makerjawn/oneKey/Documentation/indd/Links/10894171994_1b0bc88e4c_z.jpg

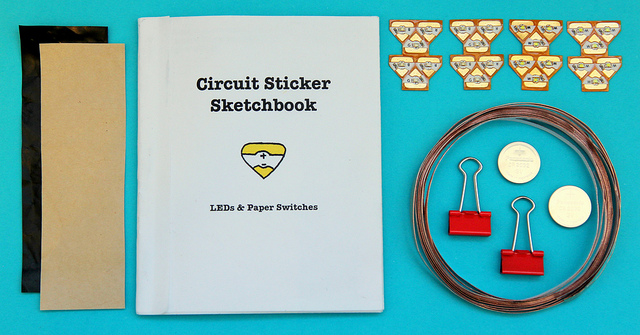
Documentation/indd/Links/10894171994_1b0bc88e4c_z.jpg
