makerjawn/oneKey/Documentation/Presentation_Intro_Handout.pdf

Case, Amber. An Illustrated Dictionary of Cyborg Anthropology. N.p.: n.p., n.d. Http:// cyborganthropology.com/store/. Web.
Dewey, John. Experience and Education. New York: Macmillan, 1938. Print.
Anderson, Chris. Makers: The New Industrial Revolution. New York: Crown Business, 2012. Print. Rushkoff, Douglas, and Leland Purvis. Program or Be Programmed: Ten Commands for a Digital Age. Berkeley, CA: Soft Skull, 2011. Print.
Brosterman, Norman, and Togashi. Inventing Kindergarten. [New York, N.Y.]: H.N. Abrams, 1997. Print.
Murakami, Haruki, and Jay Rubin. Norwegian Wood. New York: Vintage International, 2000. Print. Plowman, Lydia, Christine Stephen, and Joanna McPake. Growing up with Technology: Young Children Learning in a Digital World. London: Routledge, 2010. Print.
,W 0L]XNR +DQJLQJ 2XW 0HVVLQJ $URXQG DQG *HHNLQJ 2XW .LGV /LYLQJ DQG /HDUQLQJ ZLWK 1HZ Media. Cambridge, MA: MIT, 2010. Print.
1LOVVRQ (OLVDEHW 0 7KH 0DNLQJ RI D 0DNHUVSDFH IRU 2SHQ ,QQRYDWLRQ .QRZOHGJH 6KDULQJ DQG Peer-to-peer Learning." FUTURE LEARNING SPACES. Helsinki: Aalto University, 2011. 293-98. Print.
| Petrovich, Dushko, and Roger White. Draw It with Your Eyes Closed: The Art of the Art
Assignment. Brooklyn, NY: Paper Monument, 2012. Print.
| Allen, Felicity. Education. London: Whitechapel Gallery, 2011. Print.

https://pittsburghkids.org/exhibits/makeshophttp://www.libraryasincubatorproject.org/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

# Playing, Learning, and Making things light-up in

City of Brotherly Love and Sisterly Affection.

# To encourage exploration with, making of, and

collaboration on electronic interactives.

# MakerJawn

# IDES 431

bk

31 | 7 | 14

### Map comparison of online

resources/curriculum.

Reconnect with MESS Hall,
talk about new kits.

### Develop own curriculum based

on summer learning.

### Reevaluate summer blog and

feedback on tools.

### Run curriculum by Kenny and

K-Fai.

### Talk to Ann about implementing check-out/cart

### Make sketch kits, let them

be explored.

### 2EVHUYH NLW RU FDUW XVDJH

### Interview volunteers about

what they see in its usage.

### Condense “curriculum” into

kit interactives.

### Make report for proof of

concept / needed actions.

# timeline / actions

# works cited / resources

### Access existing kits at the library. (Boardgames, etc)

## Digital Media afterschool programming and workshops for

youth at the Free Library of Philadelphia.

keywords
connected learning, digital literacy, electronics, making, maker, library, resources, underserved, after-school, teens, programming, computing, technology, understanding, play, H[SORUDWLRQ ZRUNVKRSV HWH[WLOHV FUDIWLQJ DW WHDFKLQJ guided learning, participatory design, eorigami, hi-low tech, PLW PDNHUHG GLJLWDO PHGLD LQWHUQHW SURFLHQF\ VKDULQJ collaborating, exposure, computation, programming, kids, youth, arts, craft, empowering, failure, fabrication labs, fab labs, maker spaces, institutions, kit based.

NH\WHUPVGHQHG
electronic interactive - a digital media installation, ranging from a game, to a sculpture, or art work, XWLOL]LQJ HOHFWURQLFV DQG NQRZOHGJH RI FLUFXLWU\ DQG RU programming logic and syntax.
NLW D VHW RI SDUWV RU WKLQJV IRU D VSHFLF SXUSRVH framework - structure
scaffolding learning - to tier or create stepping stones so concepts and knowledge can be built upon within a learning environment.
HASTAC - Humanities, Arts, Science and Technology Advanced Collaboratory

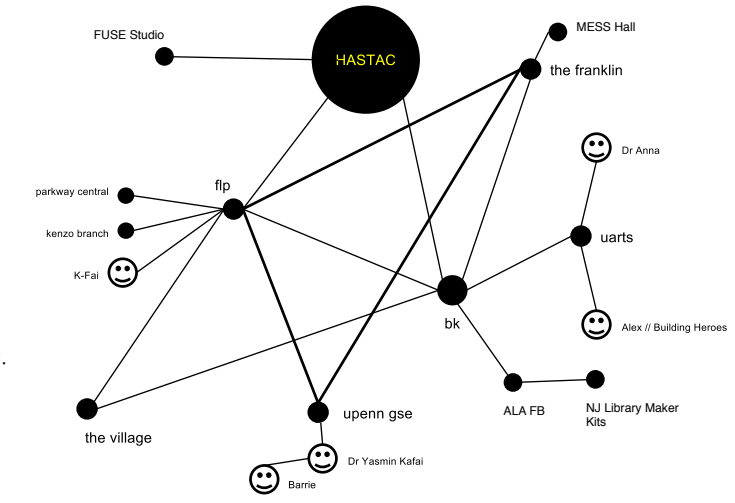
[picture p3: figure]
ALA FB; MESS Hall FUSE Studio; NJ Library Maker Kits

OLEUDU\PDNHUSUROHV | OLWHUDU\UHYLHZQGLQJV

# SUHFHGHQWNLWV

MESS Kits
“Single-serving
experiments that allow
NLGV WR H[SORUH VFLHQWLF
concepts at their own
pace.” Checked out and
updated frequently with
simple chemistry, physics, and crafts projects.

Sparkfun
Nationally tested and
XWLOL]HG FXUULFXOXP IRU
scafolding learning with
regards to electronics,
physical computing, and
programming.

Fuse Studio
2QOLQH GURSLQ
model, inquiry based,
STEAM(Science,
Technology, Engineering,
Arts, and Math) centric
design-build challenges.
Free to the public, sans
physical project materials.

NJ Maker Kits
Three kits ranging
from button makers to
MakeyMakeys. Can be
checked out at branches,
comes with minimal
guidance for branch users
other than online product
guides.

In order to make a framework for scafolding the learning of youth at the library a FXUULFXOXP RI VRUWV PXVW EH ZRUNHG RXW $V VSHFLFDOO\ PRGHOHG E\ 0(66 NLWV DQG FUSE Studio they do not have to be completed sequentially.

Sparkfun on the otherhand has a very linear approach to its lessonplans, one may H[SORUH LQWHUHVWLQJ FRPSRQHQWV RU SLHFHV RI WKH SX]]OH MXVW OLNH /LJKW8S +RZHYHU if exploration occurs in these platforms their preplanned linear execution is QXOOLHG

These precedents can be remixed and mashed-up to work within the library, KRZHYHU WKH\UH QRW WDLORUHG WRZDUGV WKH VSHFLF FRQWH[WV DQG HQYLURQPHQWV WKH library has to offer.

In my readings I have found that youth are bound to be creative and explore concepts through unrestricted play. In the context of the library I must be sensitive to how the community, family, and actual child view and interact with technology and electronics. Their own thoughts will completely differ from mine when it comes to its use for , entertainment, etc. The beauty of digital media is that it is able to freely move around, which can either allow for easy entertainment or HVFDSH RU XLG WUDQVIHU RI LGHDV DQG SURMHFW VKDULQJ , KDYH DOVR OHDUQHG WR VSHFLFDOO\ FDWHJRUL]H QRW RQO\ the needs or ways in which youth learn(inquiry based, play, directed learning, etc), but also their involvement in the programming.

As stated in Ito, there are three primary ways in which kids will align with digital media programming. They can either just hang out DQG VRFLDOL]H mess around with what is being worked on, or they can totally latch on to the project and geek out ZKLOH FRQWULEXWLQJ WR D QDO solution.

Jacob
13 years old
“The Boss”
// Self-directed tinkerer
// Geeking out
Mykal
9 Years old
“the best student”
// Needs guidance
// Messing around
Donnie
10 years old
“gamer”
// Self-directed
// Hanging out
Star
11 years old
“maker + doer”
// Self Directed
0HVVLQJ $URXQG DQG +DQJLQJ 2XW

# P\SRVLWLRQDWS

# SUHFHGHQWSUHYLRXVO\WHVWHGWKRXJKWV

Possibility Box
A box full of projects
chosen by MAKER.ED of
MAKE media for mentors to
explore with students. An
unfocused set of basics.

# OLEUDU\VWUXFWXUHYRWKHUPHWKRGV

&RQQHFWHG0HVVDJHV
A collaborative, multiple
location, interactive mural project completed at the
library over the Summer
‘13.

MakeyMakey Mazes
A gateway from simple
circuitry to basic
programming with magnets
and playdoh.

# SUHFHGHQWLQWHUDFWLYHFROODERUDWLRQV

Maker Celebration Games
A set of games made for
3L]]D%UDLQ DQG /LWWOH%DE\V for the maker celebration
in collaboration with kids at the Village.

ECrafting

GSE Grads

TOPPS

MakerJawn

Teen
Programming
Specialists

Hot Spots

Maker
Mentors
I am currently a Maker Mentor underneath the Teen 2ULHQWHG 3URJUDPPLQJ JURXS KRXVHG DW WKH )UHH /LEUDU\ I am a direct link between Programming Specialists and other Mentors and interested parties at the library. I bring technical knowledge and critical feedback via implementing and testing progams and workshops.
As well as HASTAC scholar and collaborator.

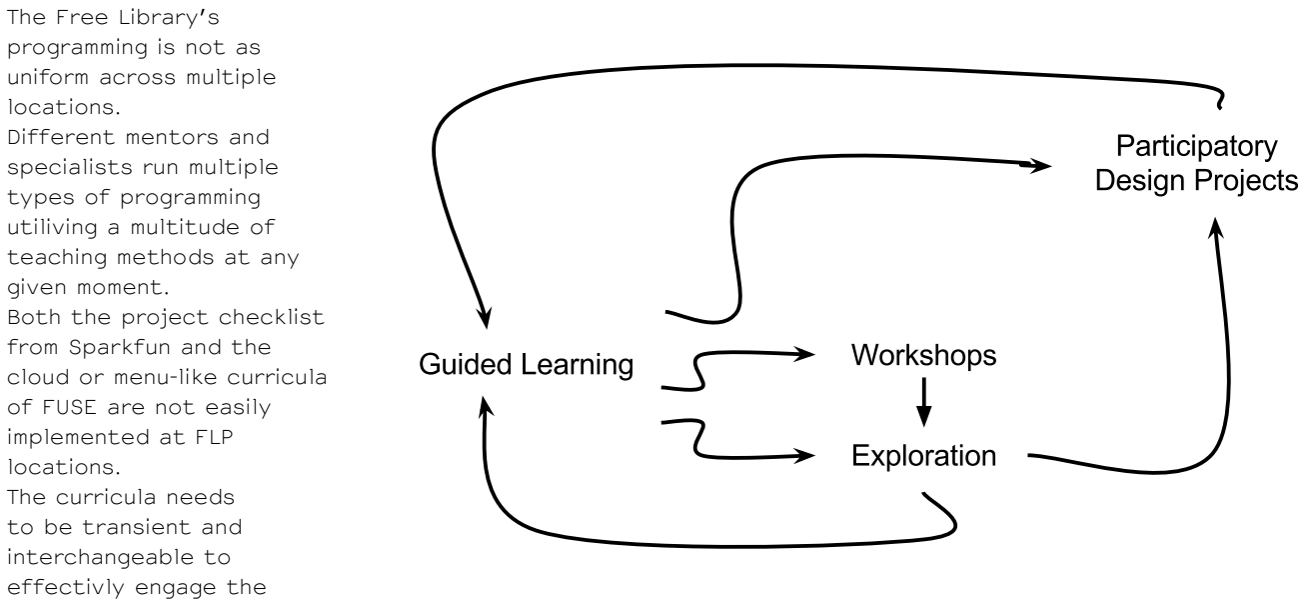
[picture p4: figure]
The Free Library’s programming is not as uniform across multiple locations. Different mentors and specialists run multiple types of programming utiliving a multitude of teaching methods at any given moment. Both the project checklist from Sparkfun and the cloud or menu-like curricula of FUSE are not easily implemented at FLP locations. The curricula needs to be transient and interchangeable to effectivly engage the

Library’s youth.
