makerjawn/oneKey/Documentation/Presentation_PetchaKutcha.pdf

bk

MakerJawn

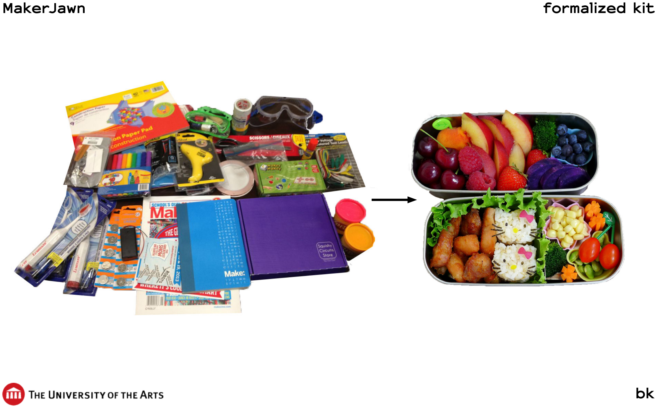
[picture p5: page 2]

bk

MakerJawn | formalized kit

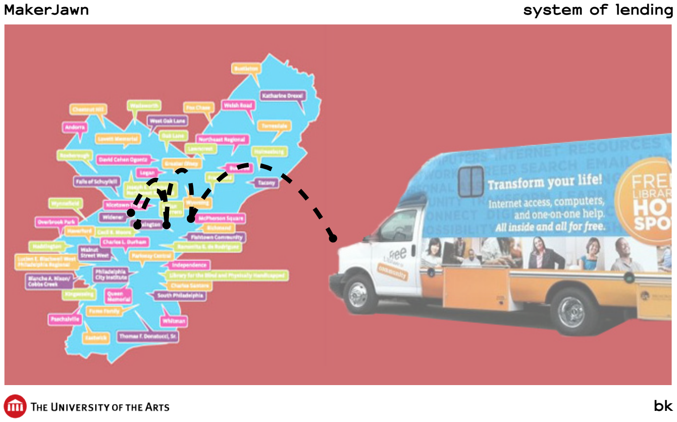
[picture p6: page 3]

bk

MakerJawn | system of lending

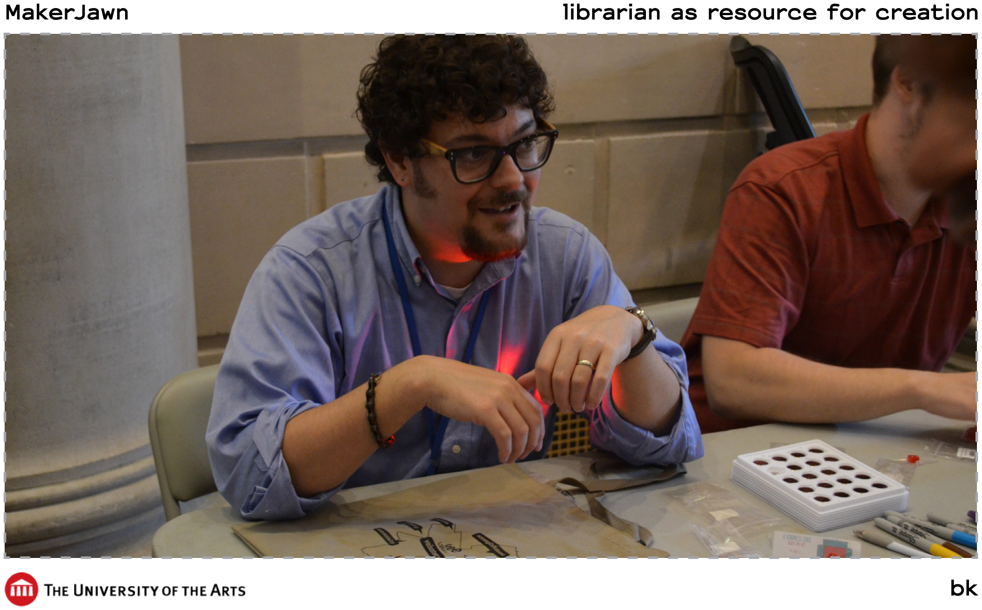
[picture p7: page 4]

bk

MakerJawn | librarian as resource for creation

bk

MakerJawn | instructional materials

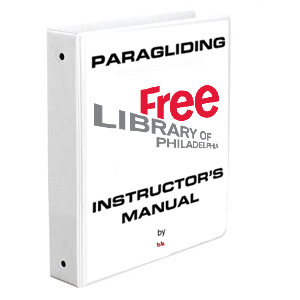
[picture p8: figure]

bk

MakerJawn | online resource for libraries

http://www.smh.com.au/ffximage/2005/09/19/wiki_web_C.jpg

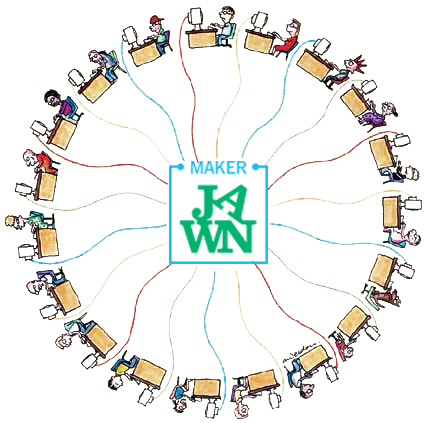
[picture p9: figure]
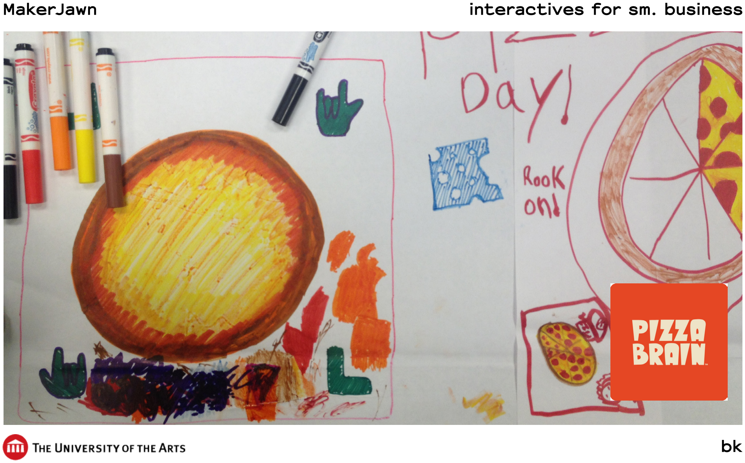
[picture p10: page 7]

bk

MakerJawn | interactives for sm. business

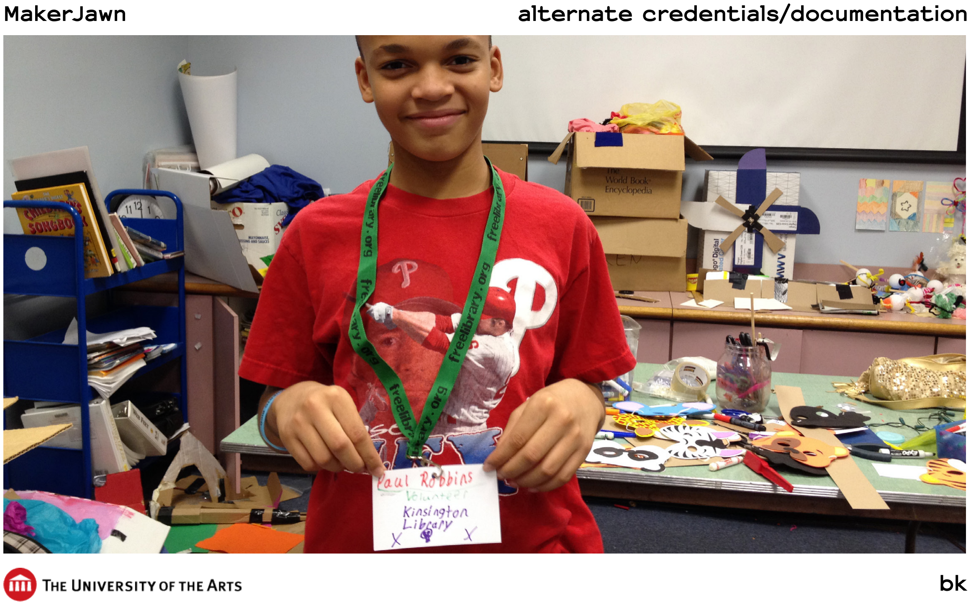
[picture p11: page 8]

bk

MakerJawn | alternate credentials/documentation

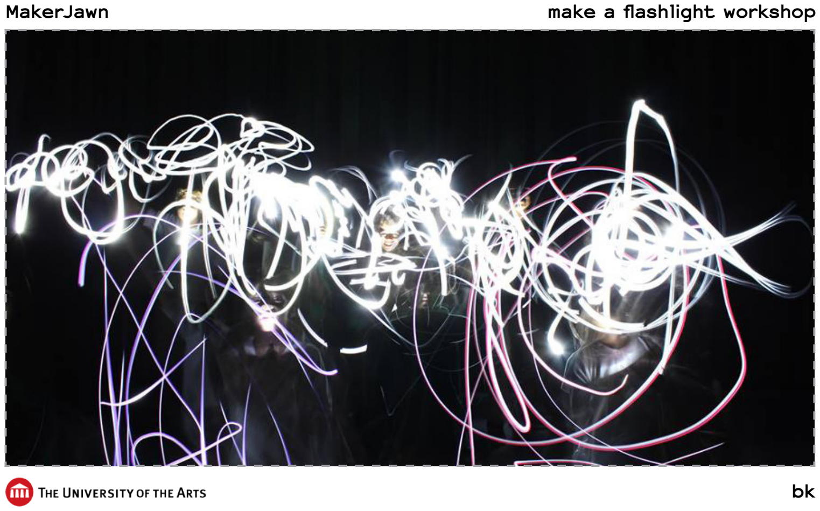
[picture p12: page 9]

bk

MakerJawn | make a flashlight workshop

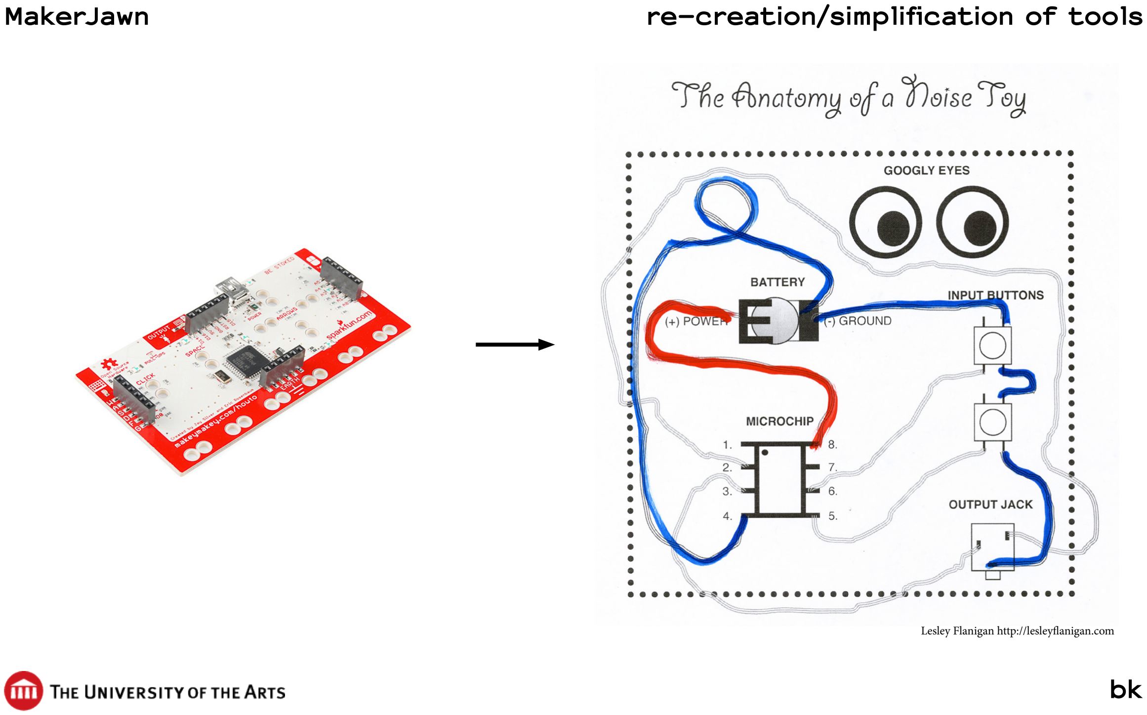
[picture p13: page 10]

bk

MakerJawn | re-creation/simplification of tools

Lesley Flanigan http://lesleyflanigan.com

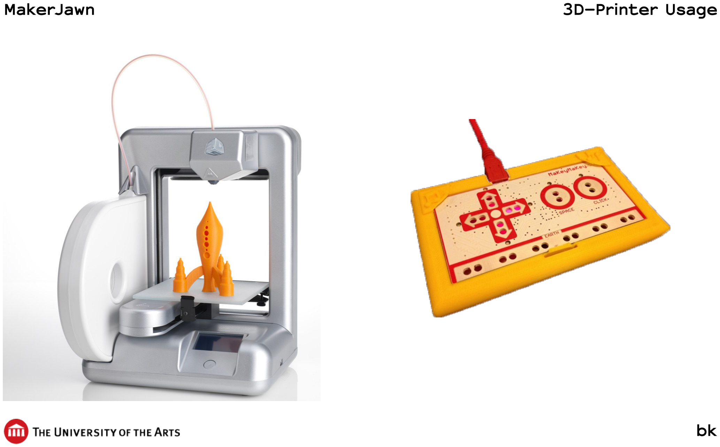
[picture p14: page 11]

bk

MakerJawn | 3D-Printer Usage
