makerjawn/oneKey/Documentation/Research_Funny.pdf

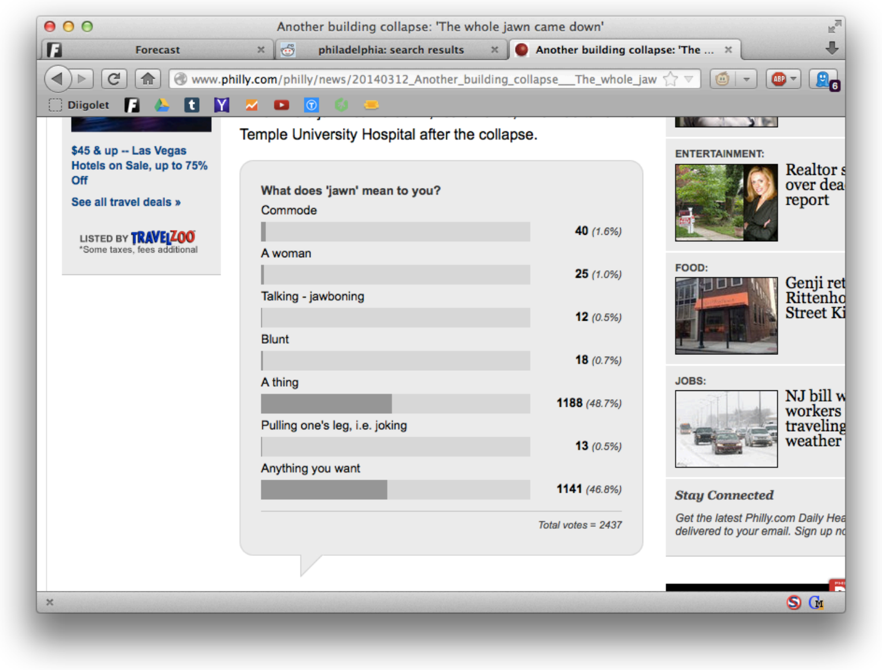
[picture p15: page 1]
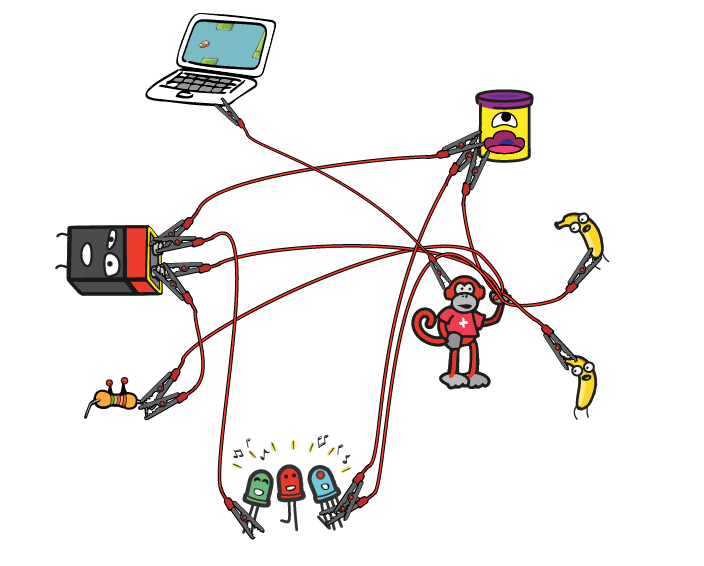
[picture p16: page 2]
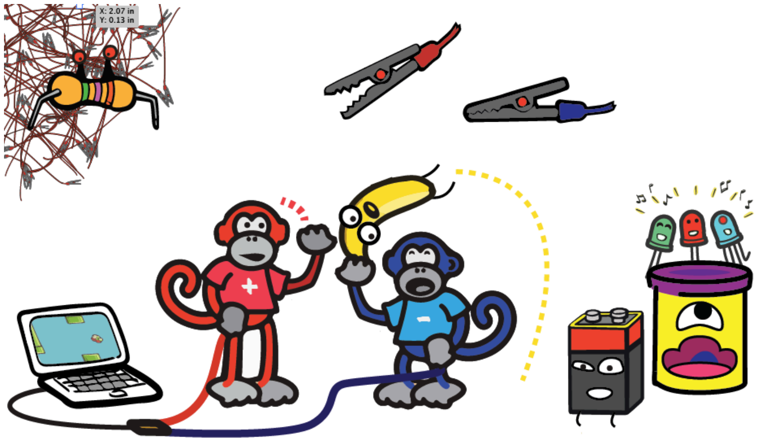
[picture p17: page 3]
