makerjawn/oneKey/Documentation/Research_Scans.pdf

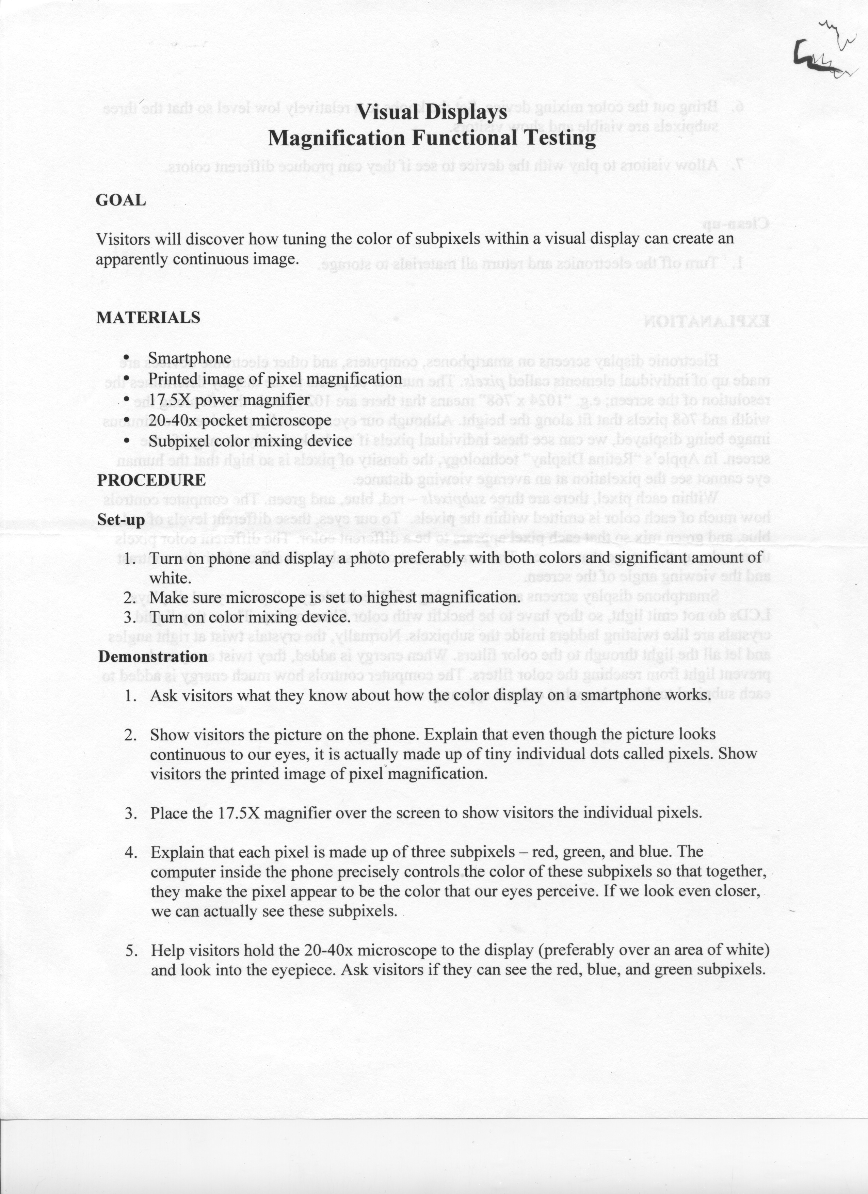
[picture p18: page 1]
