makerjawn/oneKey/Documentation/indd/Links/1280px-The_Free_Library_of_Philadelphia.jpg

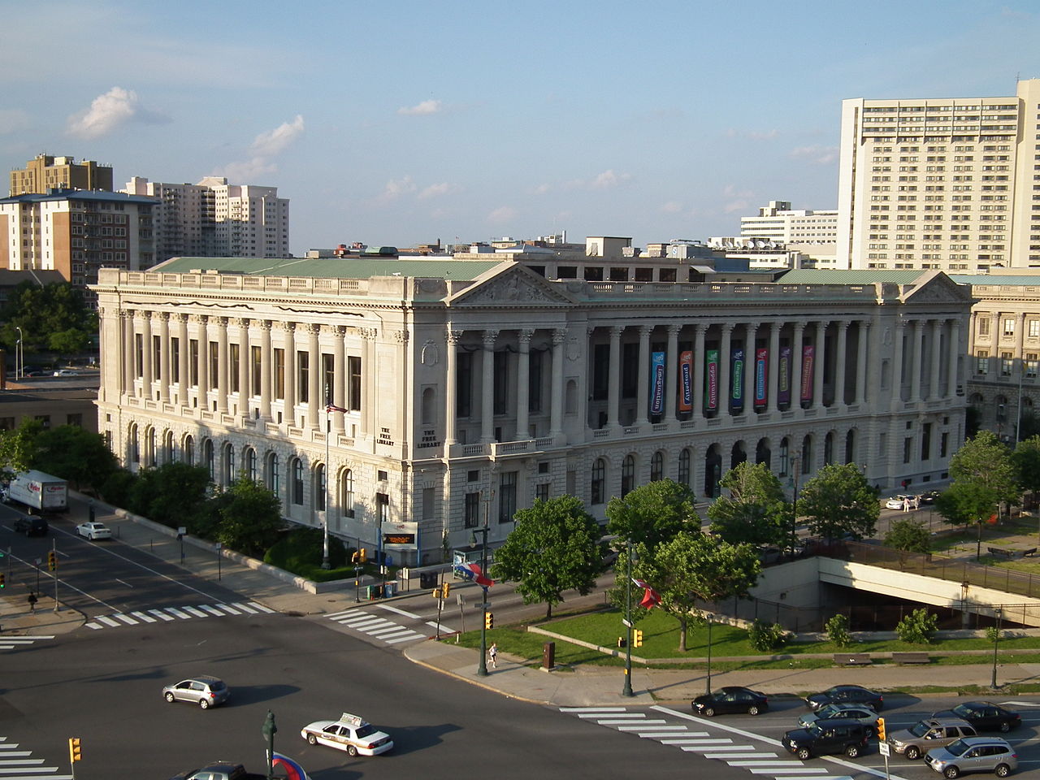
Documentation/indd/Links/1280px-The_Free_Library_of_Philadelphia.jpg
