makerjawn/oneKey/Documentation/indd/Links/2014-02-12 15.35.41 copy.jpg

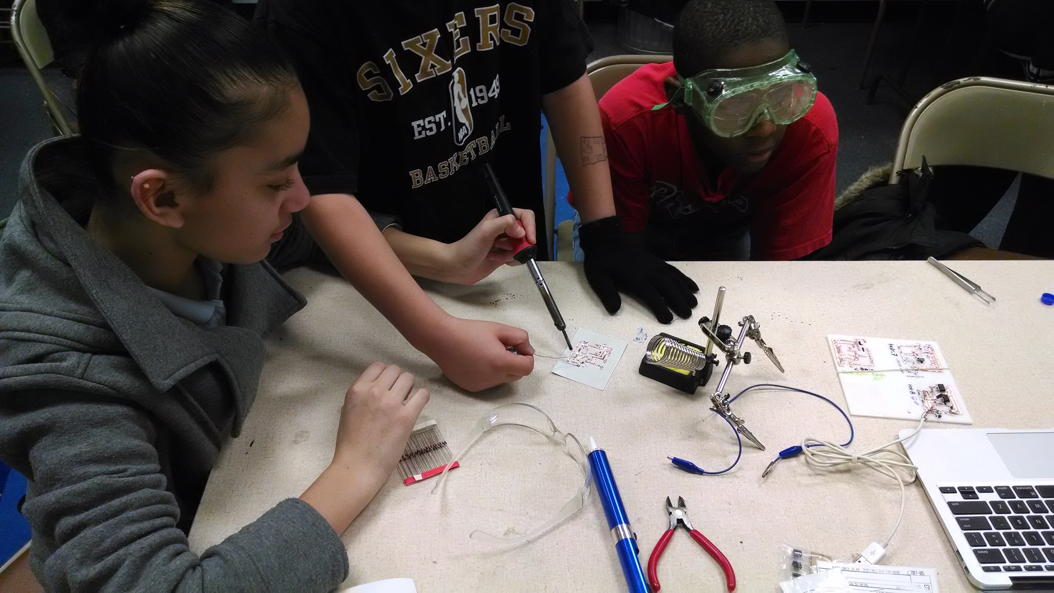
Documentation/indd/Links/2014-02-12 15.35.41 copy.jpg
