makerjawn/oneKey/Documentation/indd/Links/2014-02-12 16.28.50.jpg

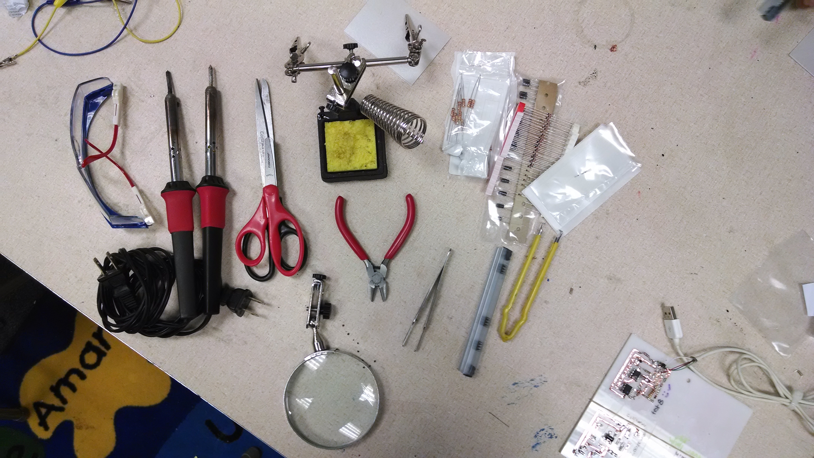
Documentation/indd/Links/2014-02-12 16.28.50.jpg
