makerjawn/oneKey/Documentation/indd/Links/2014-02-12 16.29.10.jpg

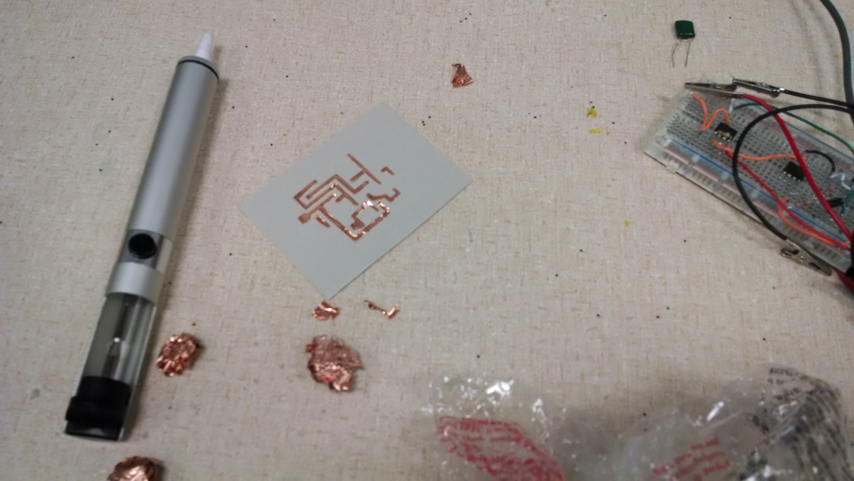
Documentation/indd/Links/2014-02-12 16.29.10.jpg
