makerjawn/oneKey/Documentation/indd/Links/22222.jpg

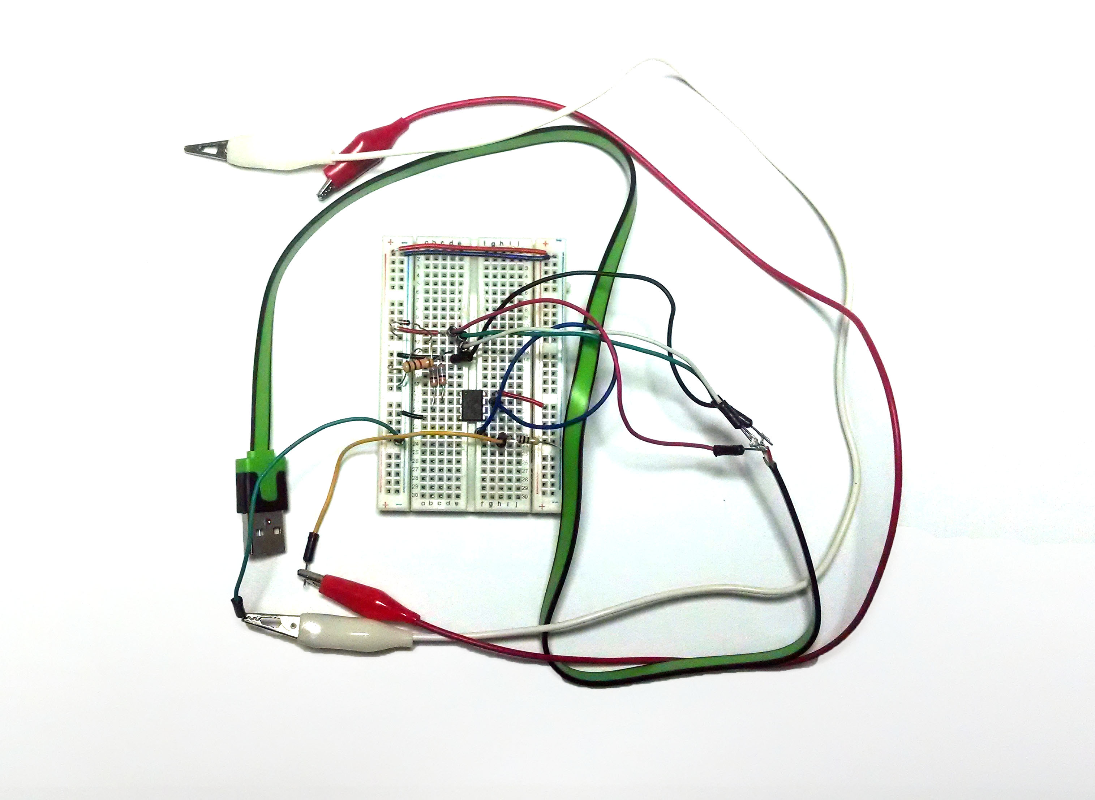
Documentation/indd/Links/22222.jpg
