makerjawn/oneKey/Documentation/indd/Links/48112_10151742160433617_1879008240_n.jpg

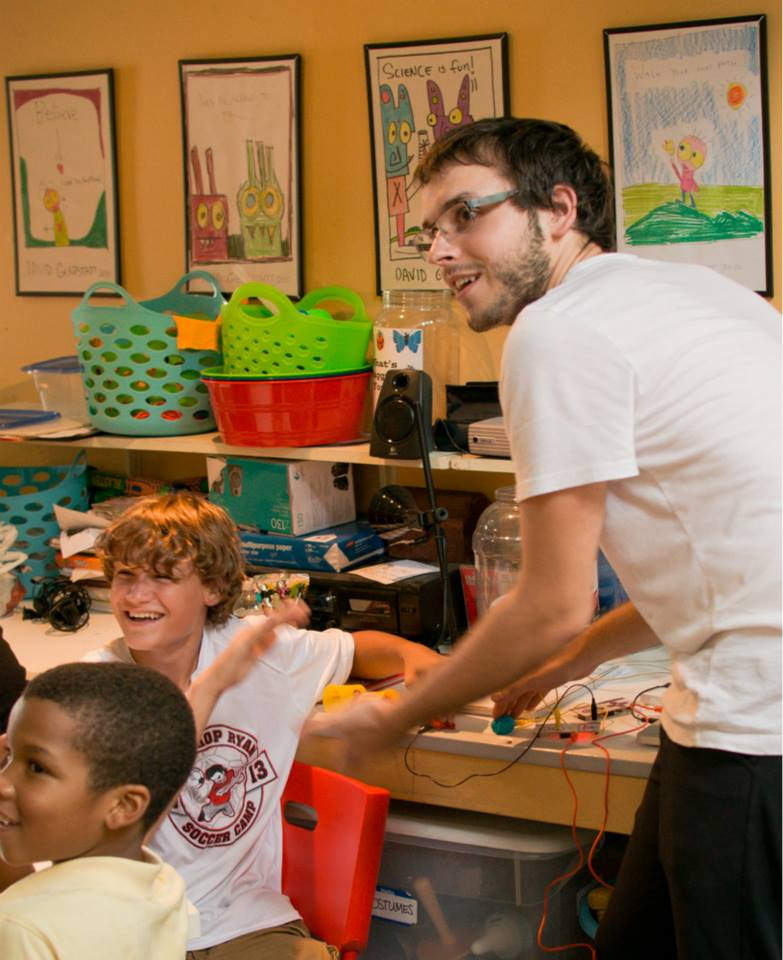
Documentation/indd/Links/48112_10151742160433617_1879008240_n.jpg
