makerjawn/oneKey/Documentation/indd/Links/63999_3661341067192_615782016_n.jpg

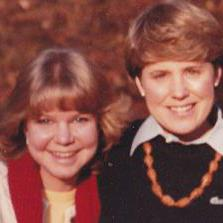
Documentation/indd/Links/63999_3661341067192_615782016_n.jpg
