makerjawn/oneKey/Documentation/indd/Links/644108_10200095397942770_120919890_n.jpg

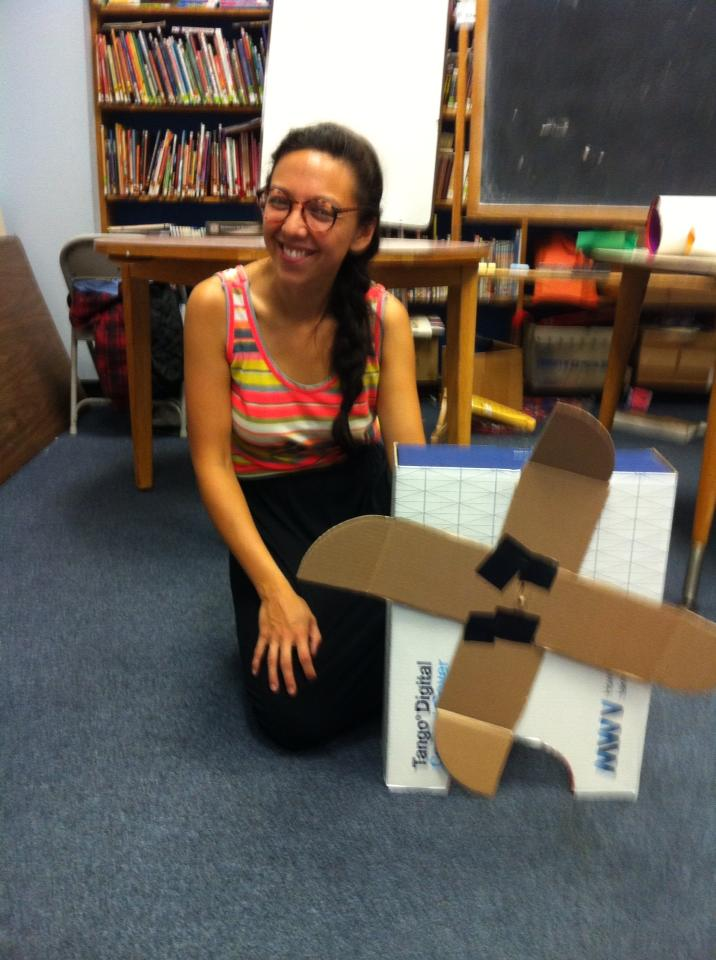
Documentation/indd/Links/644108_10200095397942770_120919890_n.jpg
