makerjawn/oneKey/Documentation/indd/Links/1002581_10151742165138617_1287165693_n.jpg

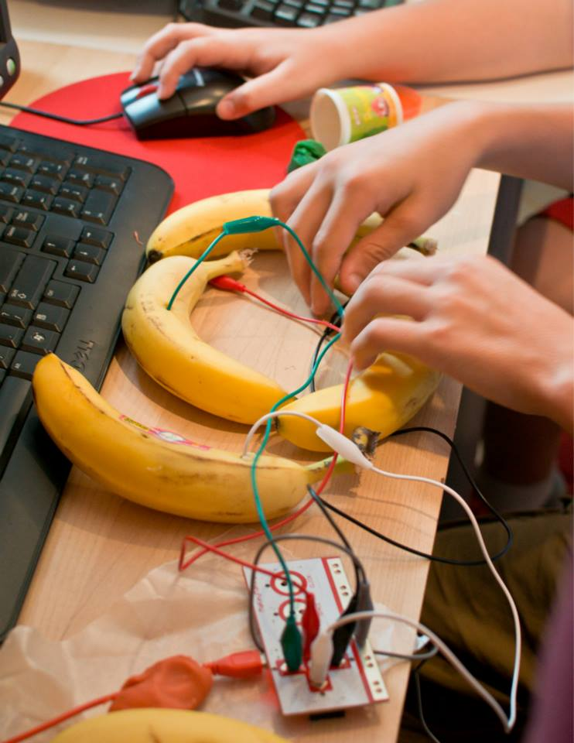
Documentation/indd/Links/1002581_10151742165138617_1287165693_n.jpg
