makerjawn/oneKey/Documentation/indd/Links/1098084_10151742164978617_1691088811_n.jpg

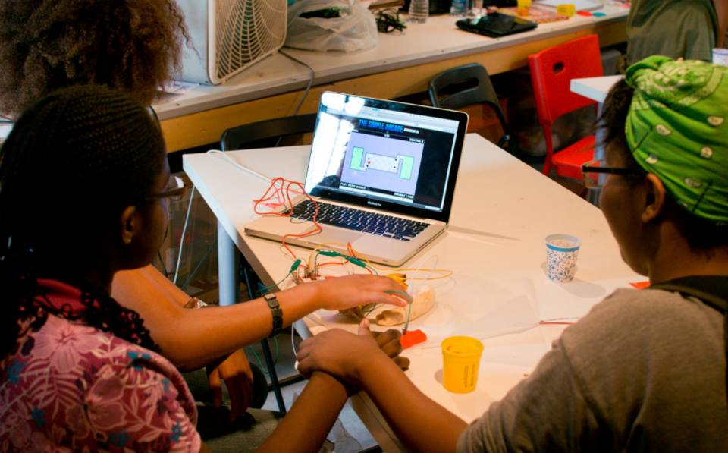
Documentation/indd/Links/1098084_10151742164978617_1691088811_n.jpg
