makerjawn/oneKey/Documentation/indd/Links/4251202735_0169829143_o.jpg

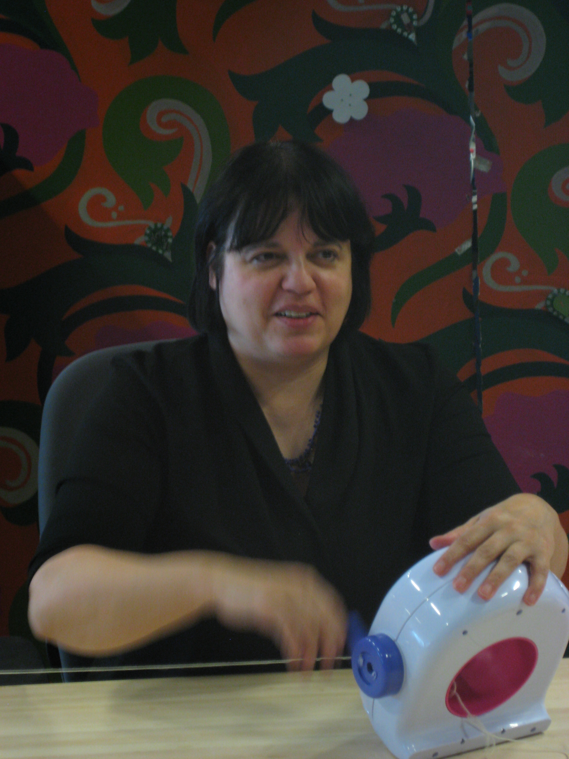
Documentation/indd/Links/4251202735_0169829143_o.jpg
