makerjawn/oneKey/Documentation/indd/Links/9532364705_ae32d727b3_k.jpg

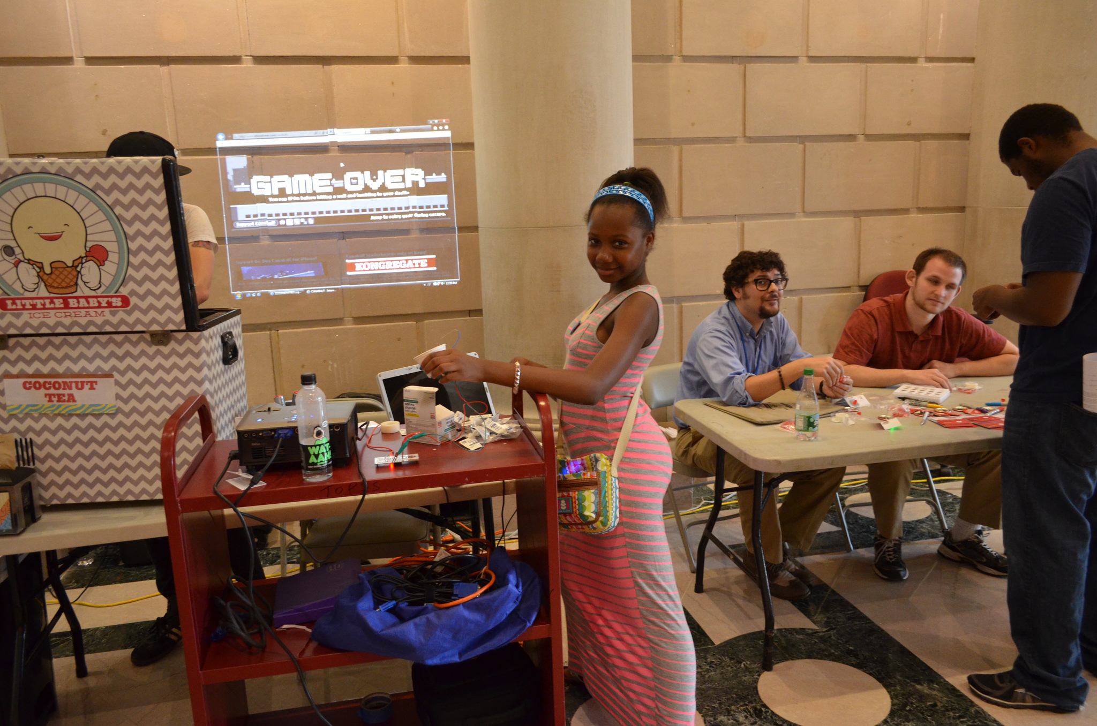
Documentation/indd/Links/9532364705_ae32d727b3_k.jpg
