makerjawn/oneKey/Documentation/indd/Links/9535104062_41edfae5f3_h.jpg

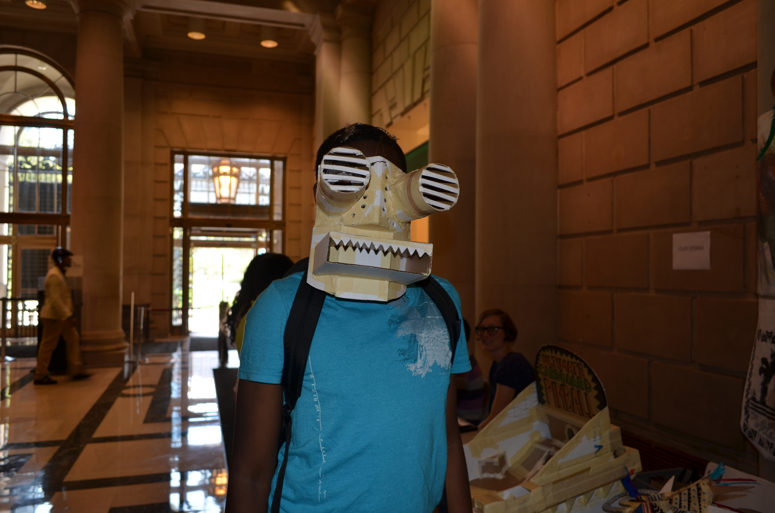
Documentation/indd/Links/9535104062_41edfae5f3_h.jpg
