makerjawn/oneKey/Documentation/indd/Links/9919182235_5fd875d8b7_o.jpg

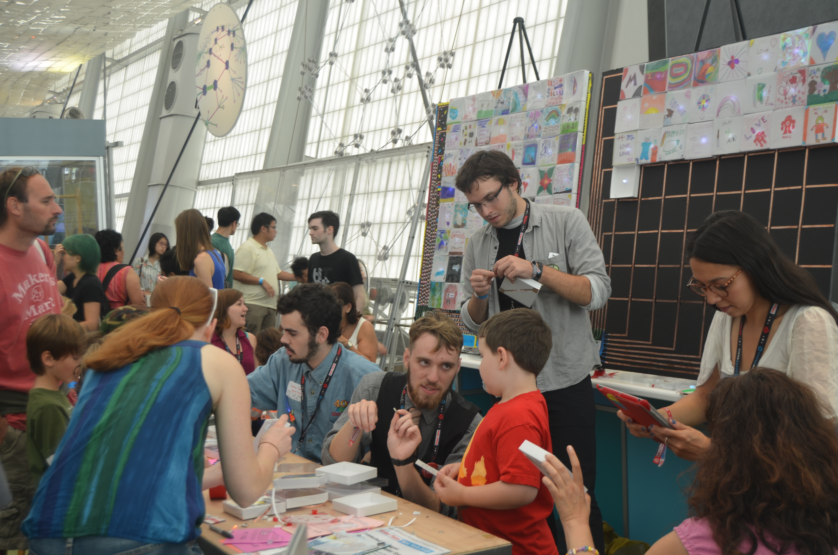
Documentation/indd/Links/9919182235_5fd875d8b7_o.jpg
