makerjawn/oneKey/Documentation/indd/Links/9919227815_236591e991_b copy.jpg

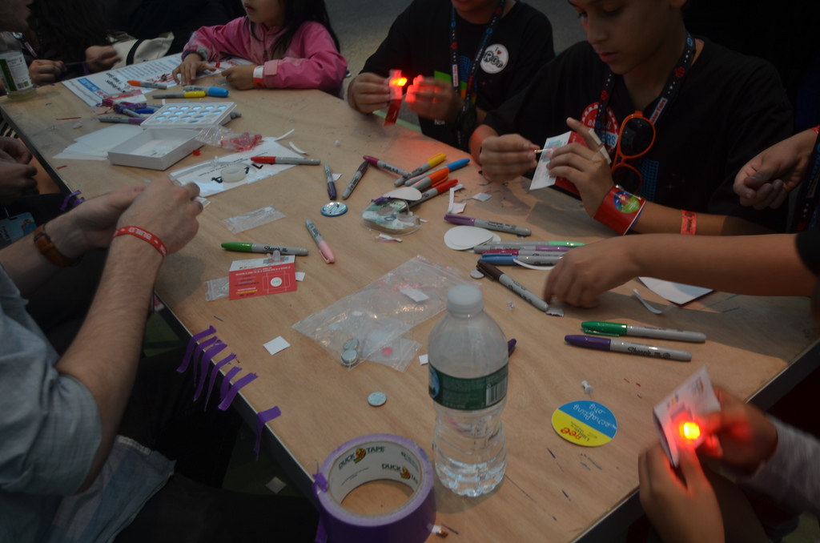
Documentation/indd/Links/9919227815_236591e991_b copy.jpg
