makerjawn/oneKey/Documentation/indd/Links/9919325433_4978abfb9a_b.jpg

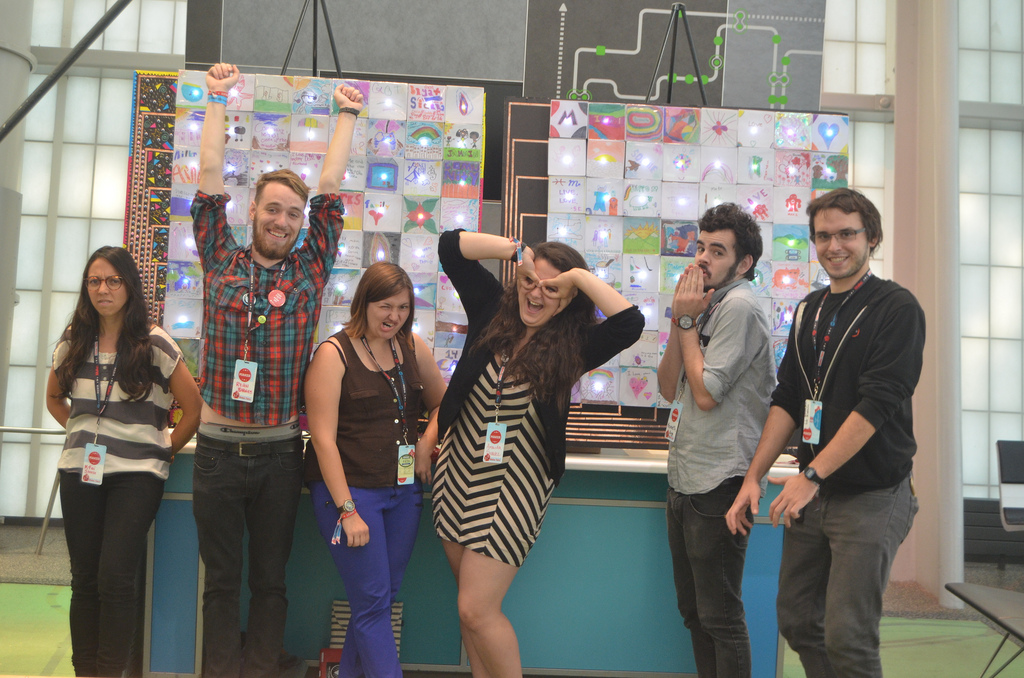
Documentation/indd/Links/9919325433_4978abfb9a_b.jpg
