makerjawn/oneKey/Documentation/indd/Links/10284768625_5c0d609d14_o.jpg

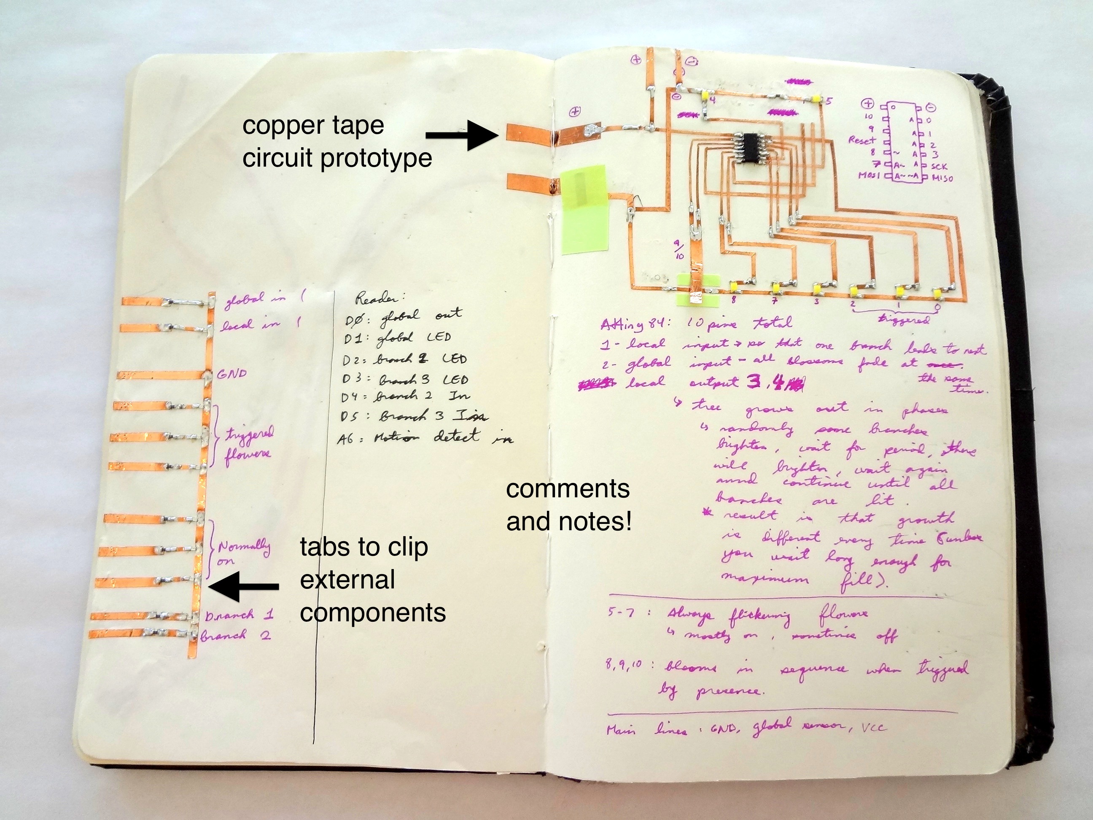
Documentation/indd/Links/10284768625_5c0d609d14_o.jpg
