makerjawn/oneKey/Documentation/indd/Links/10782753586_27ef463d22_b.jpg

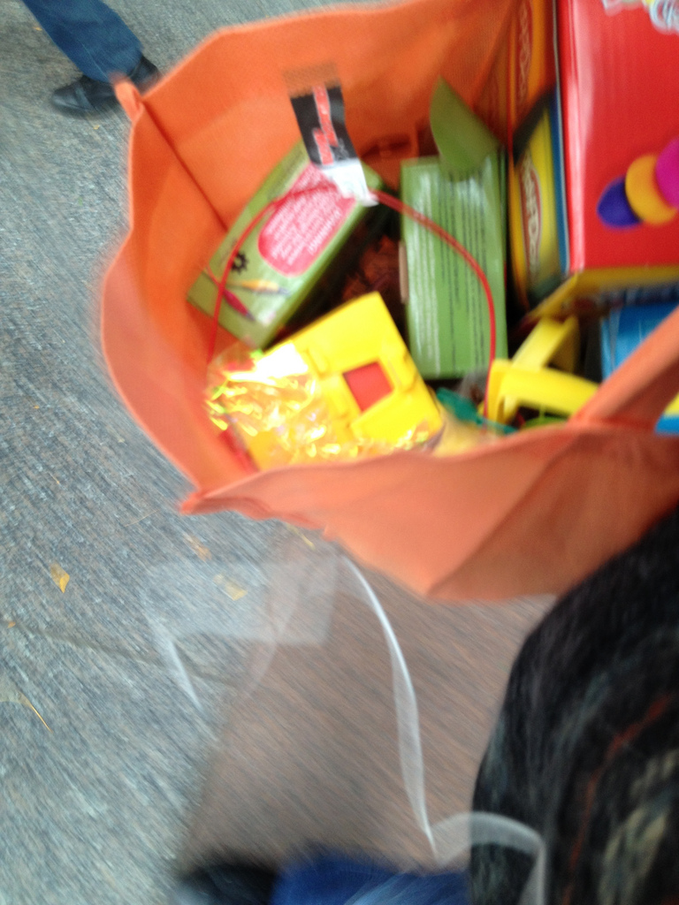
Documentation/indd/Links/10782753586_27ef463d22_b.jpg
