makerjawn/oneKey/Documentation/indd/Links/10782835374_39fd463c4d_b.jpg

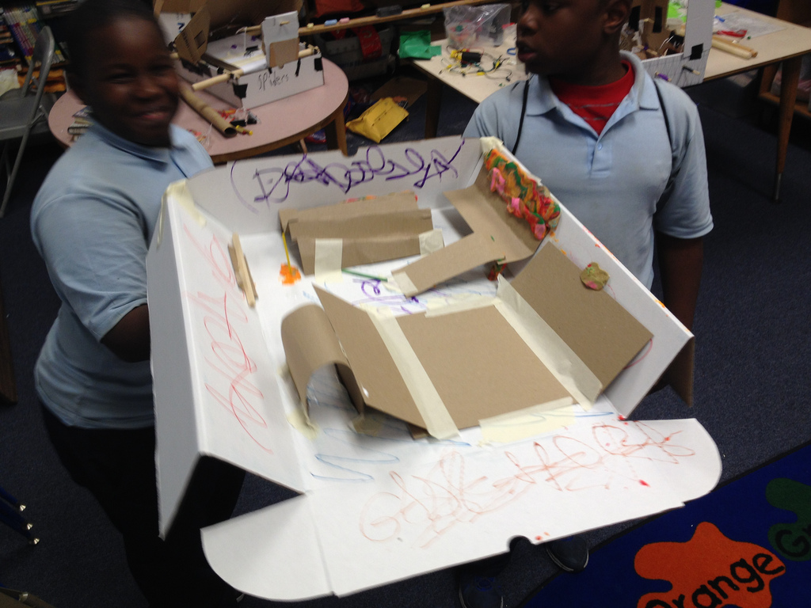
Documentation/indd/Links/10782835374_39fd463c4d_b.jpg
