makerjawn/oneKey/Documentation/indd/Links/10784261616_f2d67cabc5_b.jpg

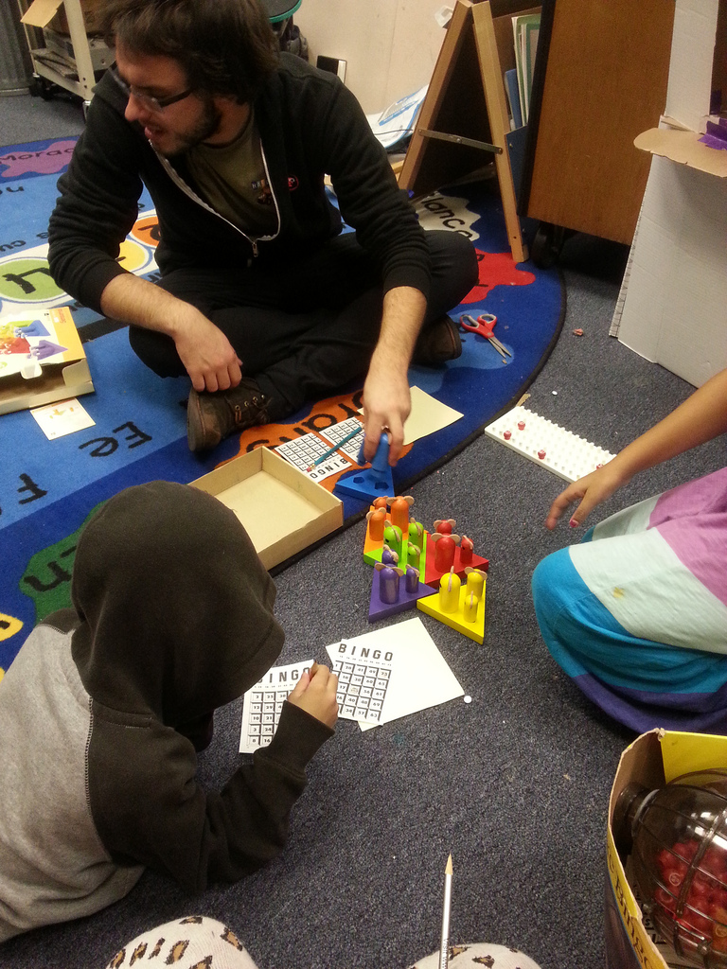
Documentation/indd/Links/10784261616_f2d67cabc5_b.jpg
