makerjawn/oneKey/Documentation/indd/Links/10801737194_b5118226d8_b.jpg

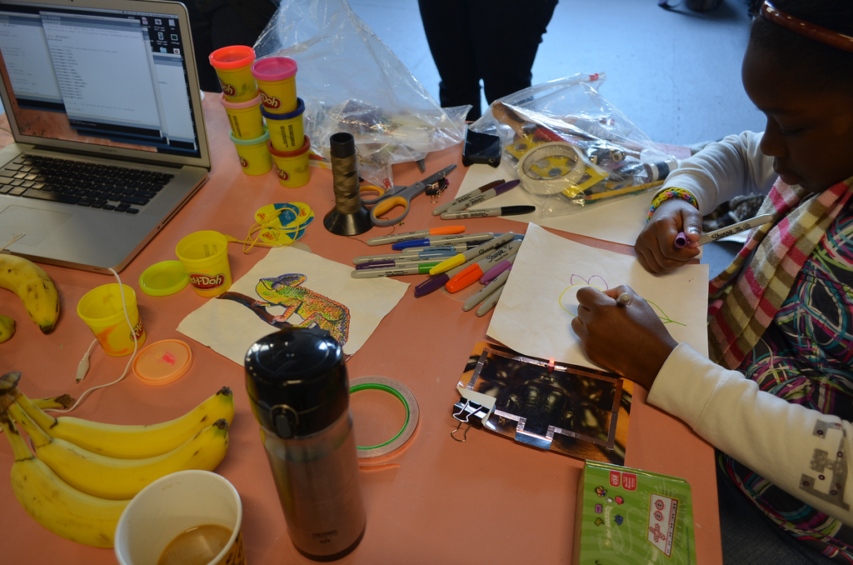
Documentation/indd/Links/10801737194_b5118226d8_b.jpg
