makerjawn/oneKey/Documentation/indd/Links/10847830253_bd08098483_b.jpg

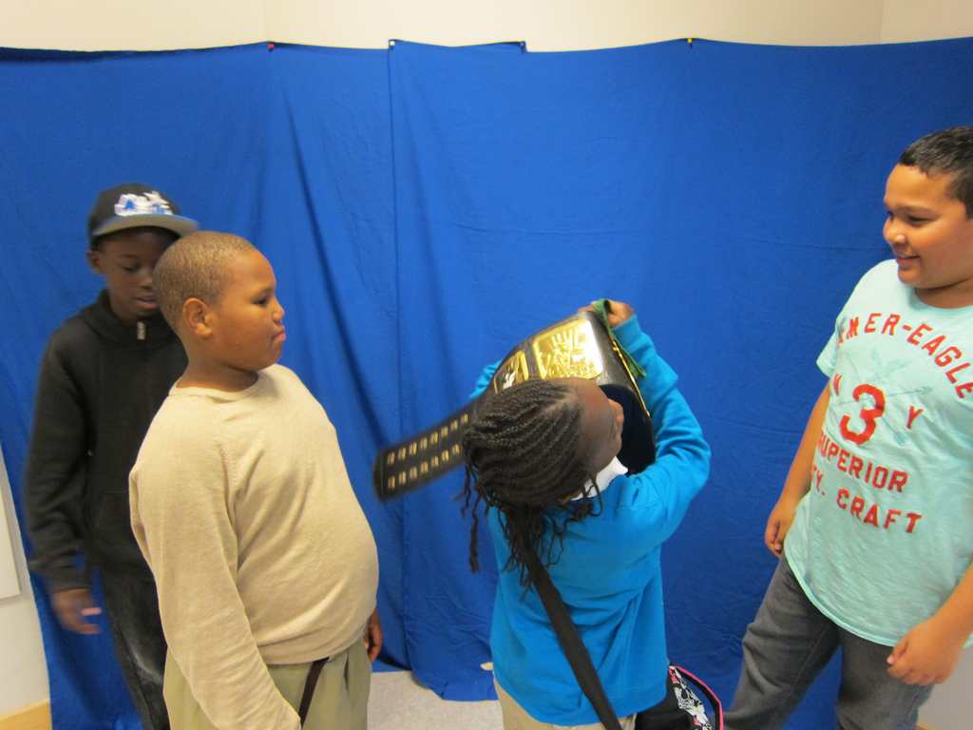
Documentation/indd/Links/10847830253_bd08098483_b.jpg
