makerjawn/oneKey/Documentation/indd/Links/10855527056_44a5891f57_o.jpg

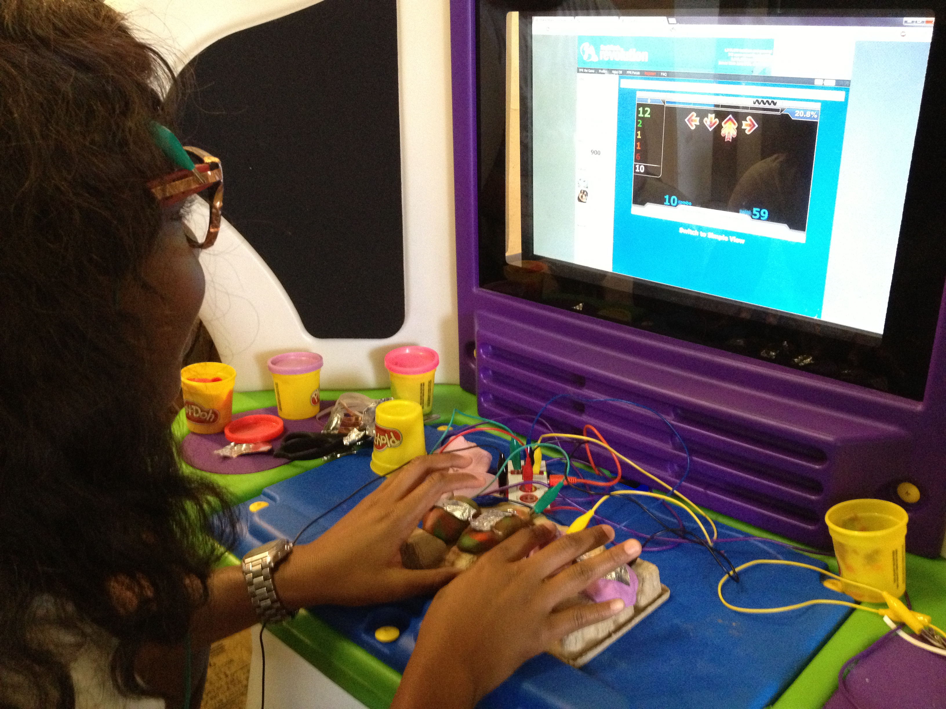
Documentation/indd/Links/10855527056_44a5891f57_o.jpg
