makerjawn/oneKey/Documentation/indd/Links/10855620776_20b71840e3_o.jpg

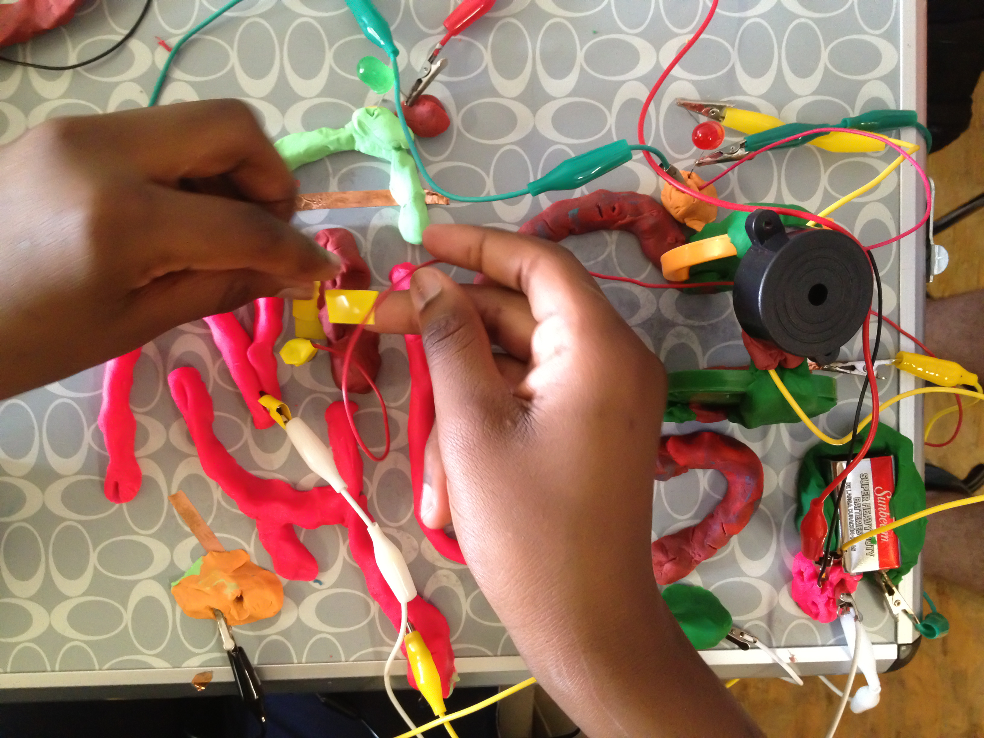
Documentation/indd/Links/10855620776_20b71840e3_o.jpg
