makerjawn/oneKey/Documentation/indd/Links/10855629604_a8a7b03be3_o.jpg

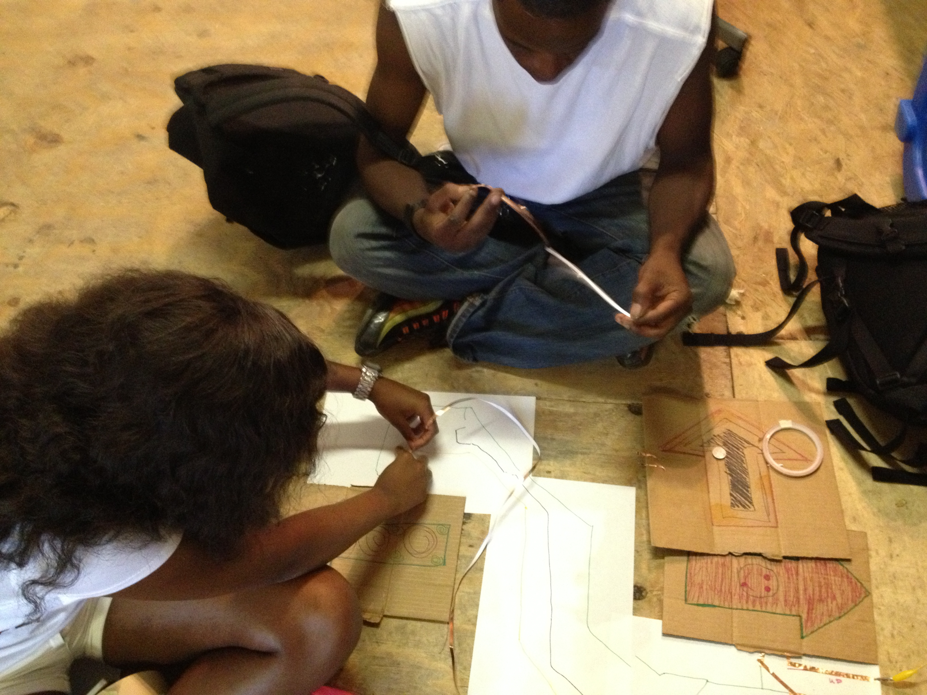
Documentation/indd/Links/10855629604_a8a7b03be3_o.jpg
