makerjawn/oneKey/Documentation/indd/Links/10864689754_e67436391c_o.jpg

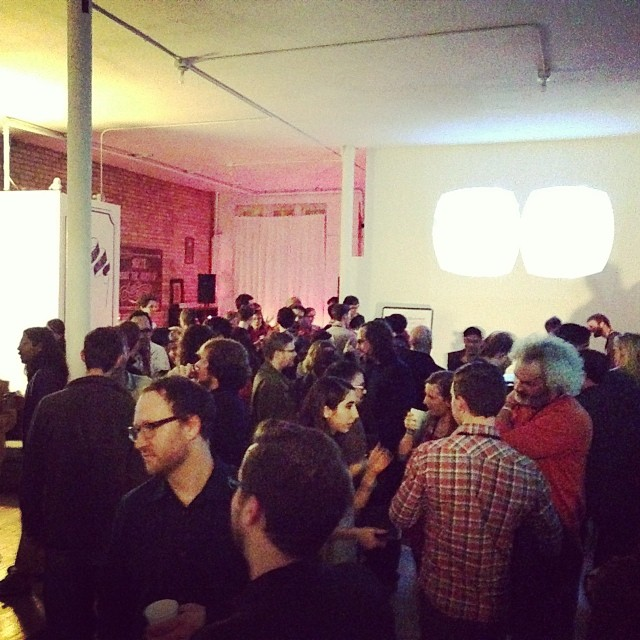
Documentation/indd/Links/10864689754_e67436391c_o.jpg
