makerjawn/oneKey/Documentation/indd/Links/10865232316_e09d01e575_o.jpg

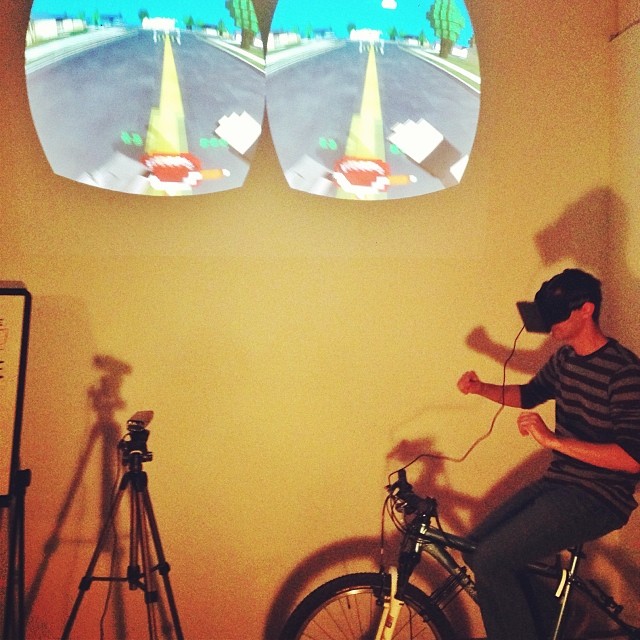
Documentation/indd/Links/10865232316_e09d01e575_o.jpg
