makerjawn/oneKey/Documentation/indd/Links/10872914816_8a091948d0_o.jpg

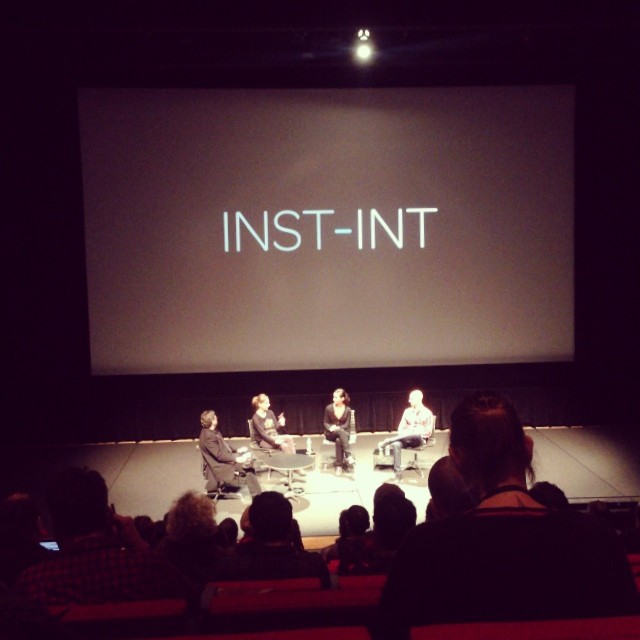
Documentation/indd/Links/10872914816_8a091948d0_o.jpg
