makerjawn/oneKey/Documentation/indd/Links/10935512513_ae5b8e6751_b.jpg

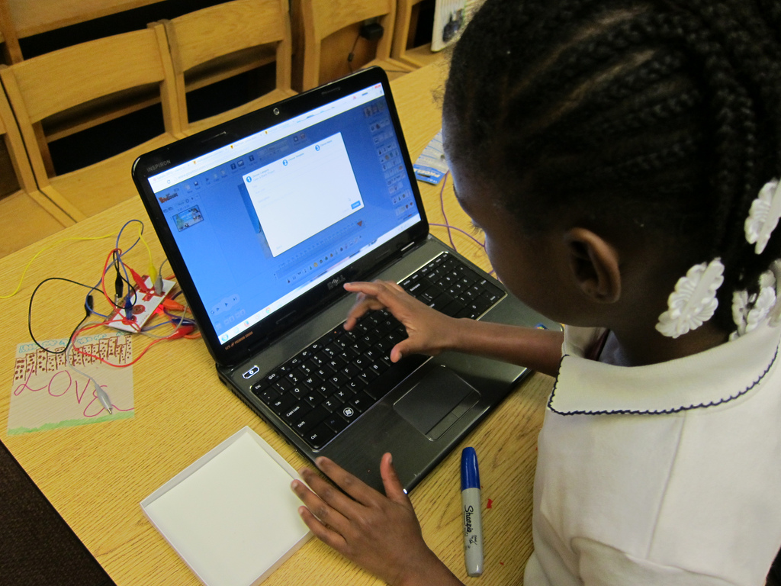
Documentation/indd/Links/10935512513_ae5b8e6751_b.jpg
