makerjawn/oneKey/Documentation/indd/Links/10997848584_e9f93355ee_b.jpg

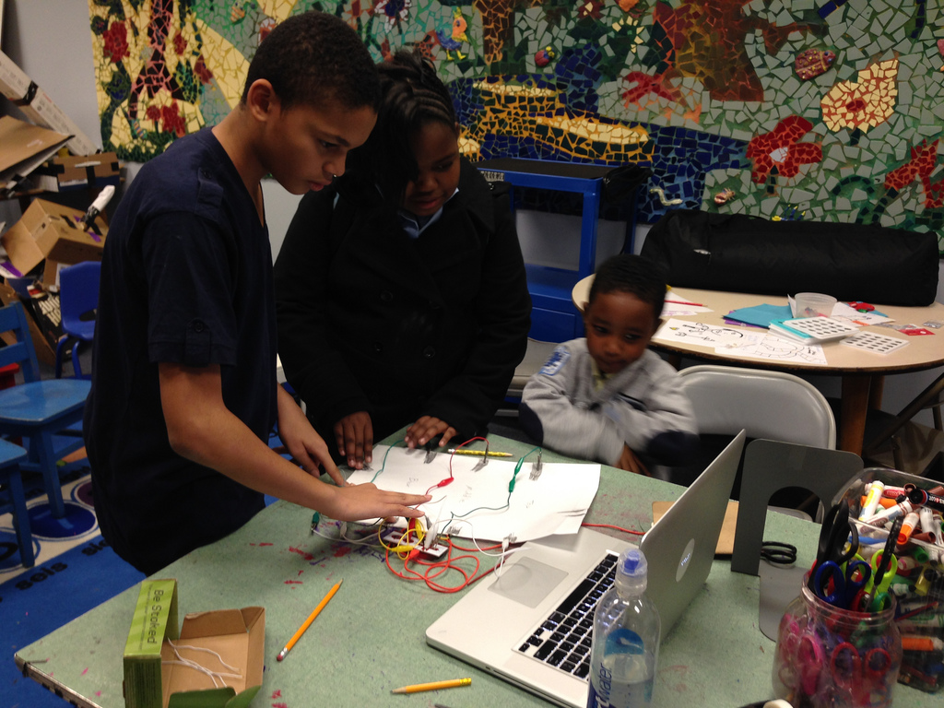
Documentation/indd/Links/10997848584_e9f93355ee_b.jpg
