makerjawn/oneKey/Documentation/indd/Links/10997864084_3d64a8d72d_b.jpg

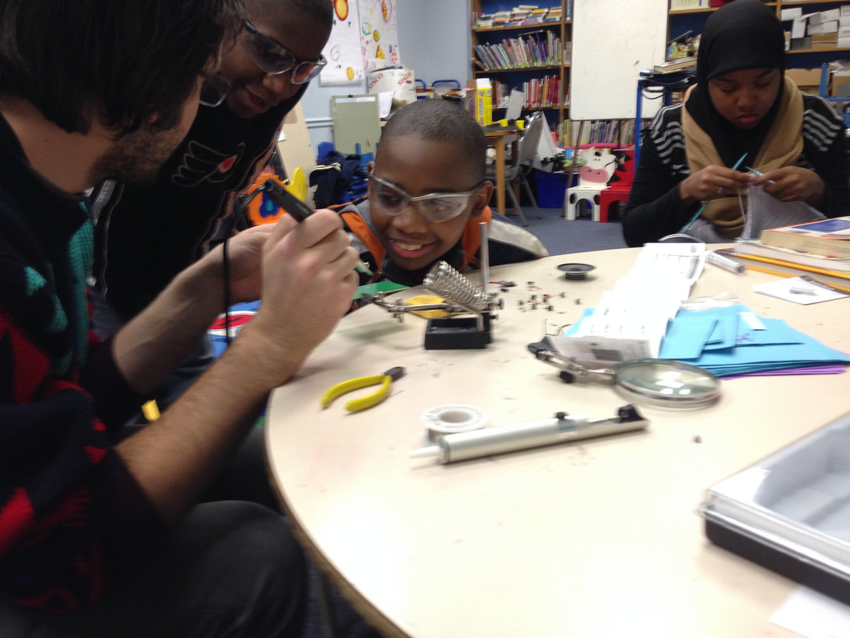
Documentation/indd/Links/10997864084_3d64a8d72d_b.jpg
