makerjawn/oneKey/Documentation/indd/Links/11001480965_706395af89_b.jpg

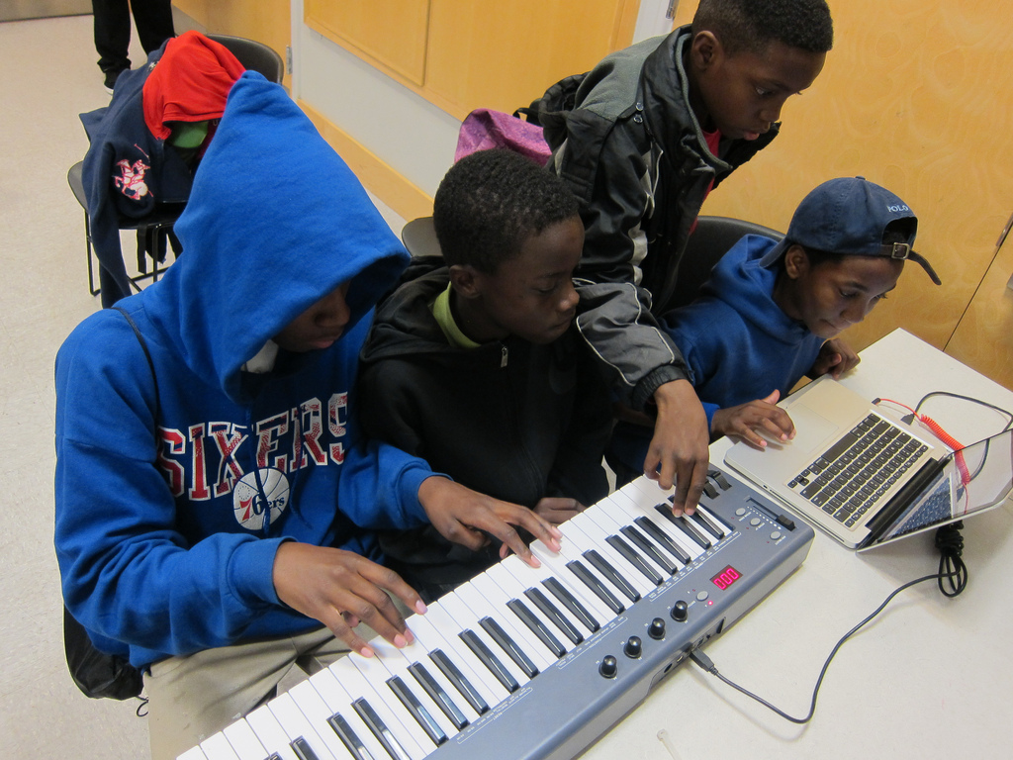
Documentation/indd/Links/11001480965_706395af89_b.jpg
