makerjawn/oneKey/Documentation/indd/Links/11001573946_44c7a34de6_o.png

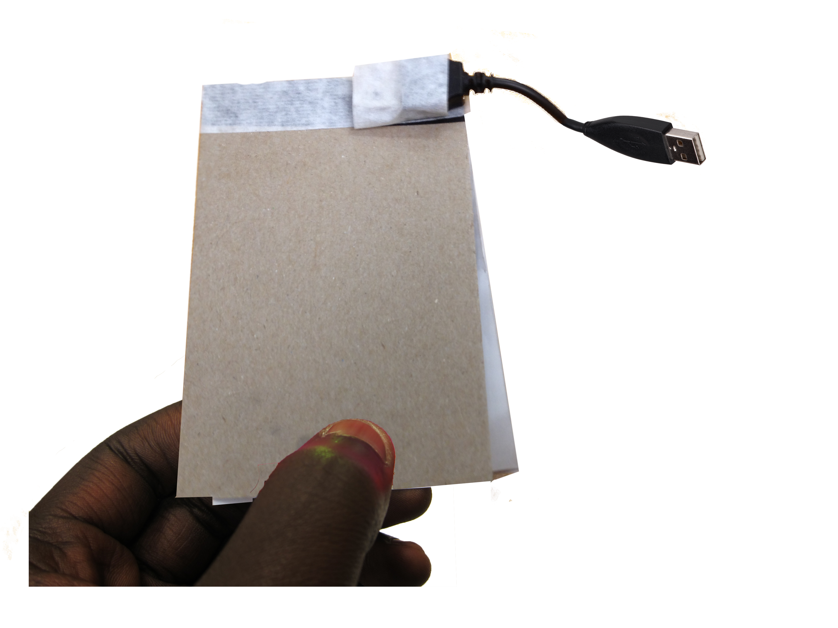
Documentation/indd/Links/11001573946_44c7a34de6_o.png
