makerjawn/oneKey/Documentation/indd/Links/11058265506_ddac9ea683_b.jpg

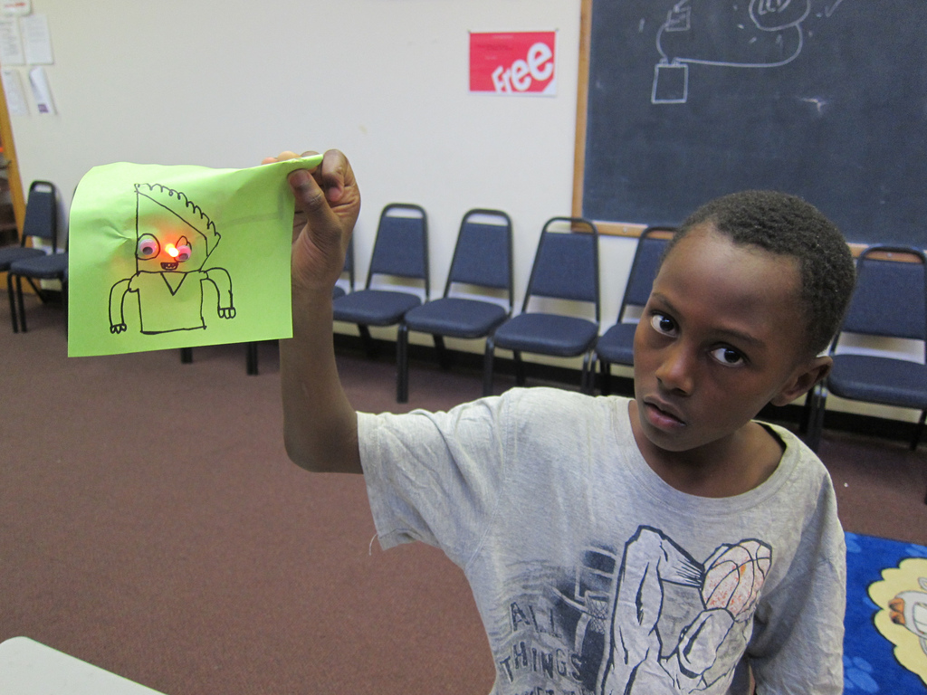
Documentation/indd/Links/11058265506_ddac9ea683_b.jpg
