makerjawn/oneKey/Documentation/indd/Links/11058268006_4afb9b592c_b (1).jpg

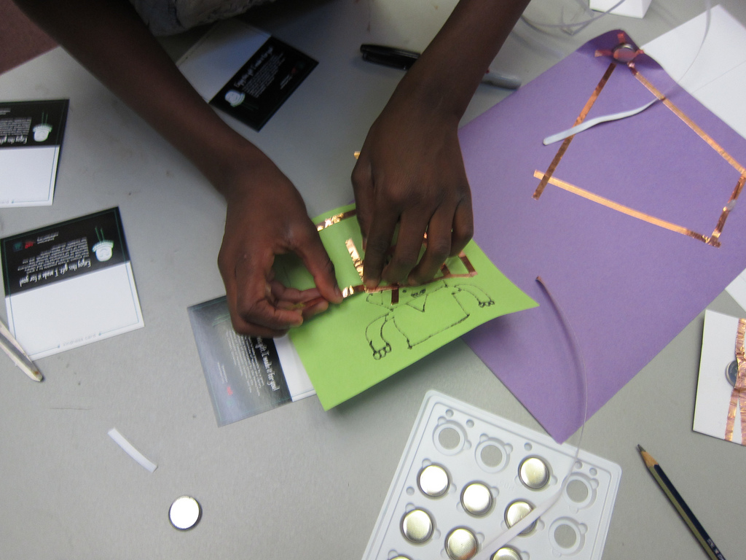
Documentation/indd/Links/11058268006_4afb9b592c_b (1).jpg
