makerjawn/oneKey/Documentation/indd/Links/11521306576_93ae1bd4c0_o.jpg

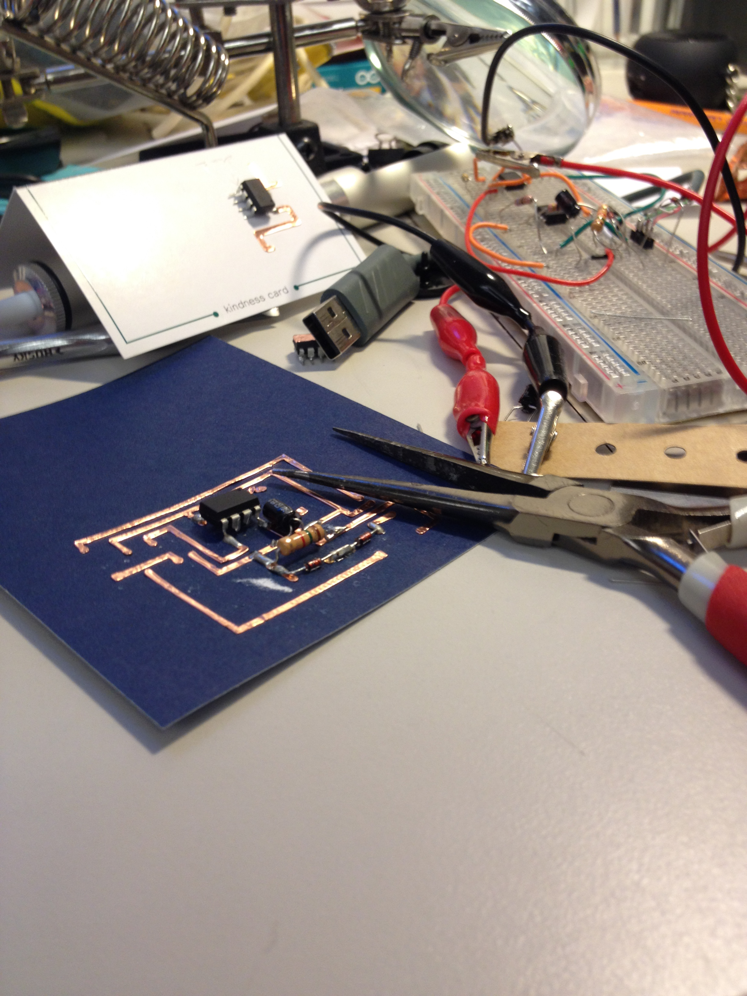
Documentation/indd/Links/11521306576_93ae1bd4c0_o.jpg
