makerjawn/oneKey/Documentation/indd/Links/11521315033_ebd864fc28_o.jpg

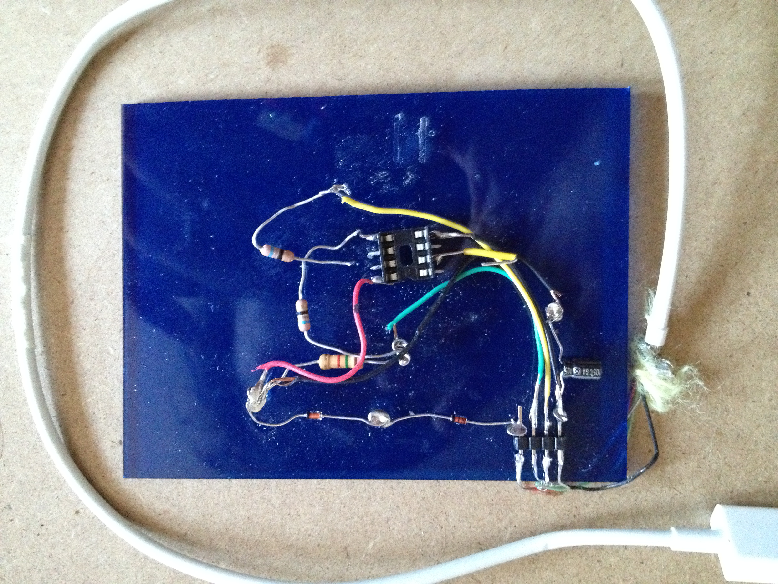
Documentation/indd/Links/11521315033_ebd864fc28_o.jpg
