makerjawn/oneKey/Documentation/indd/Links/11521358063_78504d4918_o.jpg

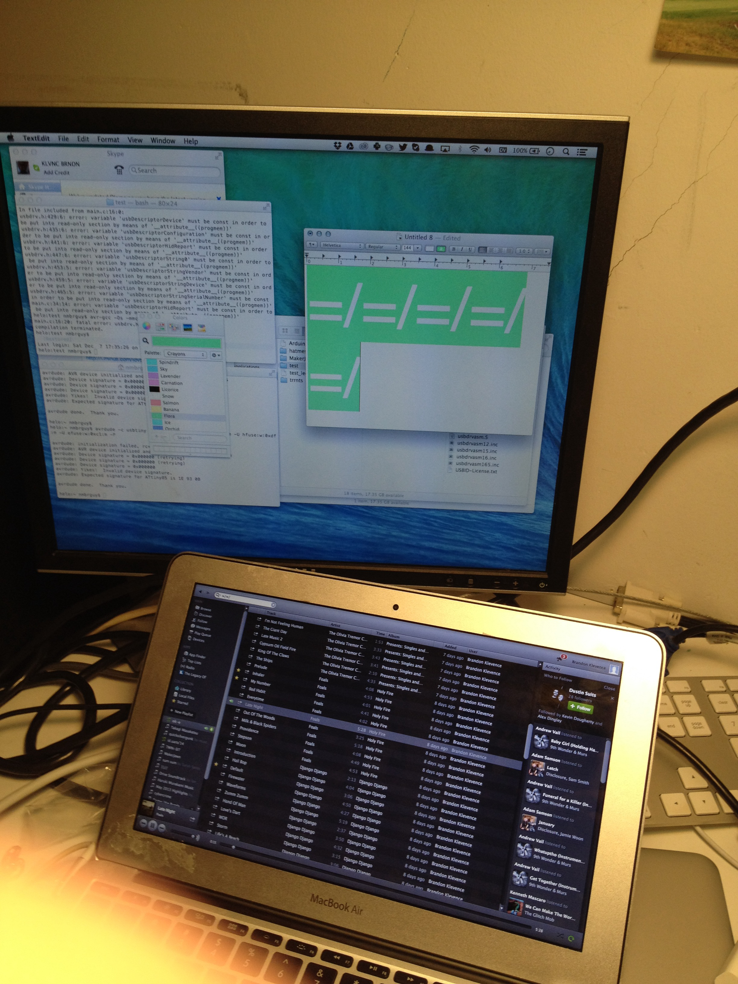
Documentation/indd/Links/11521358063_78504d4918_o.jpg
