makerjawn/oneKey/Documentation/indd/Links/12419454933_7949e35125_o.jpg

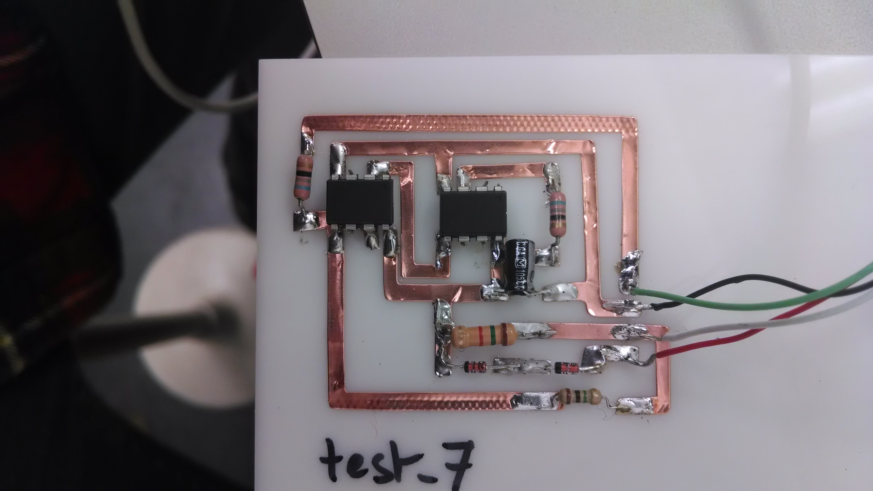
Documentation/indd/Links/12419454933_7949e35125_o.jpg
