makerjawn/oneKey/Documentation/indd/Links/12419766244_3c685013d1_o.jpg

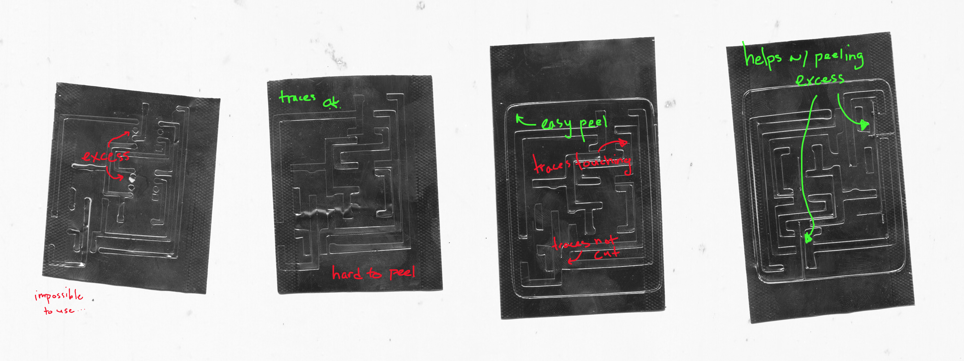
Documentation/indd/Links/12419766244_3c685013d1_o.jpg
