makerjawn/oneKey/Documentation/indd/Links/12525006553_50dffb66c0_o.jpg

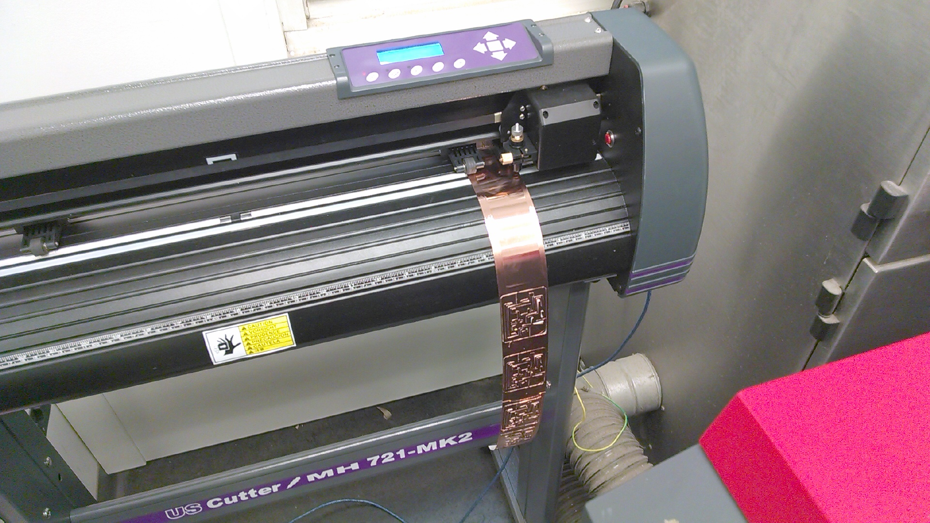
Documentation/indd/Links/12525006553_50dffb66c0_o.jpg
