makerjawn/oneKey/Documentation/indd/Links/12958650753_4f70de04ac_o.jpg

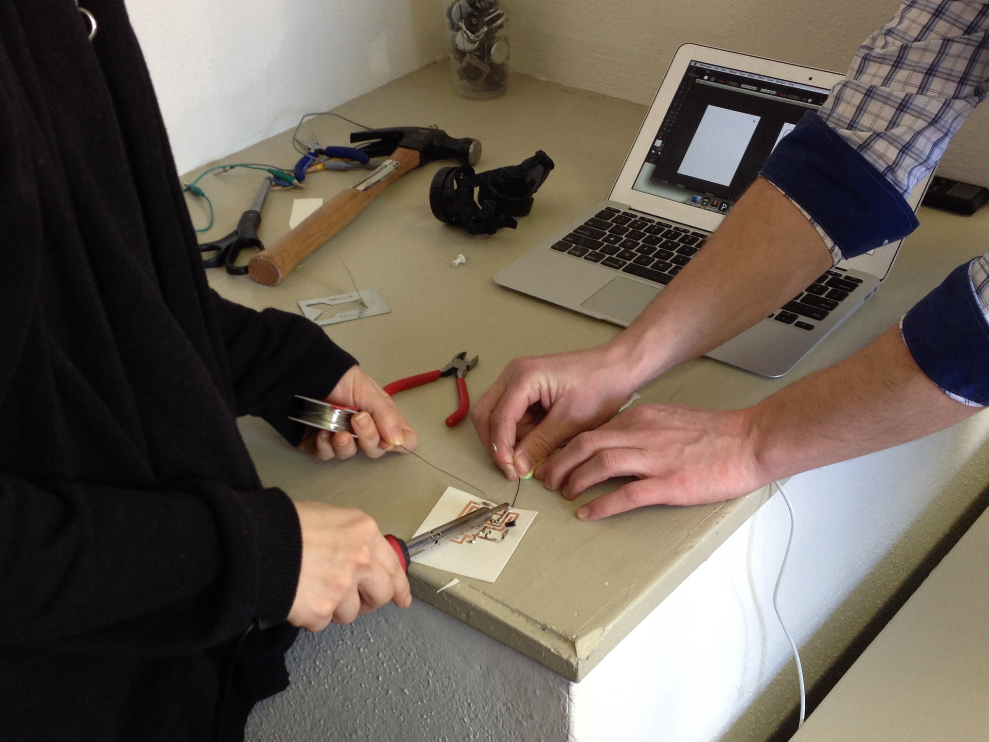
Documentation/indd/Links/12958650753_4f70de04ac_o.jpg
