makerjawn/oneKey/Documentation/indd/Links/12958877753_585e4944b3_b.jpg

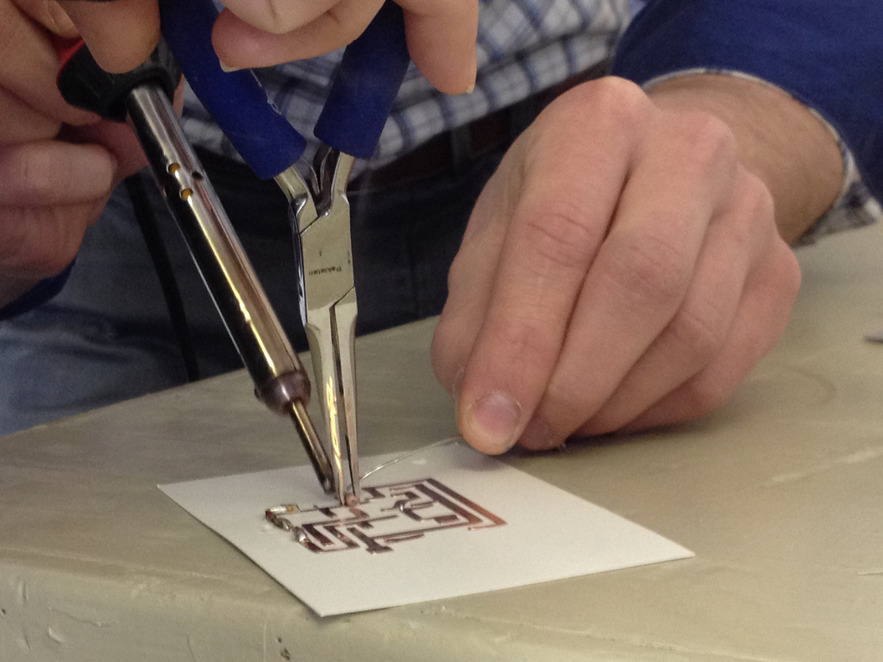
Documentation/indd/Links/12958877753_585e4944b3_b.jpg
