makerjawn/oneKey/Documentation/indd/Links/12958913943_8f999eb8ac_o (1).jpg

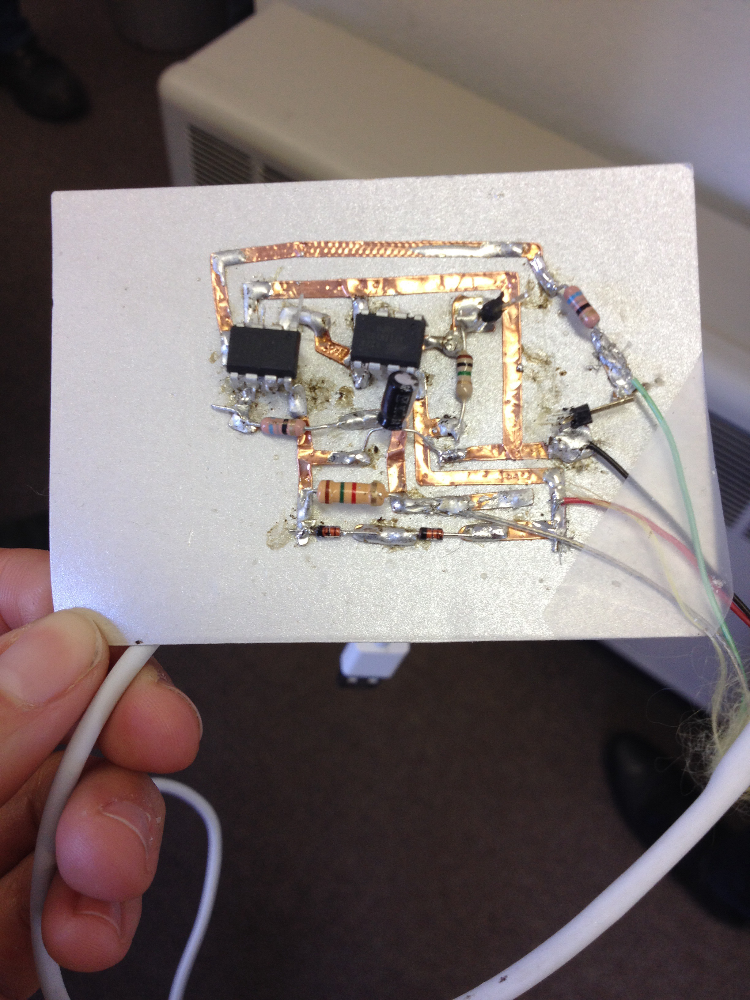
Documentation/indd/Links/12958913943_8f999eb8ac_o (1).jpg
