makerjawn/oneKey/Documentation/indd/Links/12959163355_4ab1fee12c_o.jpg

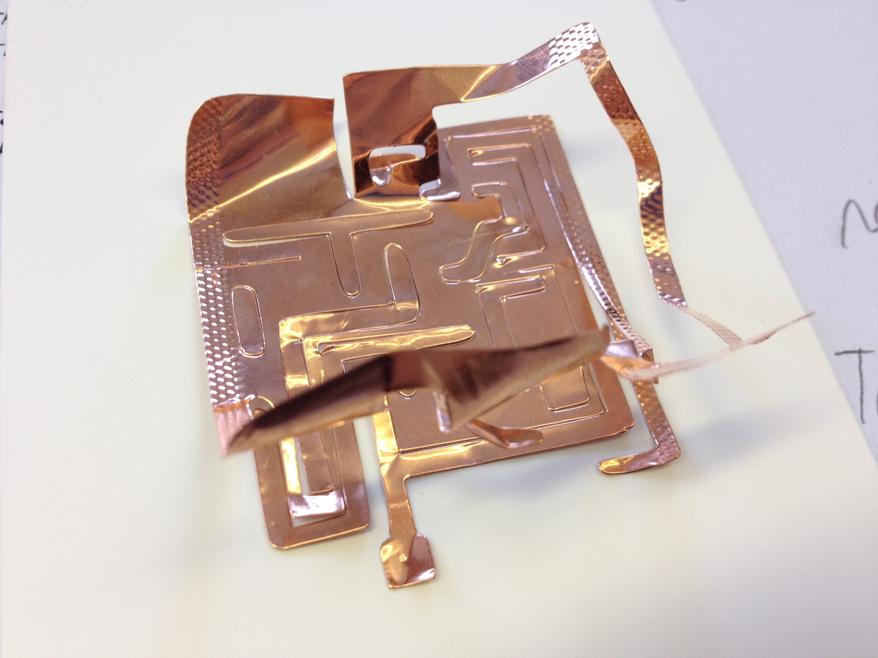
Documentation/indd/Links/12959163355_4ab1fee12c_o.jpg
