makerjawn/oneKey/Documentation/indd/Links/12959264913_cb7c0dd3db_b.jpg

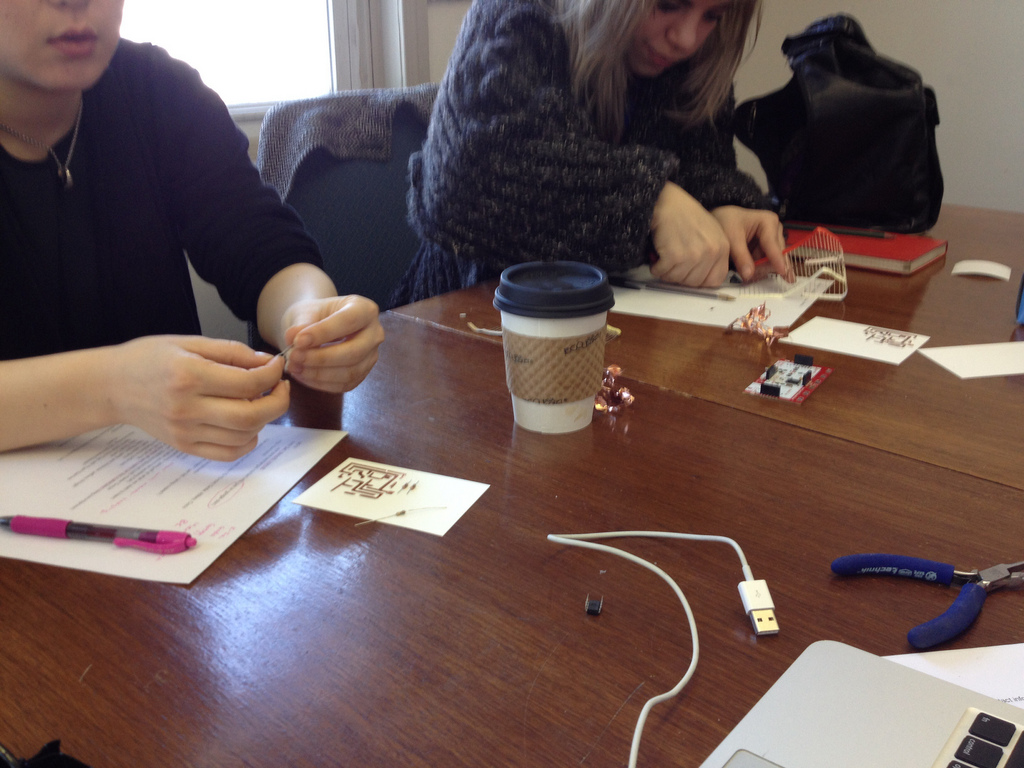
Documentation/indd/Links/12959264913_cb7c0dd3db_b.jpg
