makerjawn/oneKey/Documentation/indd/Links/13203166373_9ffb230416_o.jpg

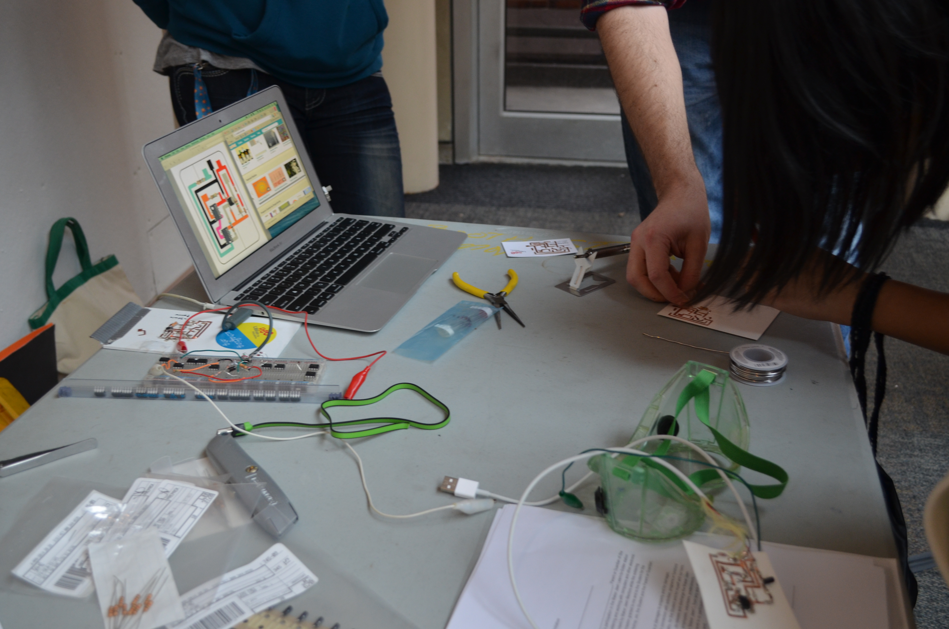
Documentation/indd/Links/13203166373_9ffb230416_o.jpg
