makerjawn/oneKey/Documentation/indd/Links/13203352664_32f6f5f795_o.jpg

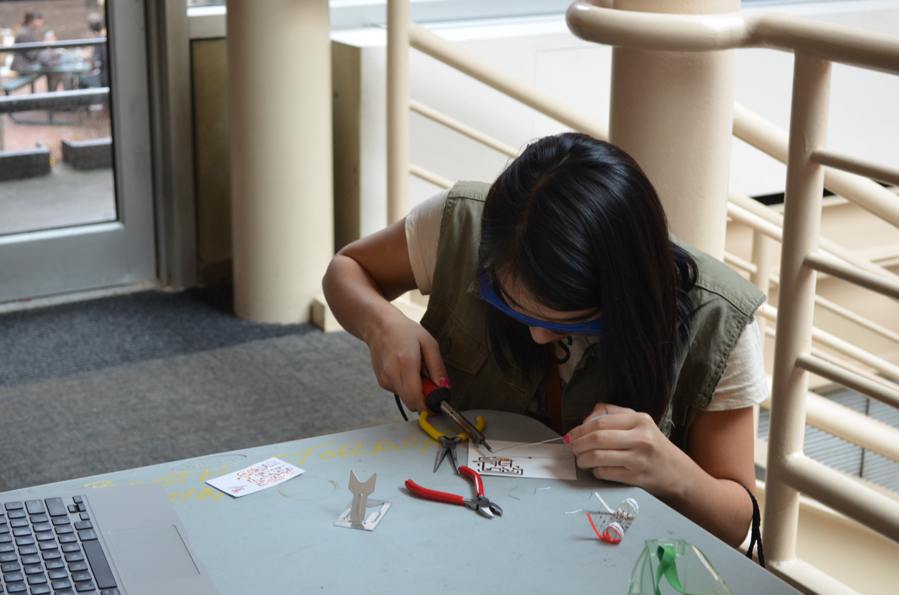
Documentation/indd/Links/13203352664_32f6f5f795_o.jpg
