makerjawn/oneKey/Documentation/indd/Links/13203372964_e8b3647032_o.jpg

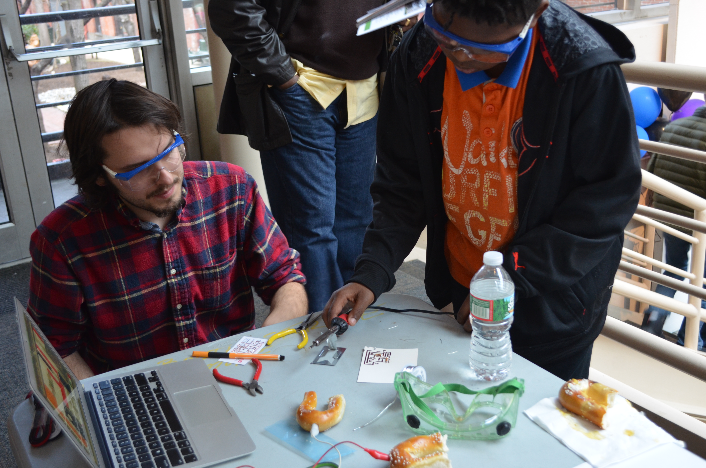
Documentation/indd/Links/13203372964_e8b3647032_o.jpg
