makerjawn/oneKey/Documentation/indd/Links/cm1.jpg

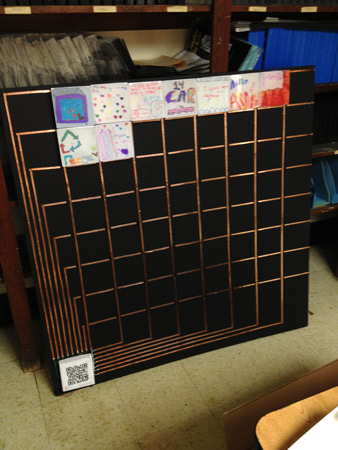
Documentation/indd/Links/cm1.jpg
