makerjawn/oneKey/Documentation/indd/Links/cm6.jpg

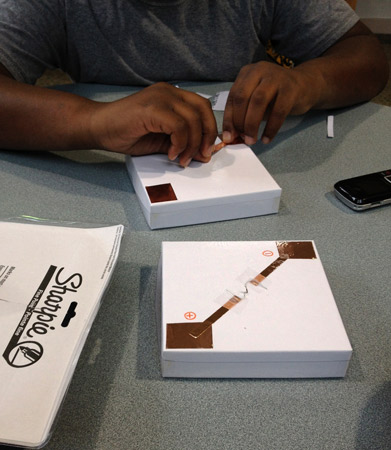
Documentation/indd/Links/cm6.jpg
