makerjawn/oneKey/Documentation/indd/Links/dml5-2.png

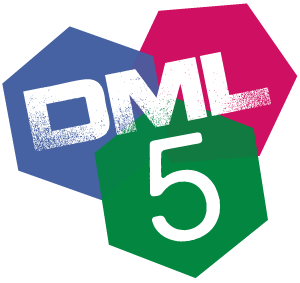
Documentation/indd/Links/dml5-2.png
