makerjawn/oneKey/Documentation/indd/Links/DSC_0016_1.jpg

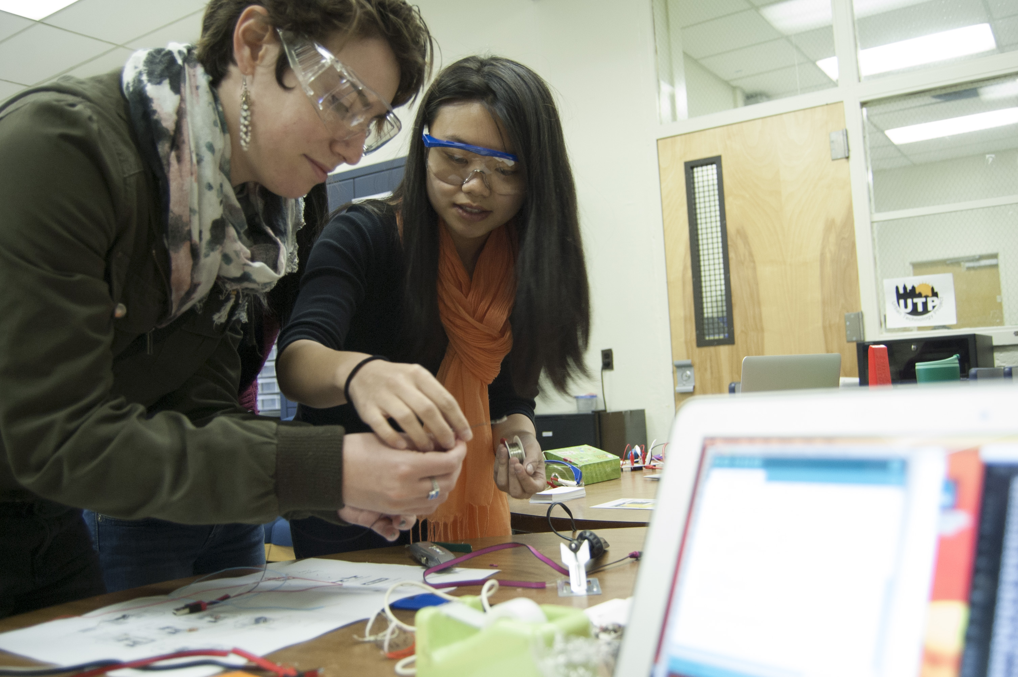
Documentation/indd/Links/DSC_0016_1.jpg
