makerjawn/oneKey/Documentation/indd/Links/DSC_0023.jpg

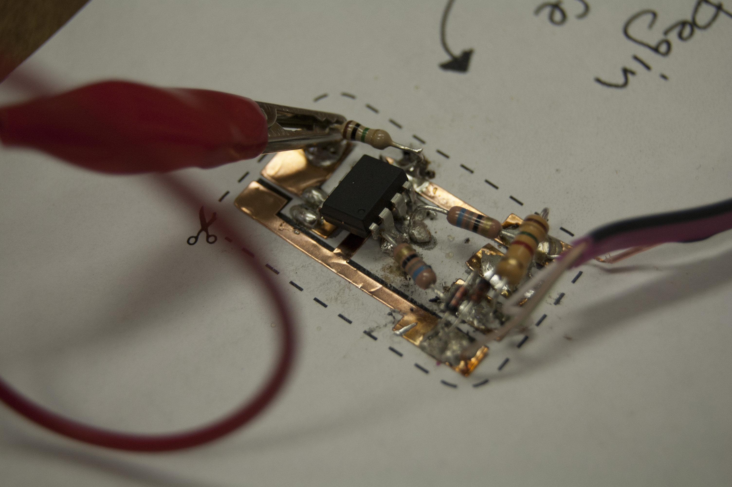
Documentation/indd/Links/DSC_0023.jpg
