makerjawn/oneKey/Documentation/indd/Links/DSC_0028.jpg

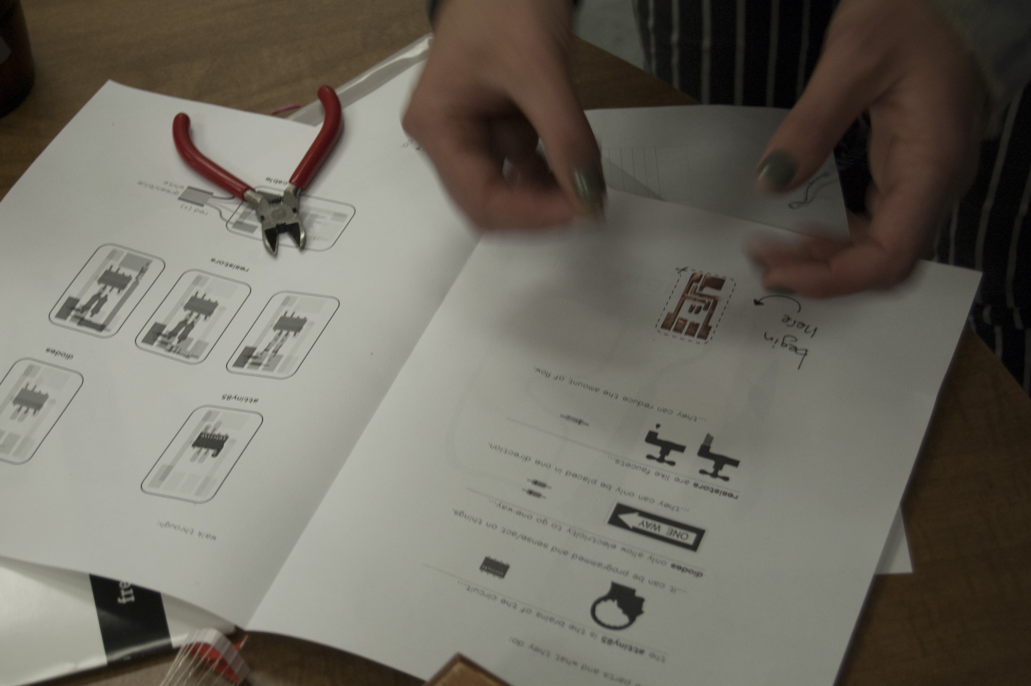
Documentation/indd/Links/DSC_0028.jpg
