makerjawn/oneKey/Documentation/indd/Links/DSC_0765.JPG

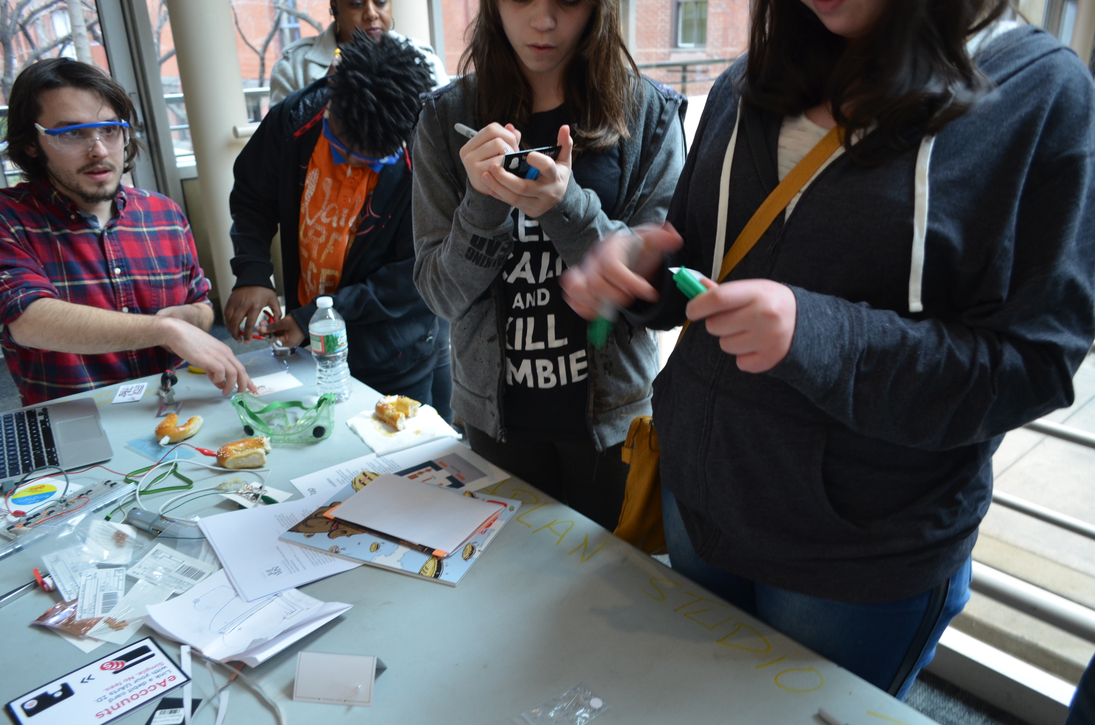
Documentation/indd/Links/DSC_0765.JPG
