makerjawn/oneKey/Documentation/indd/Links/fullscreen.png

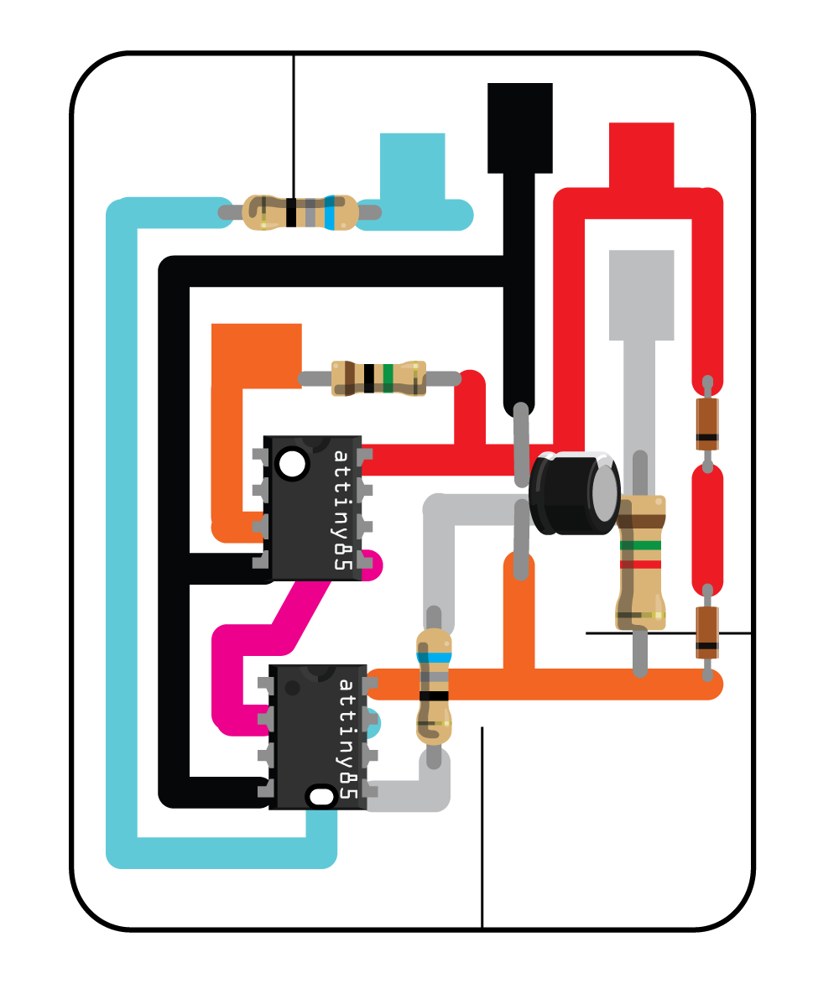
Documentation/indd/Links/fullscreen.png
