makerjawn/oneKey/Documentation/indd/Links/images.jpeg

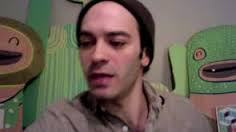
Documentation/indd/Links/images.jpeg
