makerjawn/oneKey/Documentation/indd/Links/IMG_0003.jpg

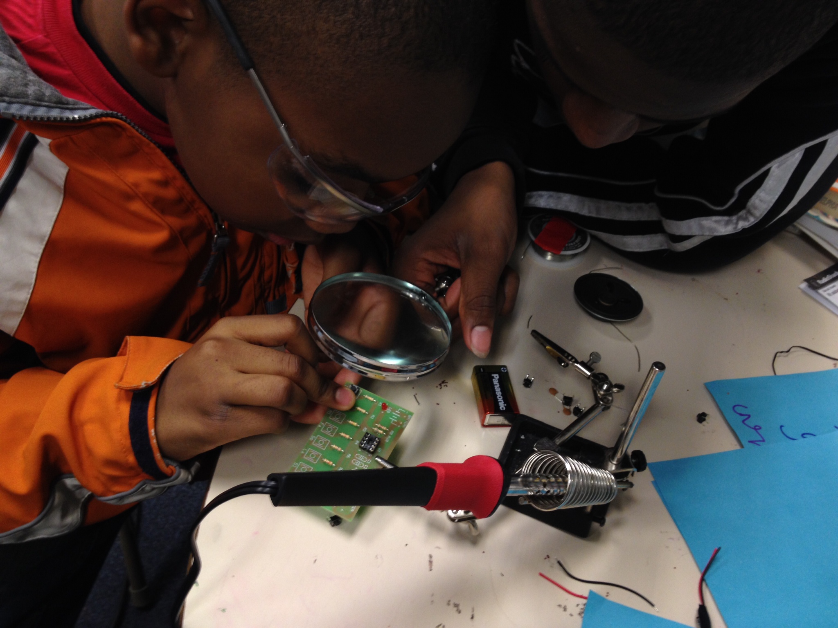
Documentation/indd/Links/IMG_0003.jpg
