makerjawn/oneKey/Documentation/indd/Links/IMG_0021.jpg

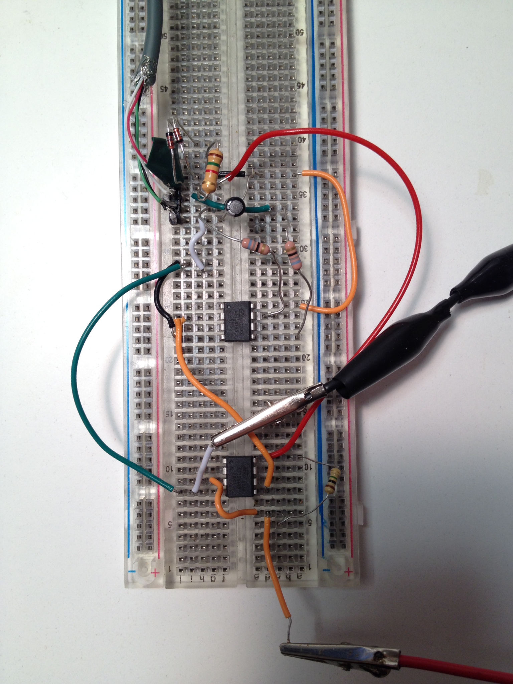
Documentation/indd/Links/IMG_0021.jpg
