makerjawn/oneKey/Documentation/indd/Links/IMG_0022.jpg

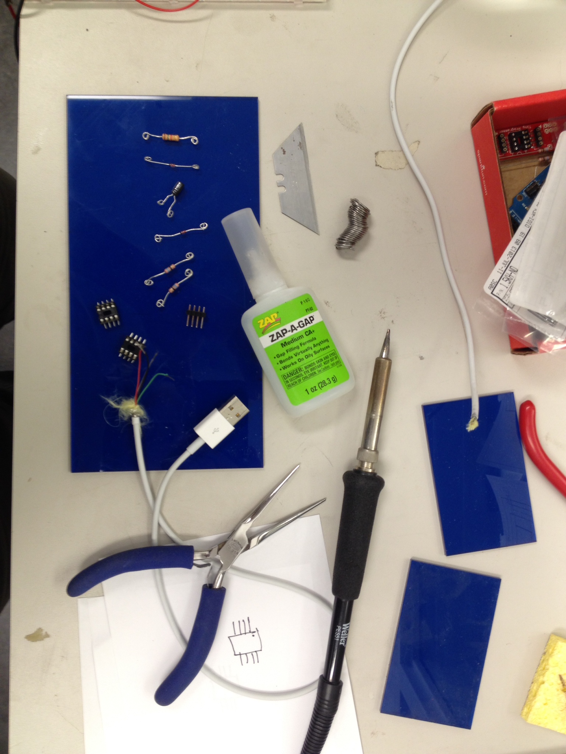
Documentation/indd/Links/IMG_0022.jpg
