makerjawn/oneKey/Documentation/indd/Links/IMG_0242.jpeg

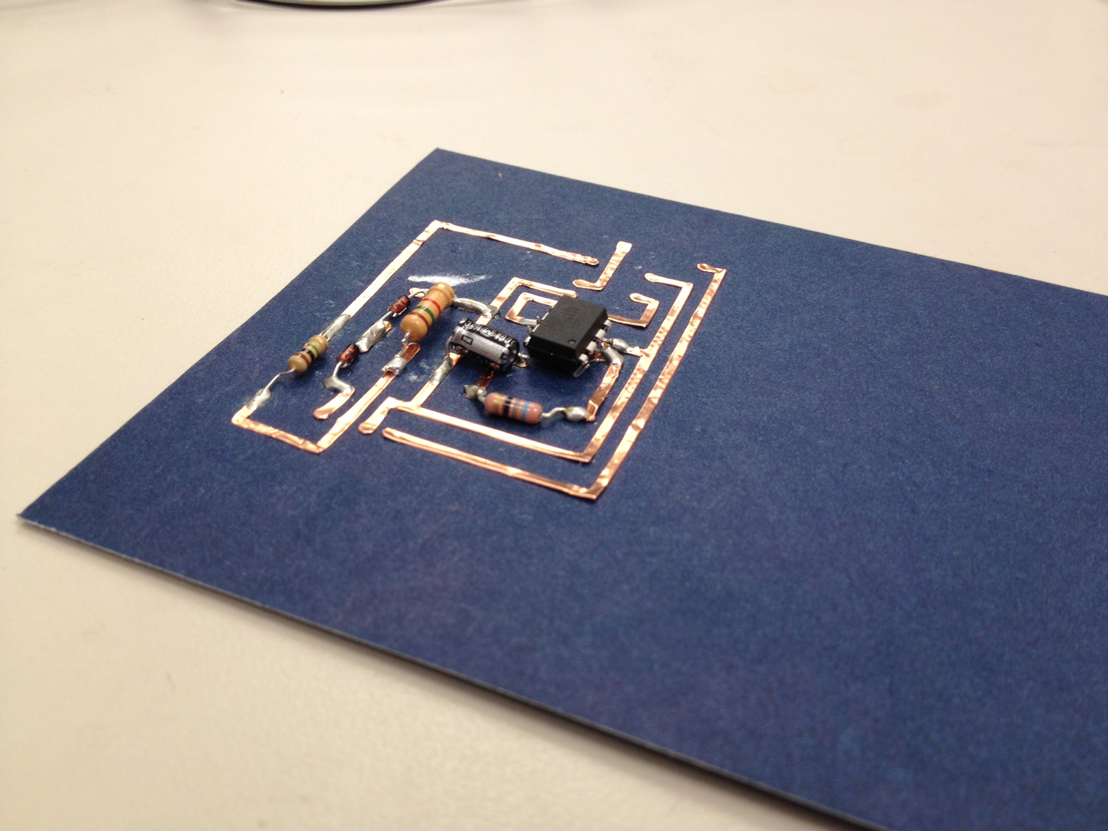
Documentation/indd/Links/IMG_0242.jpeg
