makerjawn/oneKey/Documentation/indd/Links/IMG_0763.jpg

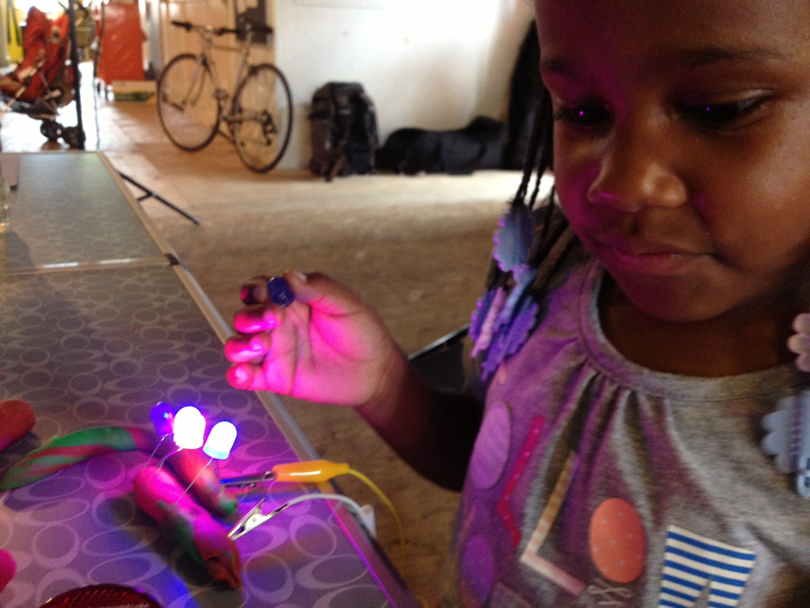
Documentation/indd/Links/IMG_0763.jpg
