makerjawn/oneKey/Documentation/indd/Links/IMG_0765.jpg

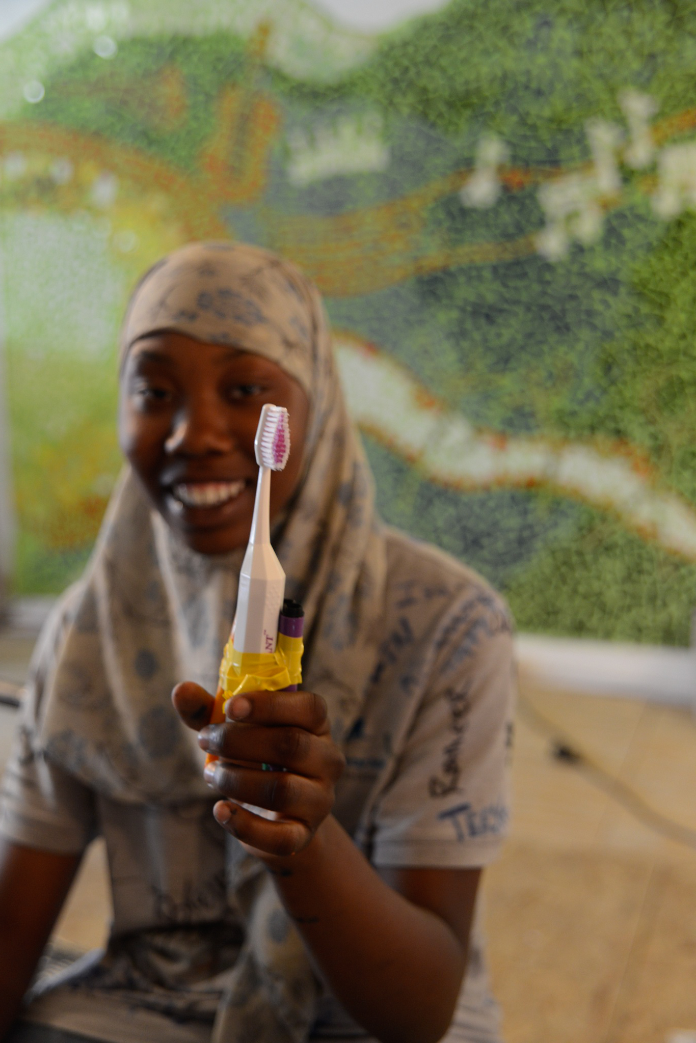
Documentation/indd/Links/IMG_0765.jpg
