makerjawn/oneKey/Documentation/indd/Links/IMG_0802.jpg

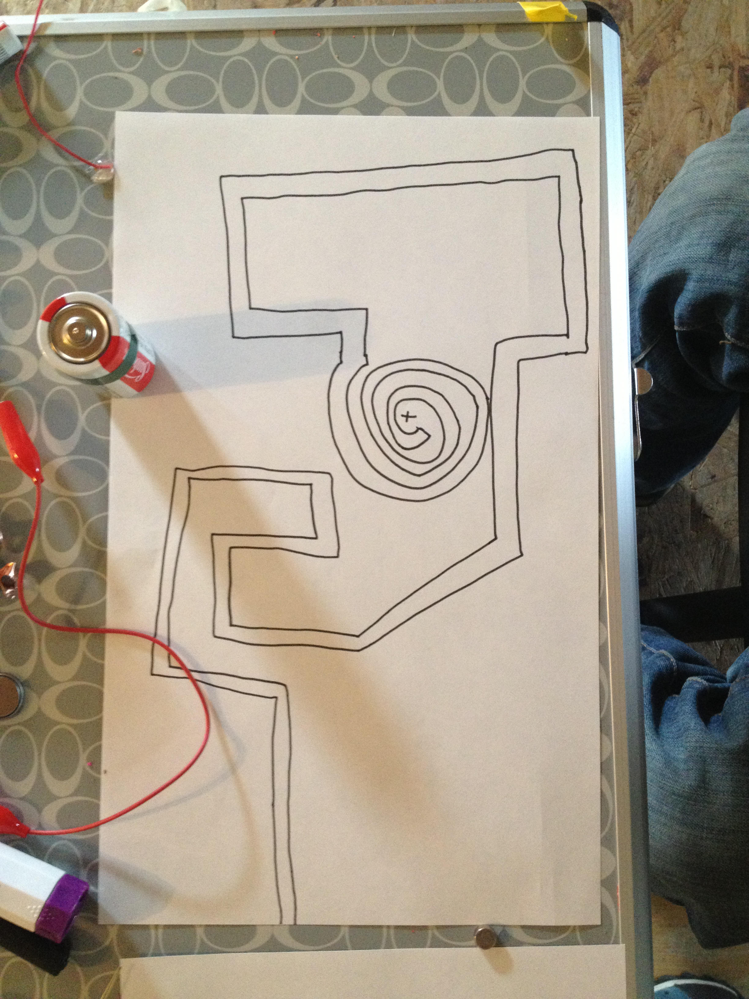
Documentation/indd/Links/IMG_0802.jpg
