makerjawn/oneKey/Documentation/indd/Links/IMG_0813.jpg

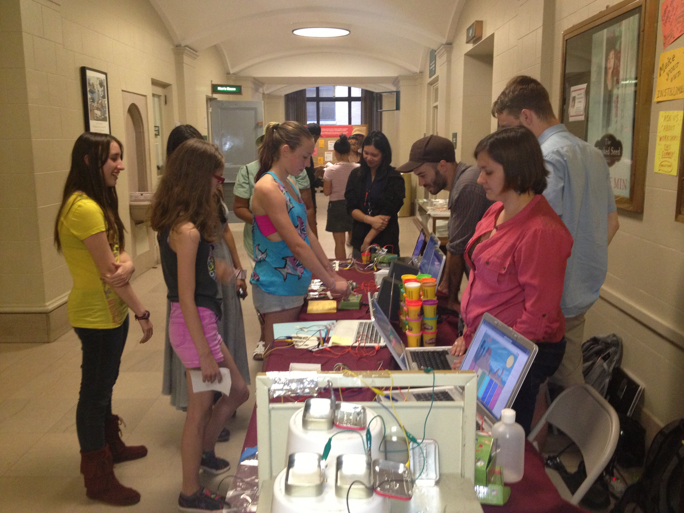
Documentation/indd/Links/IMG_0813.jpg
