makerjawn/oneKey/Documentation/indd/Links/IMG_0855.jpg

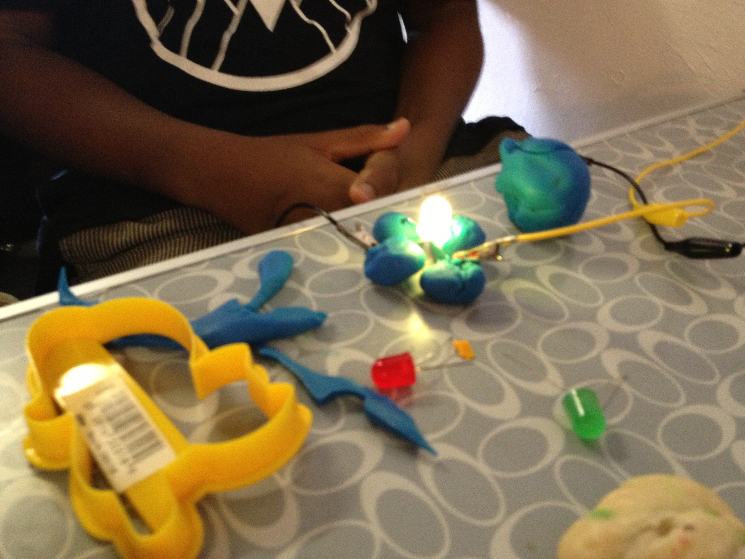
Documentation/indd/Links/IMG_0855.jpg
