makerjawn/oneKey/Documentation/indd/Links/IMG_0857.jpg

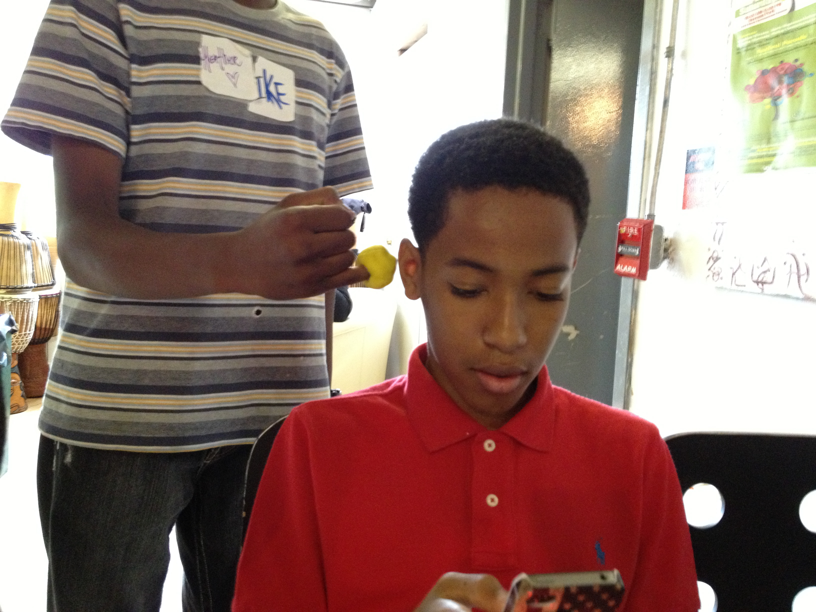
Documentation/indd/Links/IMG_0857.jpg
