makerjawn/oneKey/Documentation/indd/Links/IMG_0906.jpg

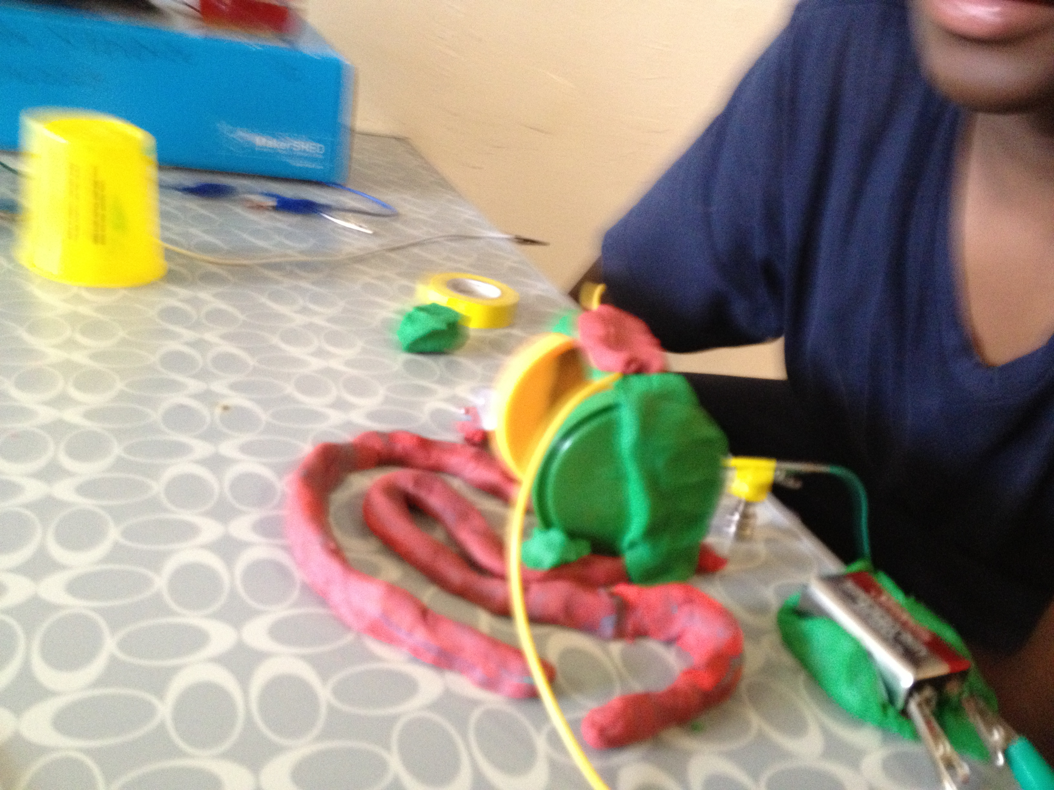
Documentation/indd/Links/IMG_0906.jpg
