makerjawn/oneKey/Documentation/indd/Links/IMG_0913.jpg

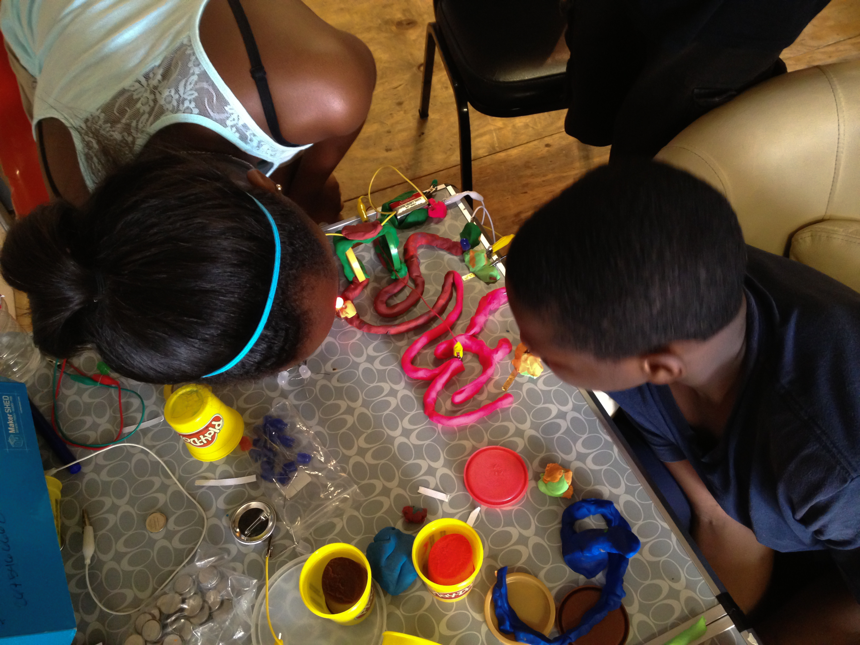
Documentation/indd/Links/IMG_0913.jpg
