makerjawn/oneKey/Documentation/indd/Links/IMG_0924.jpg

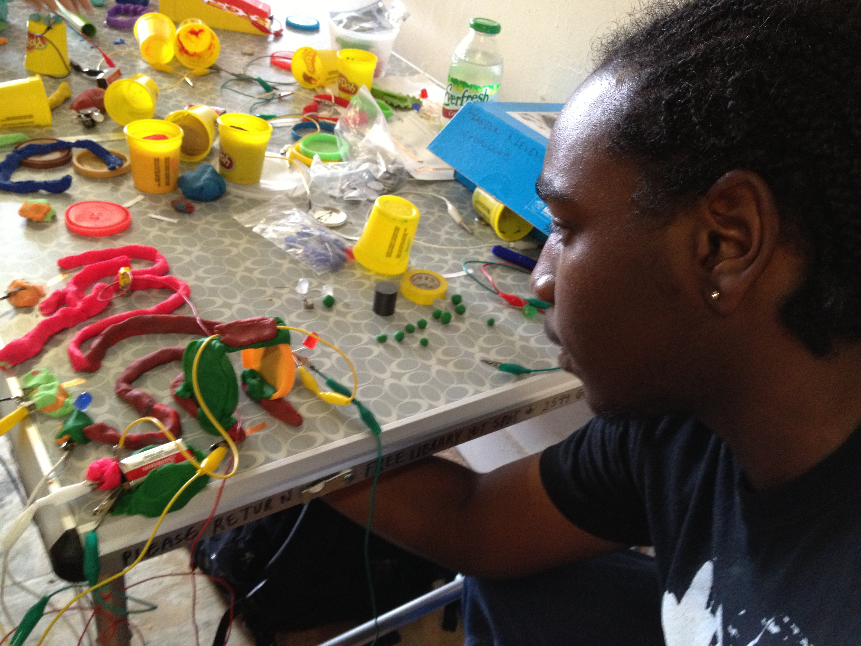
Documentation/indd/Links/IMG_0924.jpg
