makerjawn/oneKey/Documentation/indd/Links/IMG_0951.jpg

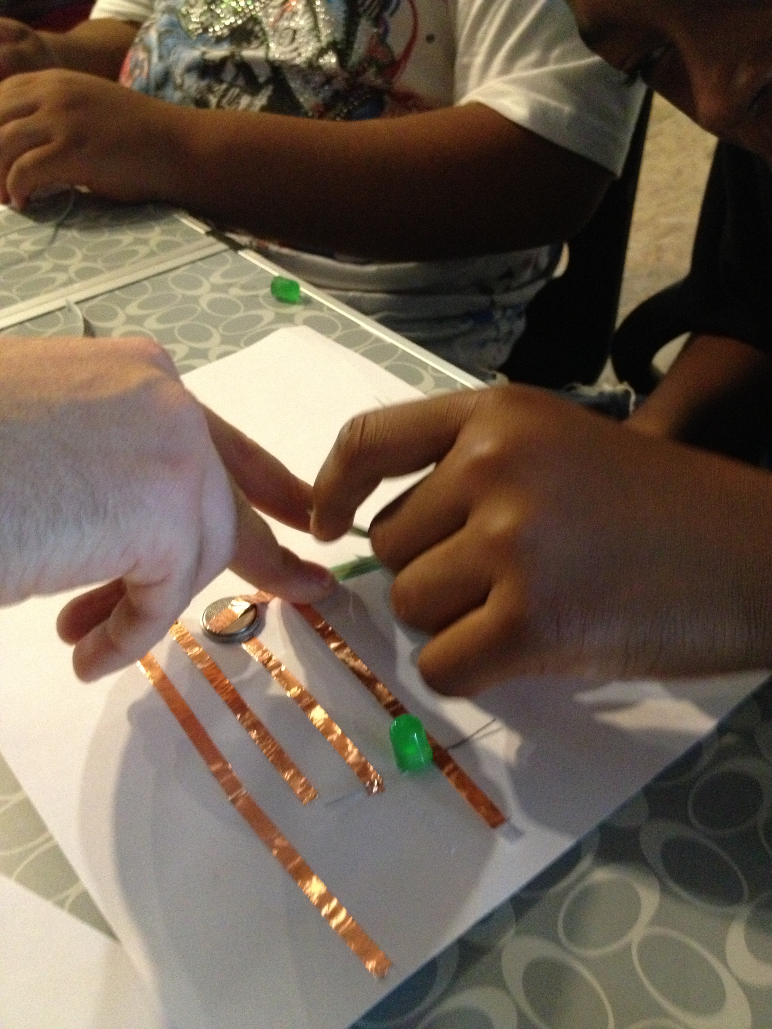
Documentation/indd/Links/IMG_0951.jpg
