makerjawn/oneKey/Documentation/indd/Links/IMG_0990-1024x768.jpg

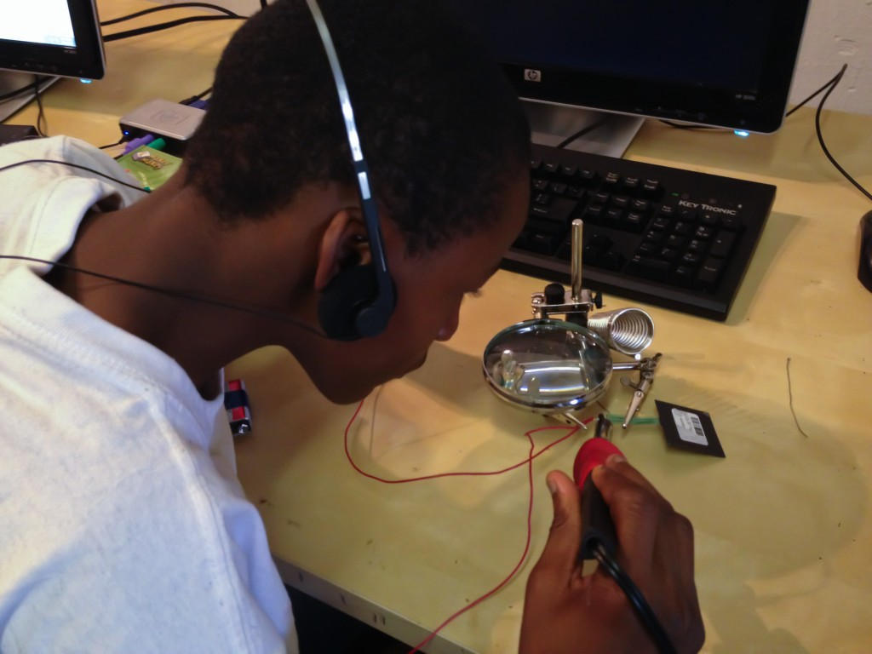
Documentation/indd/Links/IMG_0990-1024x768.jpg
