makerjawn/oneKey/Documentation/indd/Links/IMG_0991.jpg

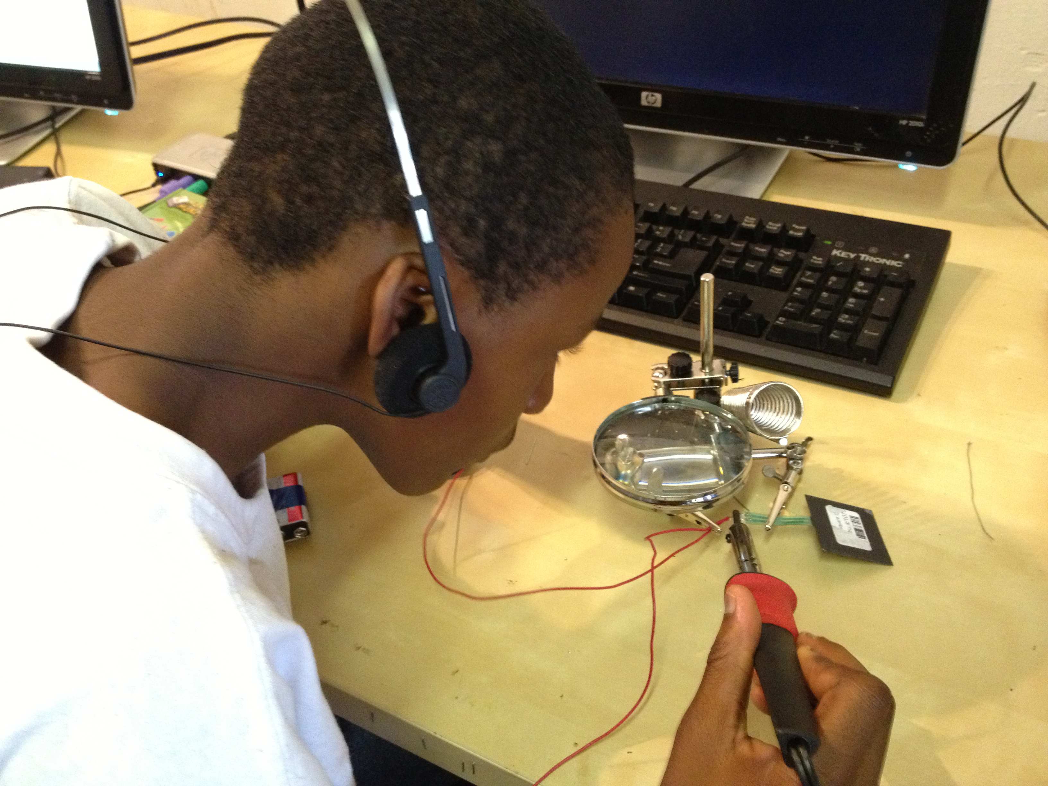
Documentation/indd/Links/IMG_0991.jpg
