makerjawn/oneKey/Documentation/indd/Links/IMG_1006-1024x768.jpg

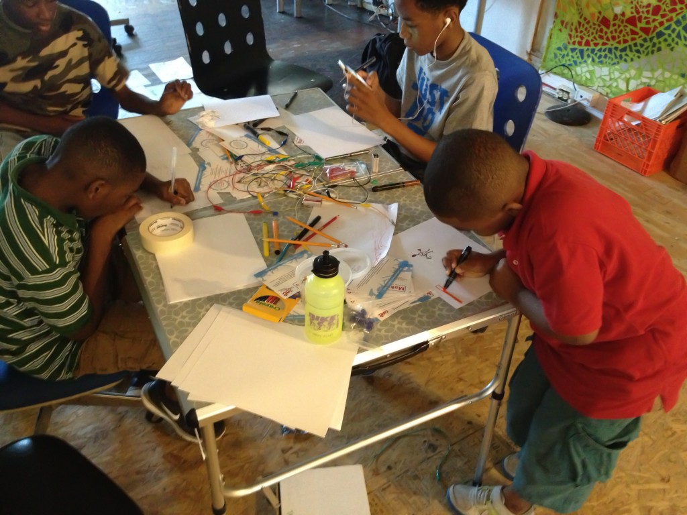
Documentation/indd/Links/IMG_1006-1024x768.jpg
