makerjawn/oneKey/Documentation/indd/Links/IMG_1019.jpg

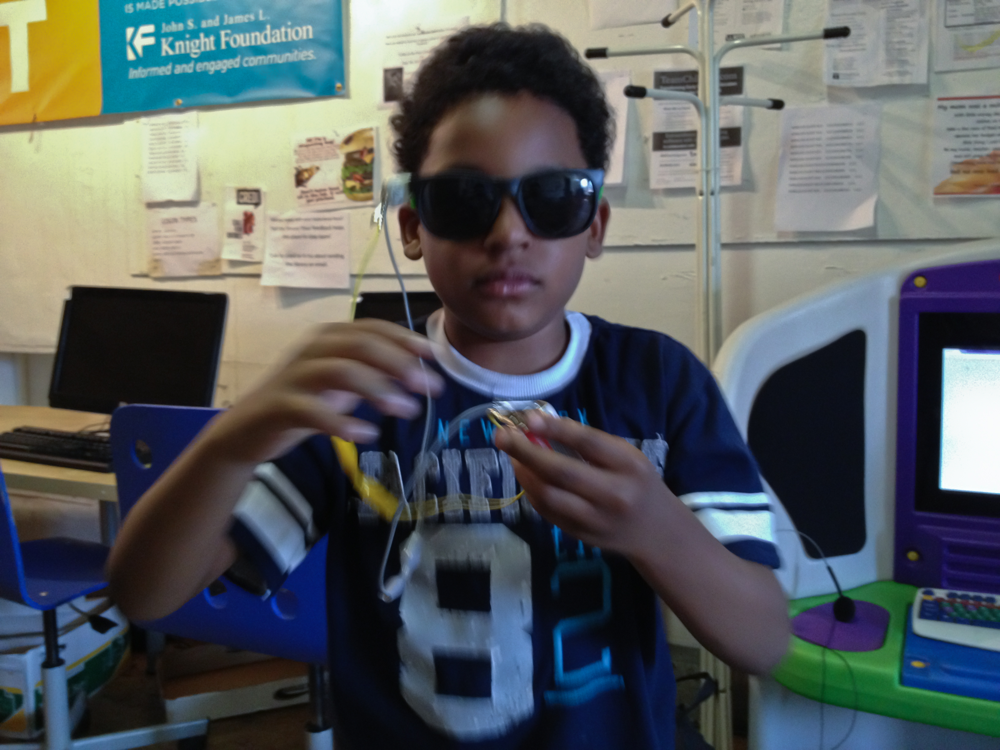
Documentation/indd/Links/IMG_1019.jpg
