makerjawn/oneKey/Documentation/indd/Links/IMG_1102.jpg

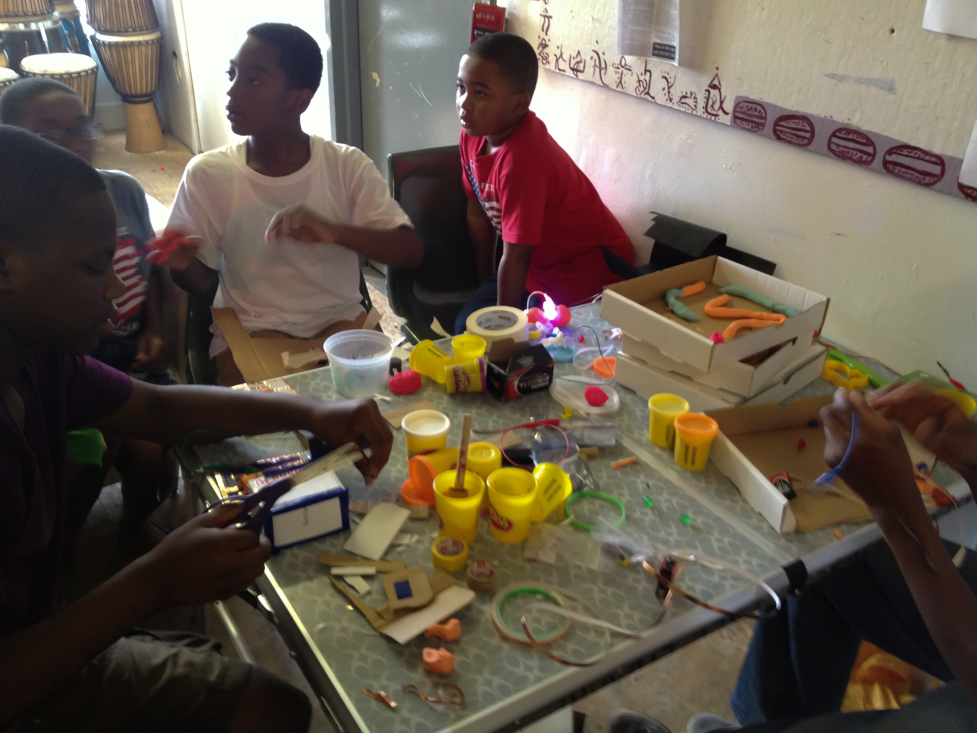
Documentation/indd/Links/IMG_1102.jpg
