makerjawn/oneKey/Documentation/indd/Links/IMG_1108.jpg

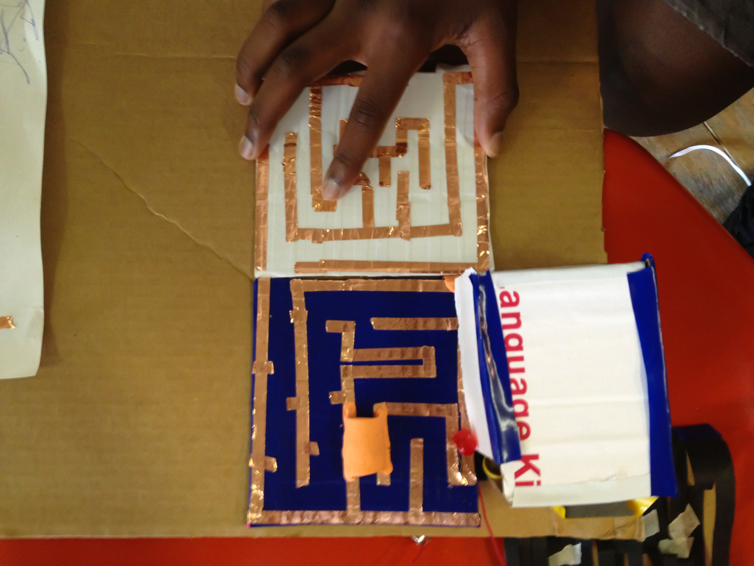
Documentation/indd/Links/IMG_1108.jpg
