makerjawn/oneKey/Documentation/indd/Links/IMG_1202.jpg

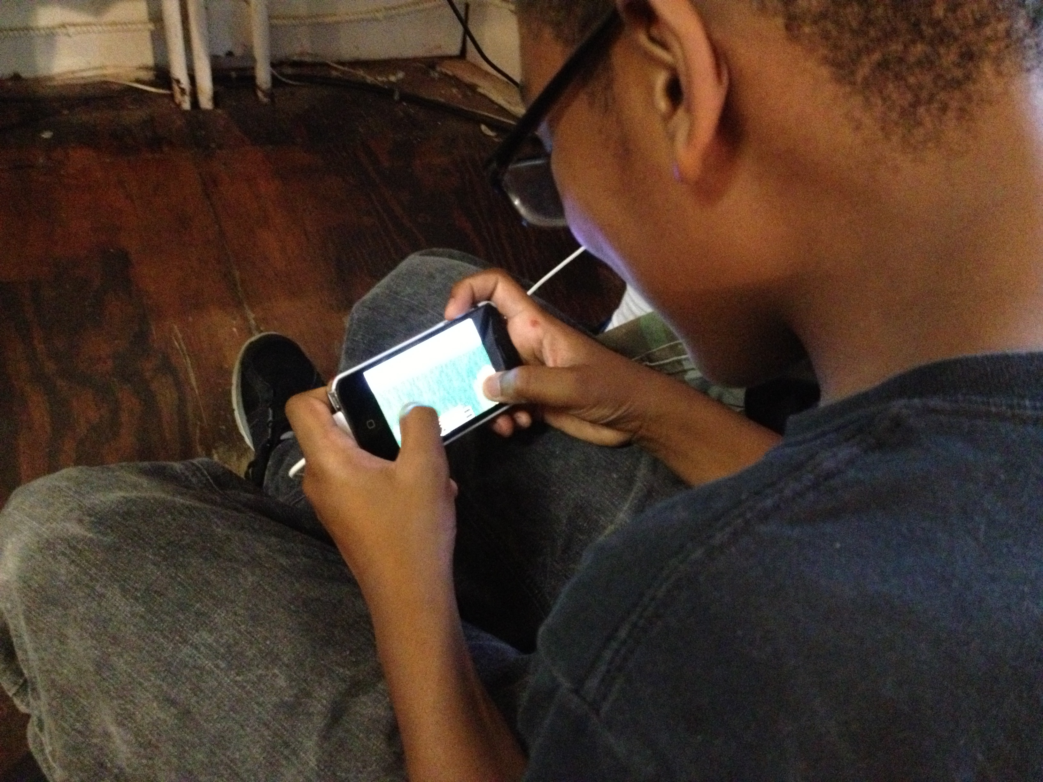
Documentation/indd/Links/IMG_1202.jpg
