makerjawn/oneKey/Documentation/indd/Links/IMG_1216.jpg

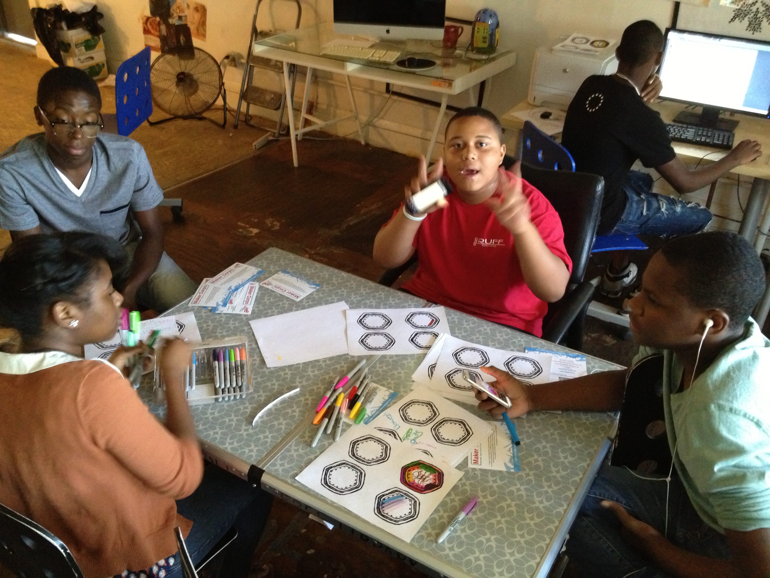
Documentation/indd/Links/IMG_1216.jpg
