makerjawn/oneKey/Documentation/indd/Links/IMG_1308 copy.jpg

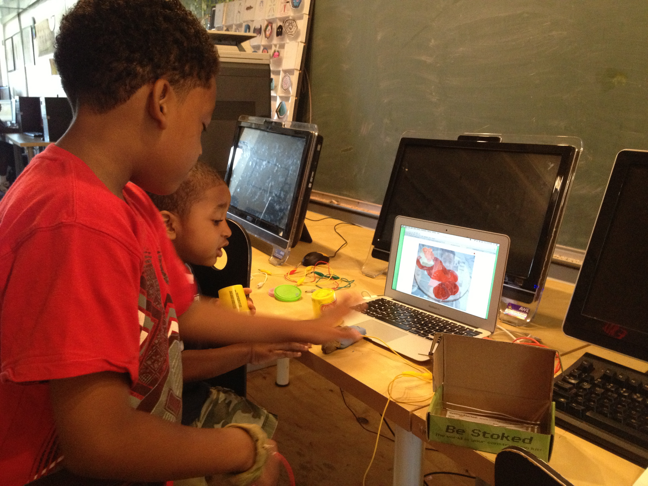
Documentation/indd/Links/IMG_1308 copy.jpg
