makerjawn/oneKey/Documentation/indd/Links/IMG_1310.jpg

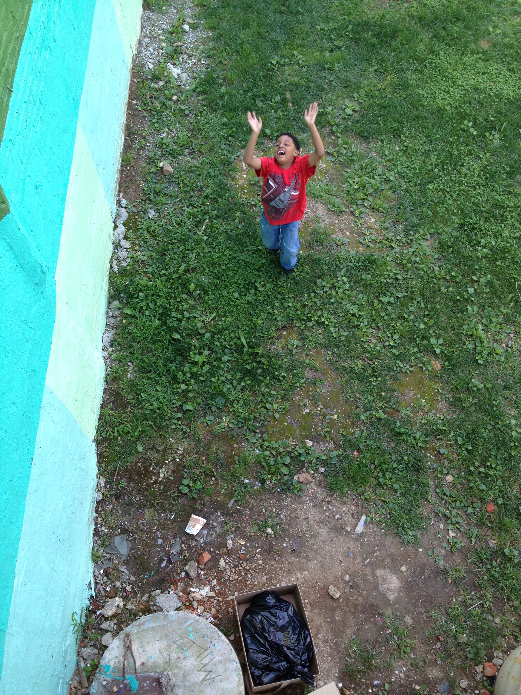
Documentation/indd/Links/IMG_1310.jpg
