makerjawn/oneKey/Documentation/indd/Links/IMG_1327 copy.jpg

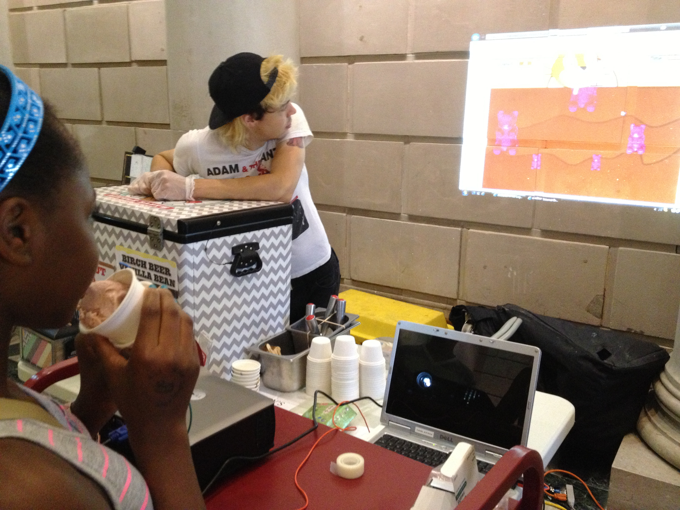
Documentation/indd/Links/IMG_1327 copy.jpg
