makerjawn/oneKey/Documentation/indd/Links/IMG_1584.JPG

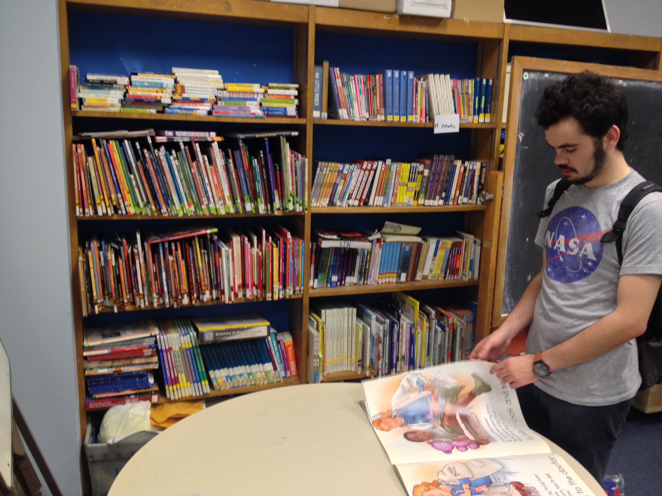
Documentation/indd/Links/IMG_1584.JPG
