makerjawn/oneKey/Documentation/indd/Links/IMG_1588.JPG

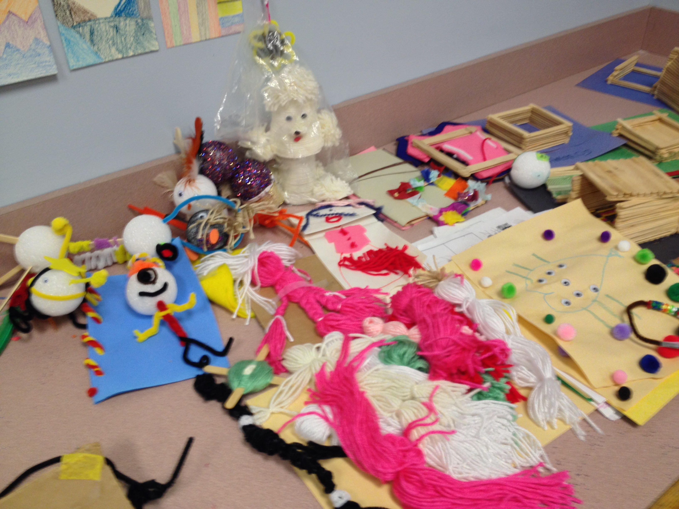
Documentation/indd/Links/IMG_1588.JPG
