makerjawn/oneKey/Documentation/indd/Links/IMG_1640.JPG

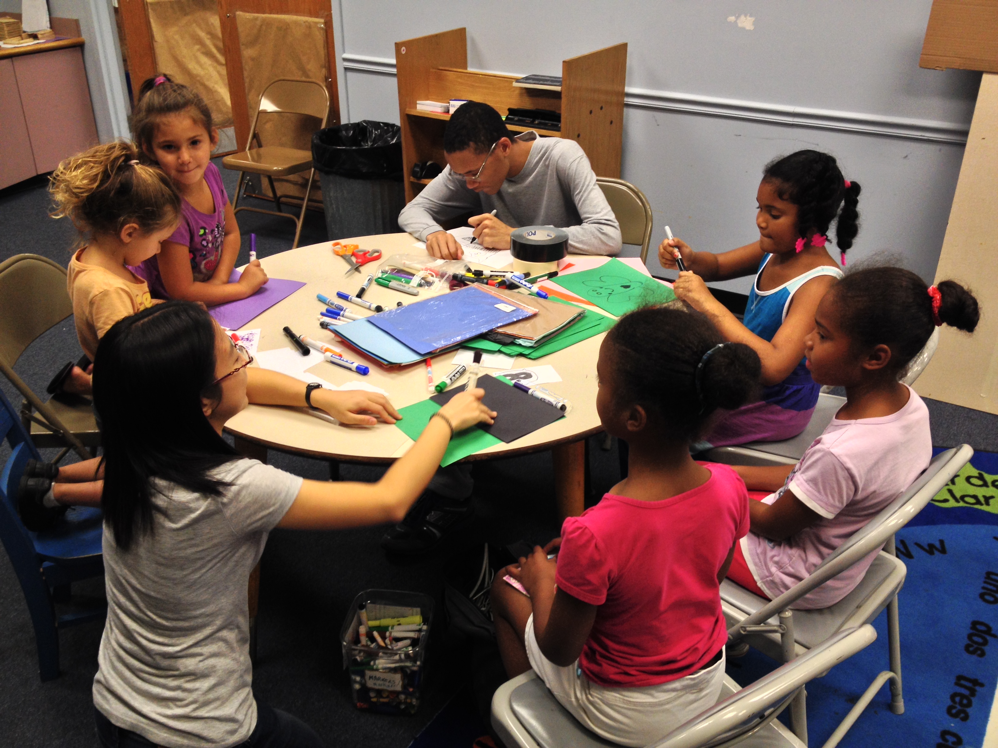
Documentation/indd/Links/IMG_1640.JPG
