makerjawn/oneKey/Documentation/indd/Links/IMG_1646.JPG

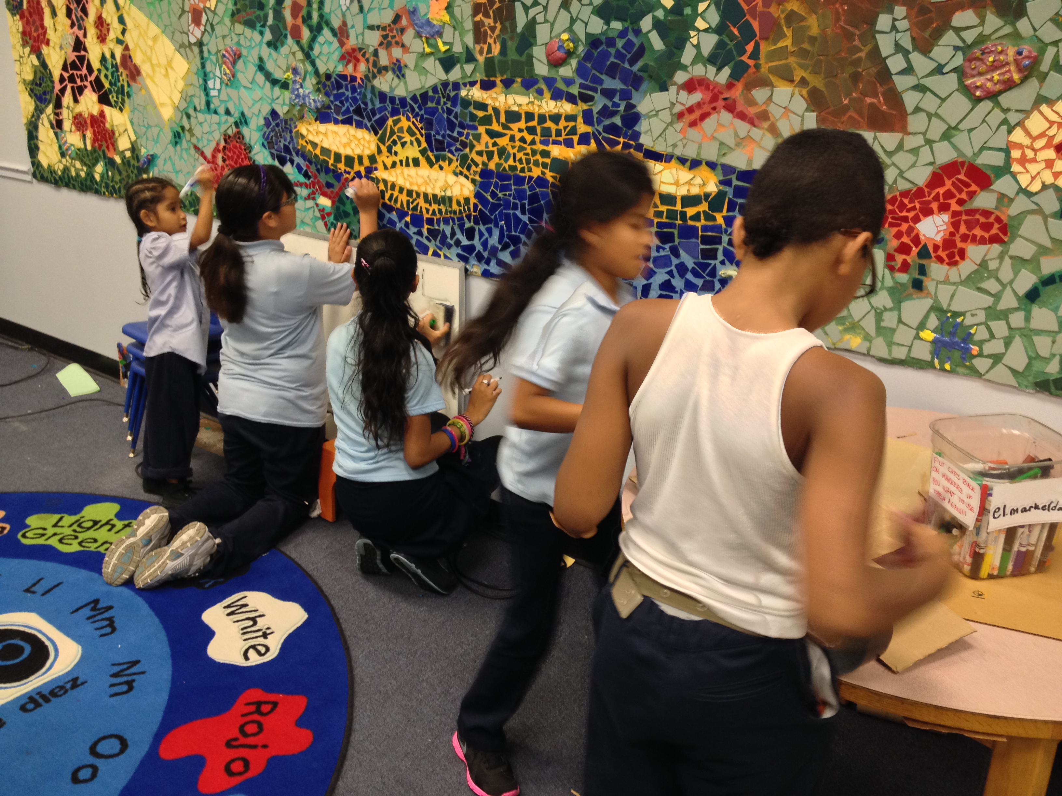
Documentation/indd/Links/IMG_1646.JPG
