makerjawn/oneKey/Documentation/indd/Links/IMG_1712.JPG

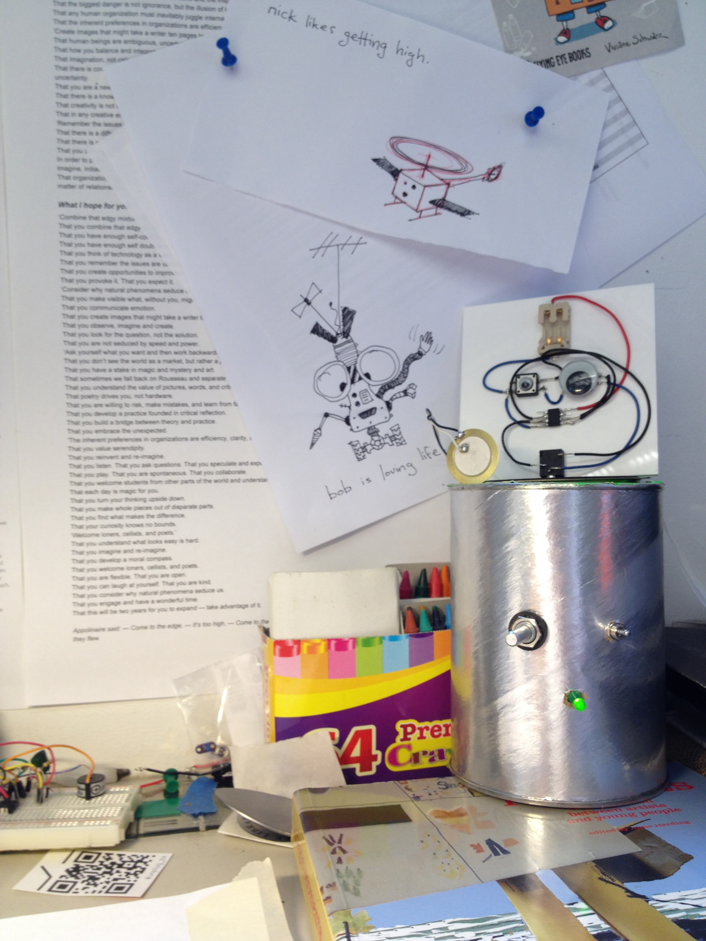
Documentation/indd/Links/IMG_1712.JPG
