makerjawn/oneKey/Documentation/indd/Links/IMG_1794.JPG

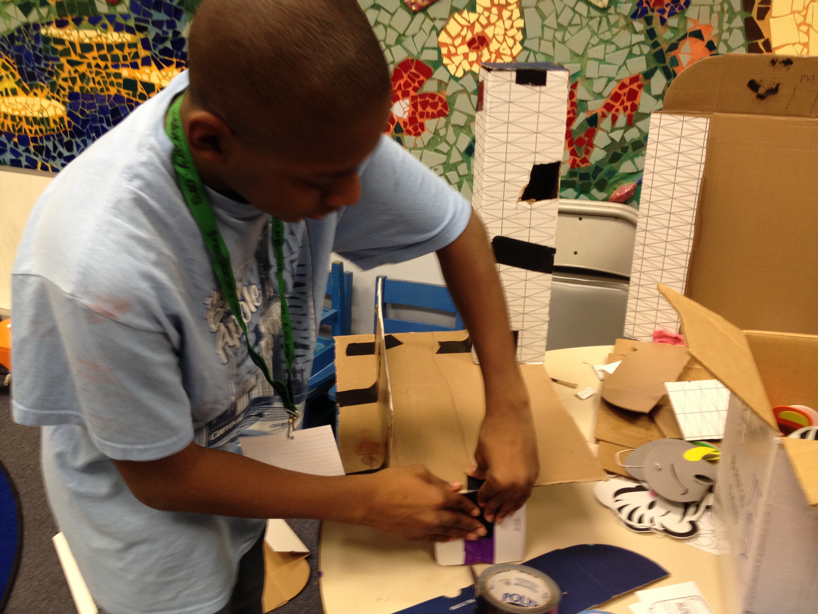
Documentation/indd/Links/IMG_1794.JPG
