makerjawn/oneKey/Documentation/indd/Links/IMG_2562.JPG

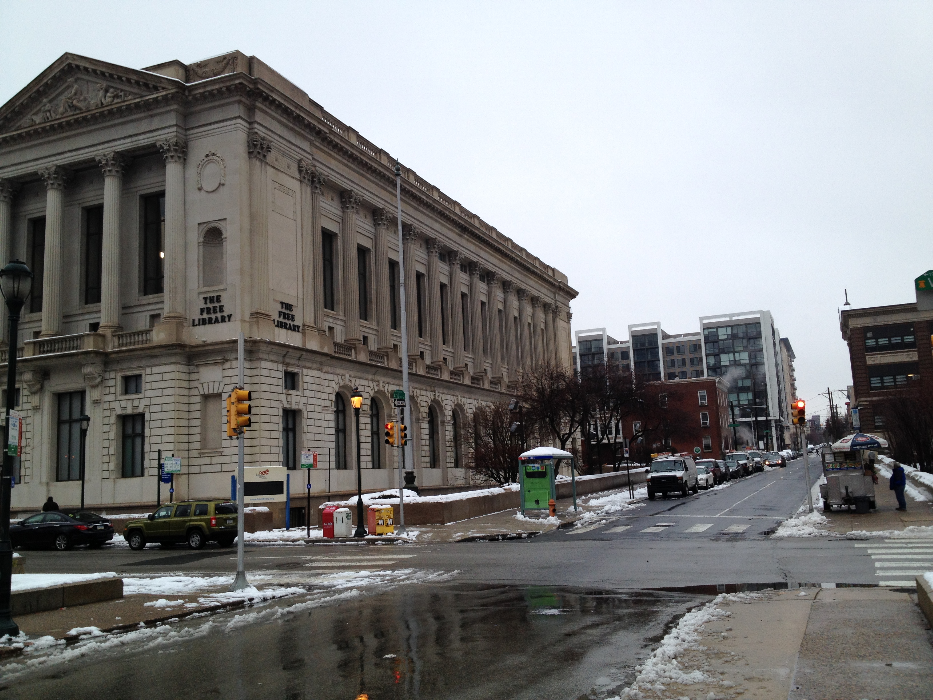
Documentation/indd/Links/IMG_2562.JPG
