makerjawn/oneKey/Documentation/indd/Links/IMG_2585.JPG

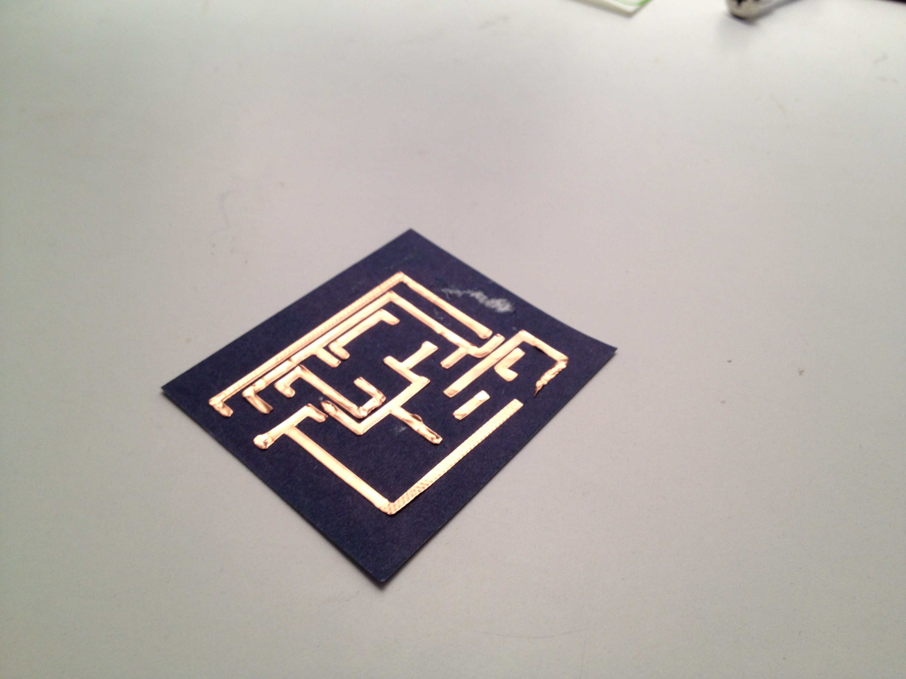
Documentation/indd/Links/IMG_2585.JPG
