makerjawn/oneKey/Documentation/indd/Links/IMG_2590.JPG

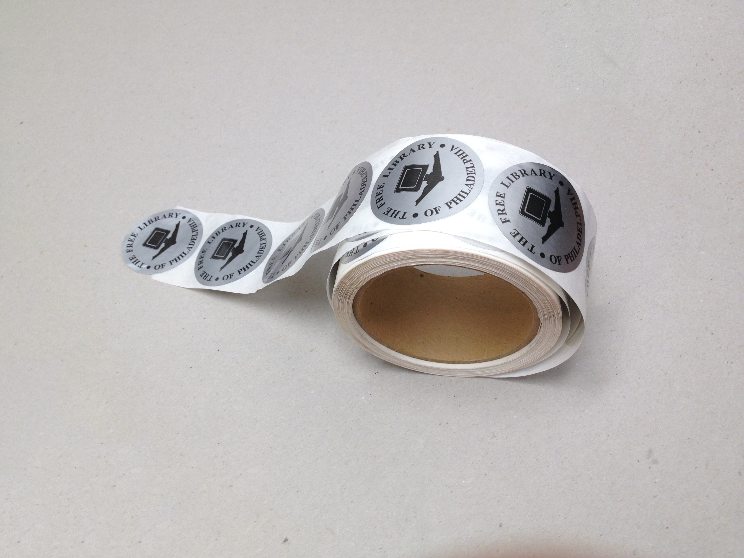
Documentation/indd/Links/IMG_2590.JPG
