makerjawn/oneKey/Documentation/indd/Links/IMG_2595.JPG

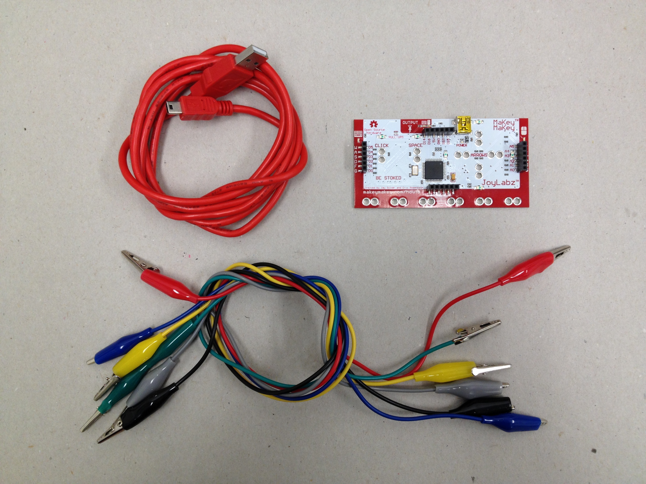
Documentation/indd/Links/IMG_2595.JPG
