makerjawn/oneKey/Documentation/indd/Links/IMG_2599.JPG

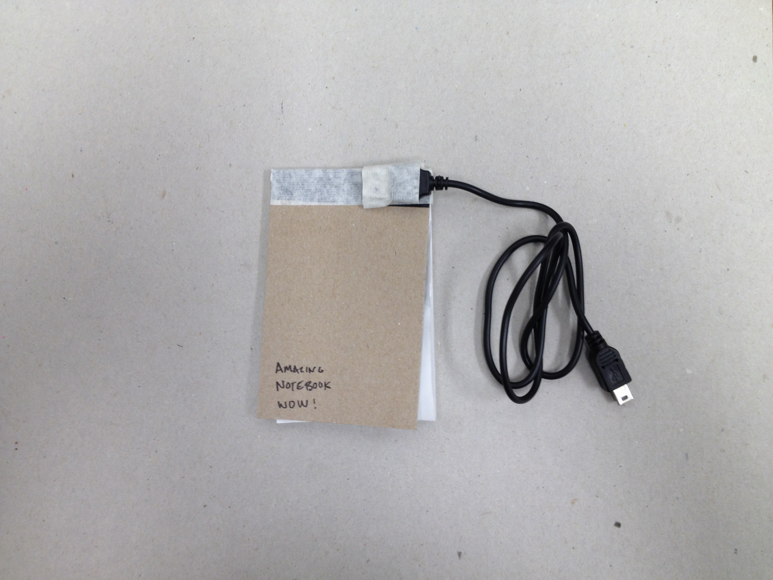
Documentation/indd/Links/IMG_2599.JPG
