makerjawn/oneKey/Documentation/indd/Links/IMG_20140208_192333.jpg

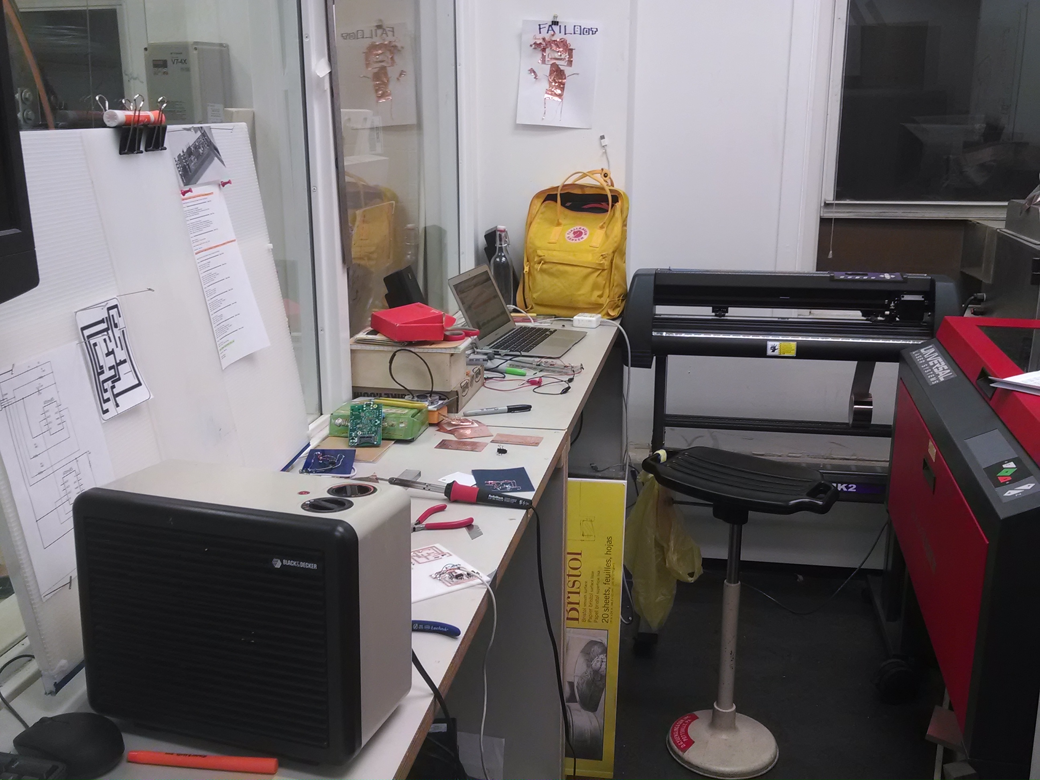
Documentation/indd/Links/IMG_20140208_192333.jpg
