makerjawn/oneKey/Documentation/indd/Links/IMG_20140212_152709625_HDR.jpg

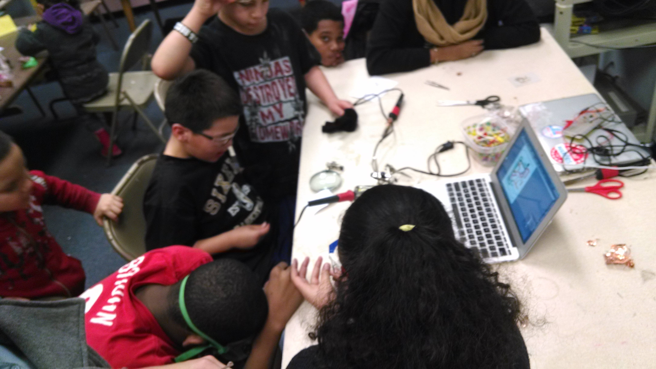
Documentation/indd/Links/IMG_20140212_152709625_HDR.jpg
