makerjawn/oneKey/Documentation/indd/Links/IMG_20140312_160443847.jpg

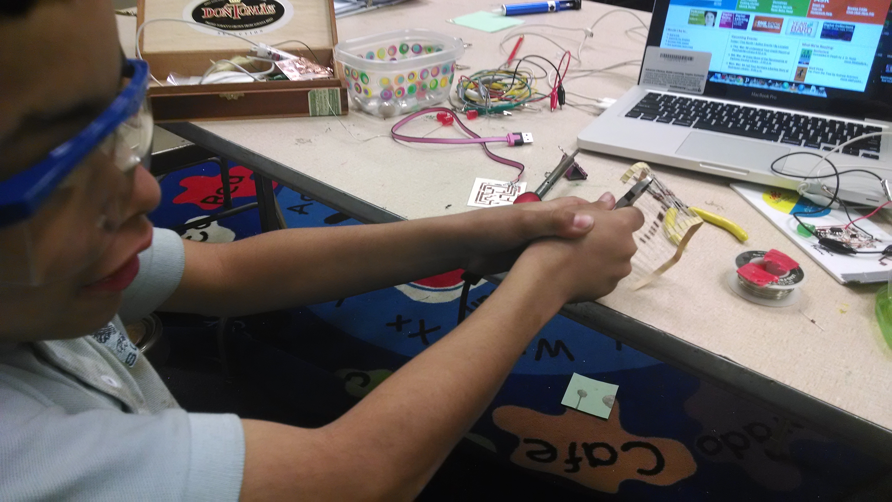
Documentation/indd/Links/IMG_20140312_160443847.jpg
