makerjawn/oneKey/Documentation/indd/Links/IMG_20140312_162255890.jpg

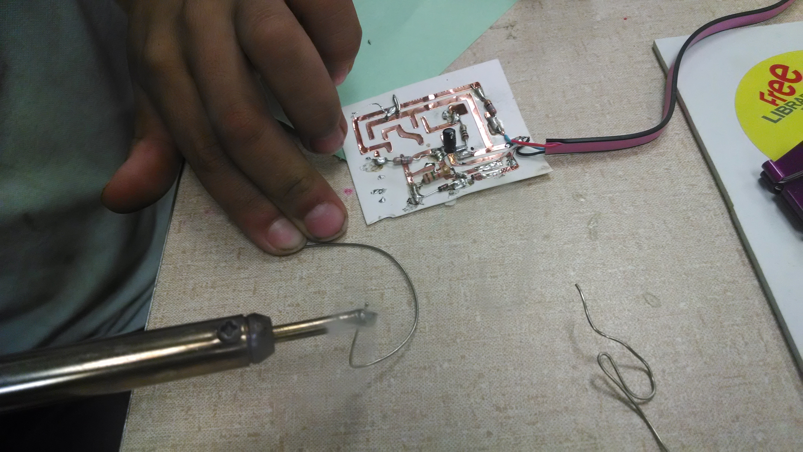
Documentation/indd/Links/IMG_20140312_162255890.jpg
