makerjawn/oneKey/Documentation/indd/Links/IMG_20140312_172556216_HDR.jpg

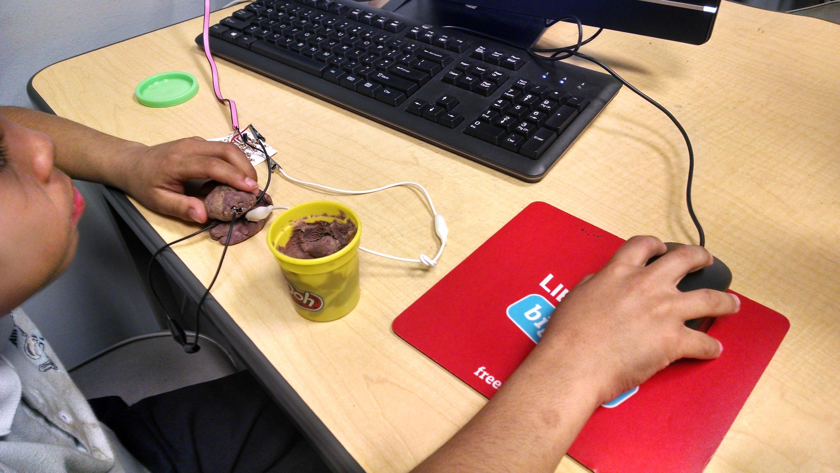
Documentation/indd/Links/IMG_20140312_172556216_HDR.jpg
