makerjawn/oneKey/Documentation/indd/Links/IMG_20140312_173550255.jpg

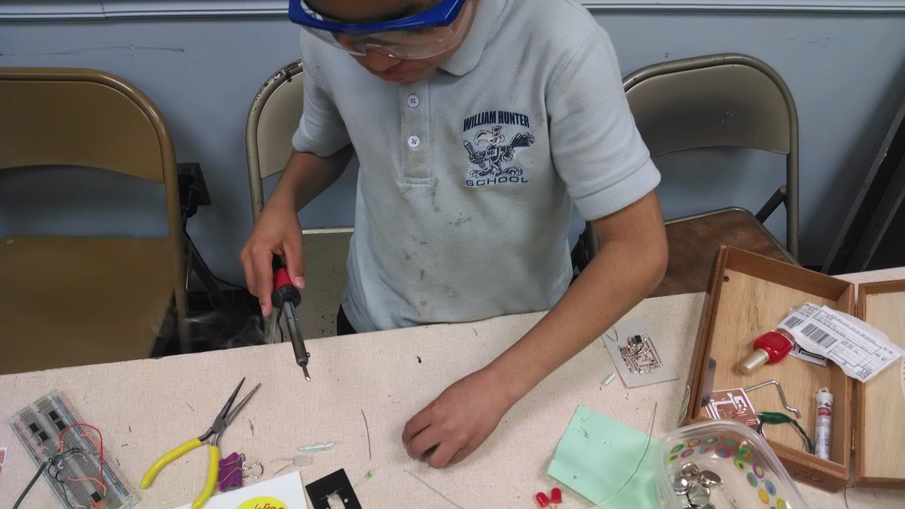
Documentation/indd/Links/IMG_20140312_173550255.jpg
