makerjawn/oneKey/Documentation/indd/Links/IMG_20140312_174240738.jpg

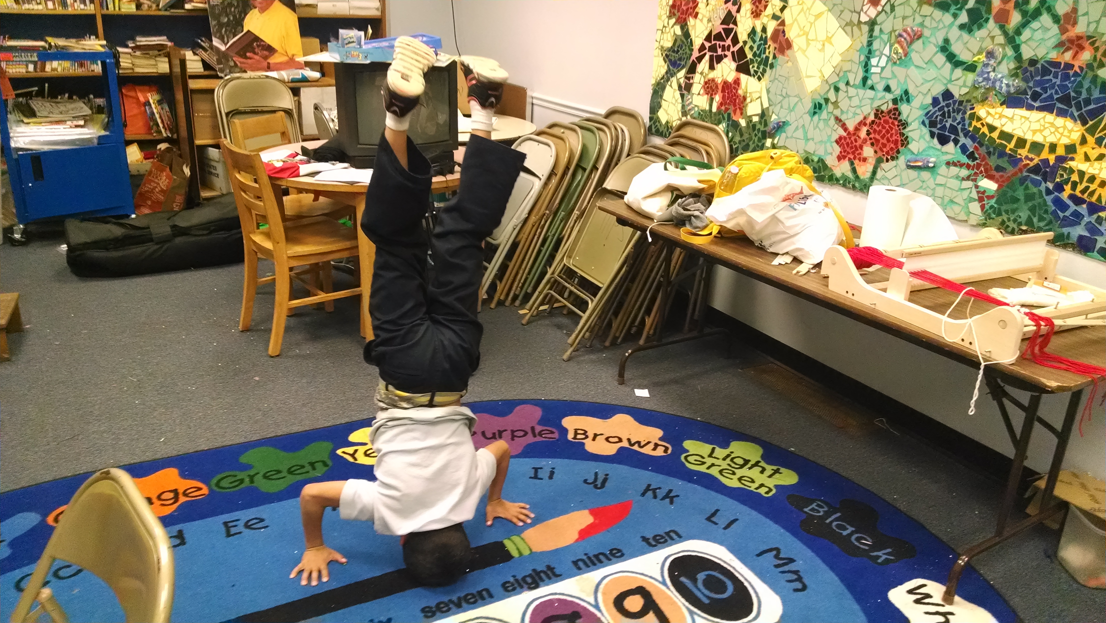
Documentation/indd/Links/IMG_20140312_174240738.jpg
