makerjawn/oneKey/Documentation/indd/Links/IMG_20140312_174634767.jpg

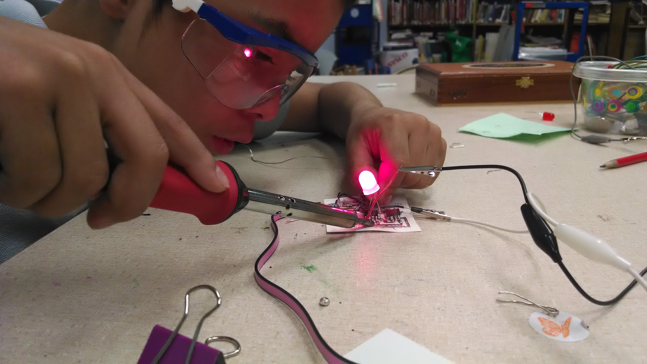
Documentation/indd/Links/IMG_20140312_174634767.jpg
