makerjawn/oneKey/Documentation/indd/Links/IMG_20140312_175126512.jpg

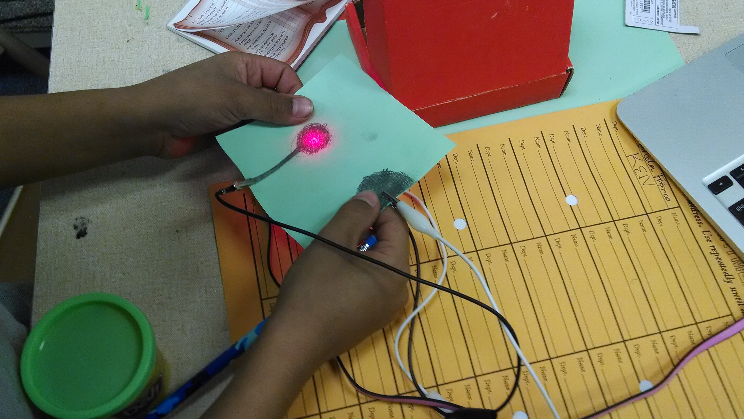
Documentation/indd/Links/IMG_20140312_175126512.jpg
