makerjawn/oneKey/Documentation/indd/Links/IMG_20140314_170547436.jpg

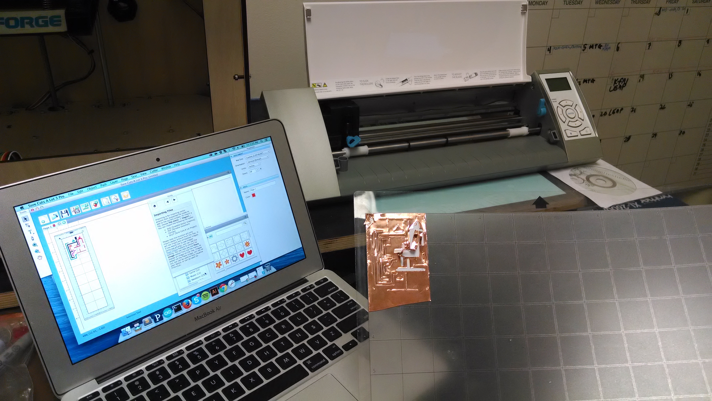
Documentation/indd/Links/IMG_20140314_170547436.jpg
