makerjawn/oneKey/Documentation/indd/Links/IMG_20140417_024407771.jpg

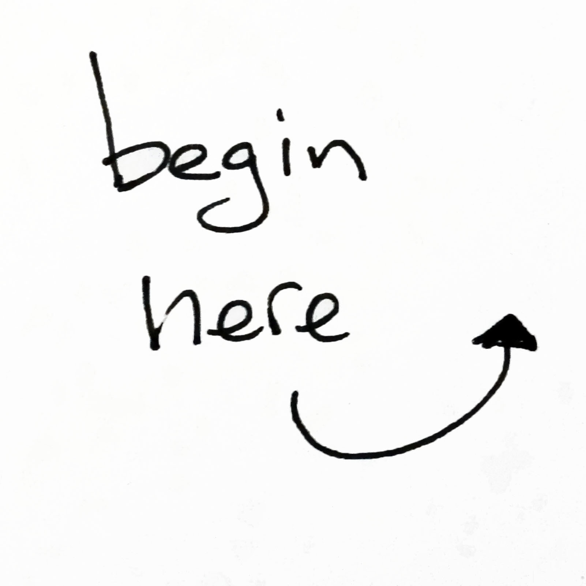
Documentation/indd/Links/IMG_20140417_024407771.jpg
