makerjawn/oneKey/Documentation/indd/Links/IMG_2591222222.jpg

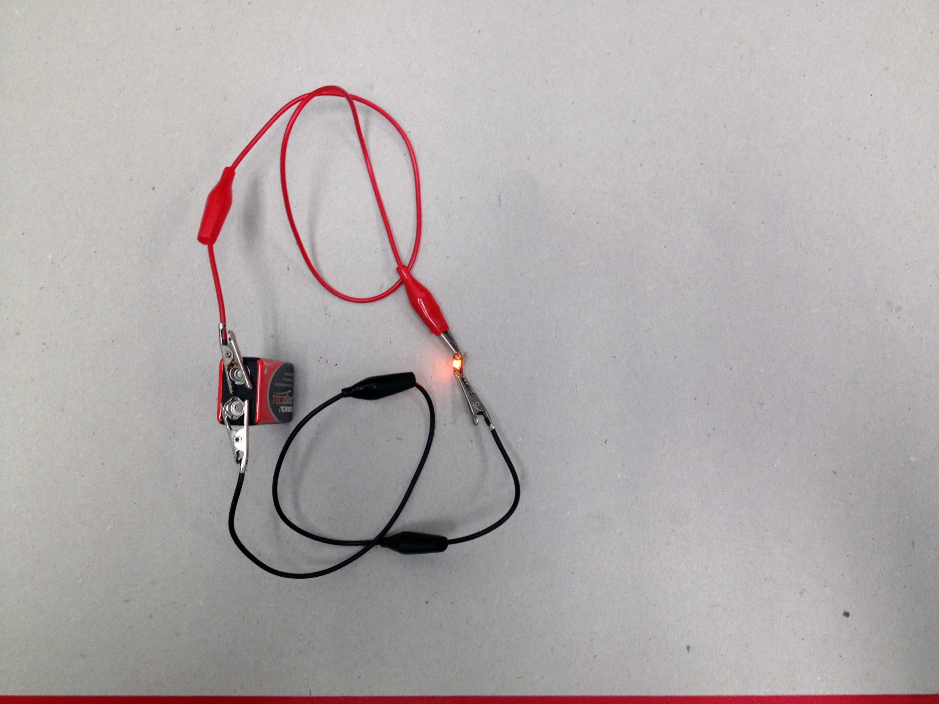
Documentation/indd/Links/IMG_2591222222.jpg
