makerjawn/oneKey/Documentation/indd/Links/IMG_259124444444.jpg

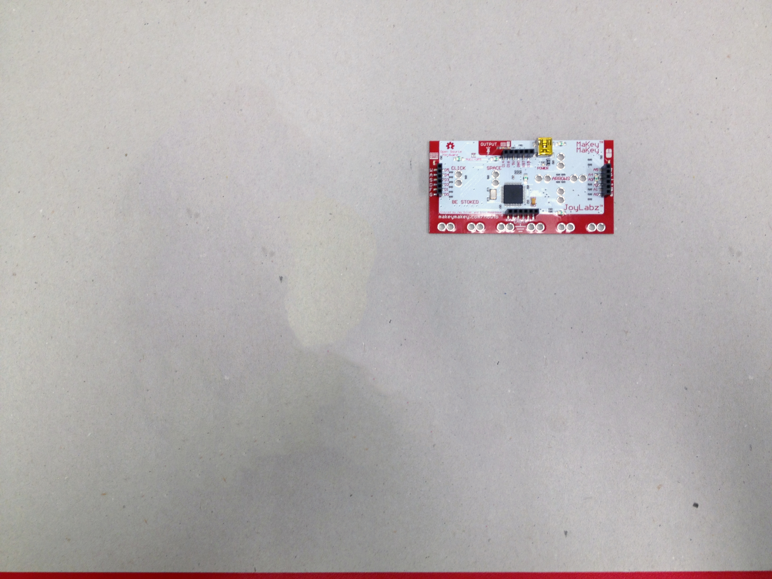
Documentation/indd/Links/IMG_259124444444.jpg
