makerjawn/oneKey/Documentation/indd/Links/MMMv1 copy.png

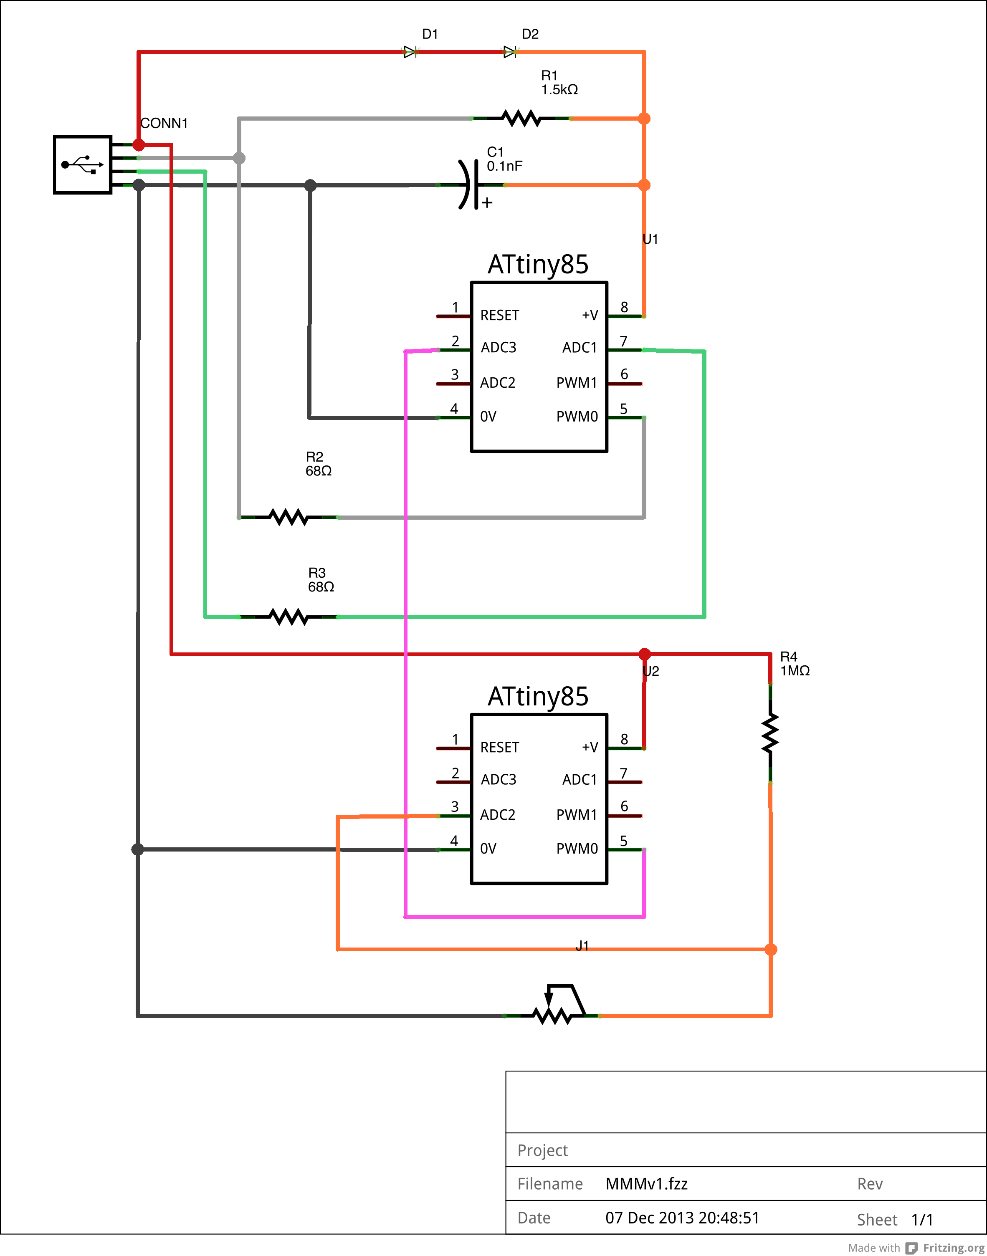
Documentation/indd/Links/MMMv1 copy.png
