makerjawn/oneKey/Documentation/indd/Links/pensacola-mess-hall.jpg

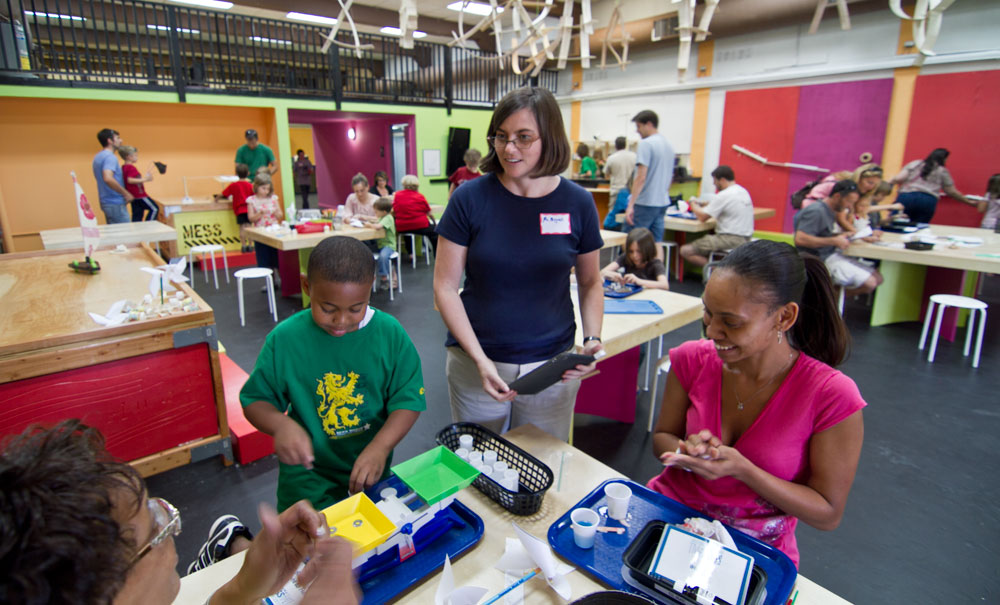
Documentation/indd/Links/pensacola-mess-hall.jpg
