makerjawn/oneKey/Documentation/indd/Links/Scan 19.jpeg

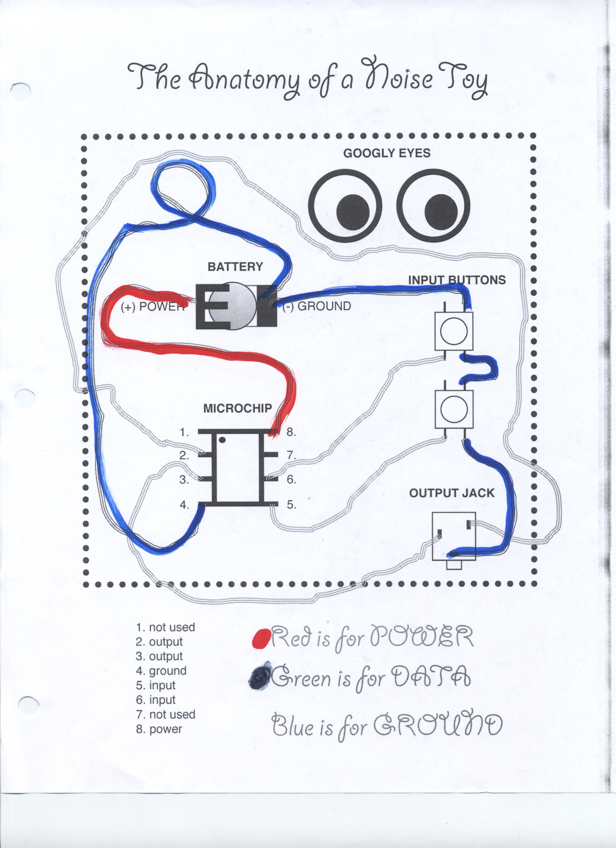
Documentation/indd/Links/Scan 19.jpeg
