makerjawn/oneKey/Documentation/indd/Links/Screen Shot 2013-10-24 at 4.46.22 AM.png

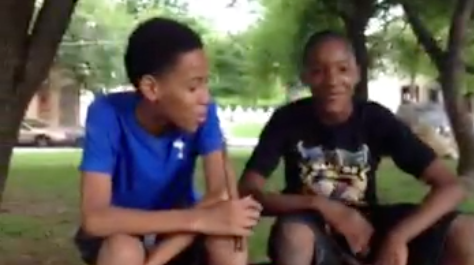
Documentation/indd/Links/Screen Shot 2013-10-24 at 4.46.22 AM.png
