makerjawn/oneKey/Documentation/indd/Links/Screen Shot 2013-10-24 at 4.49.20 AM.png

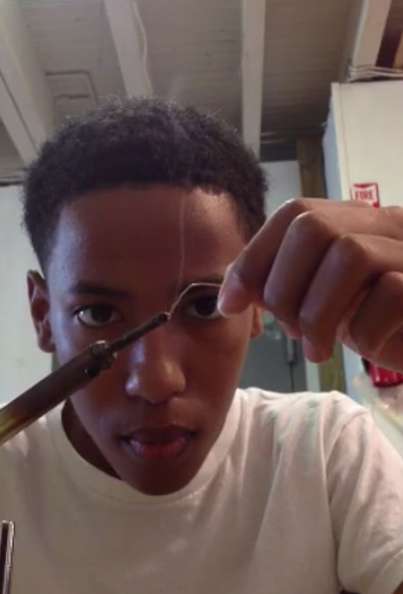
Documentation/indd/Links/Screen Shot 2013-10-24 at 4.49.20 AM.png
