makerjawn/oneKey/Documentation/indd/Links/Screen Shot 2013-10-24 at 5.36.23 AM.png

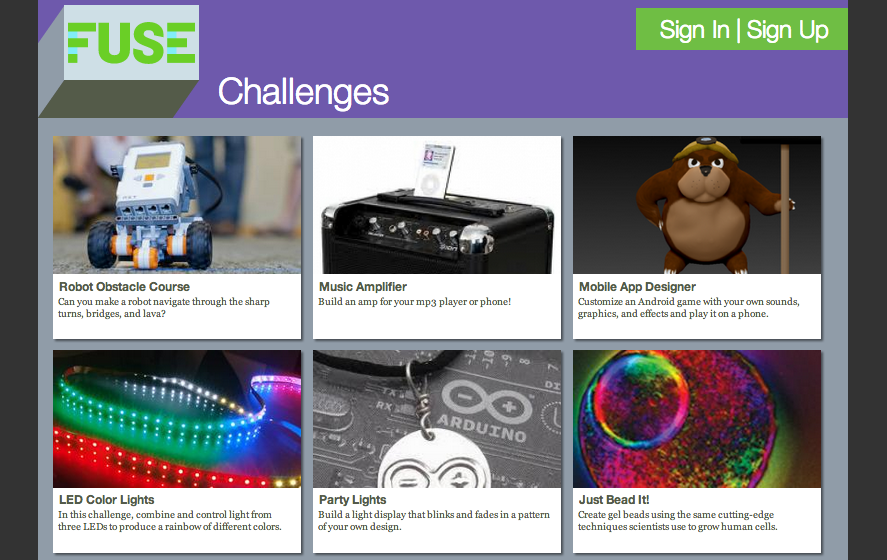
Documentation/indd/Links/Screen Shot 2013-10-24 at 5.36.23 AM.png
