makerjawn/oneKey/Documentation/indd/Links/Screen Shot 2013-10-24 at 5.38.16 AM.png

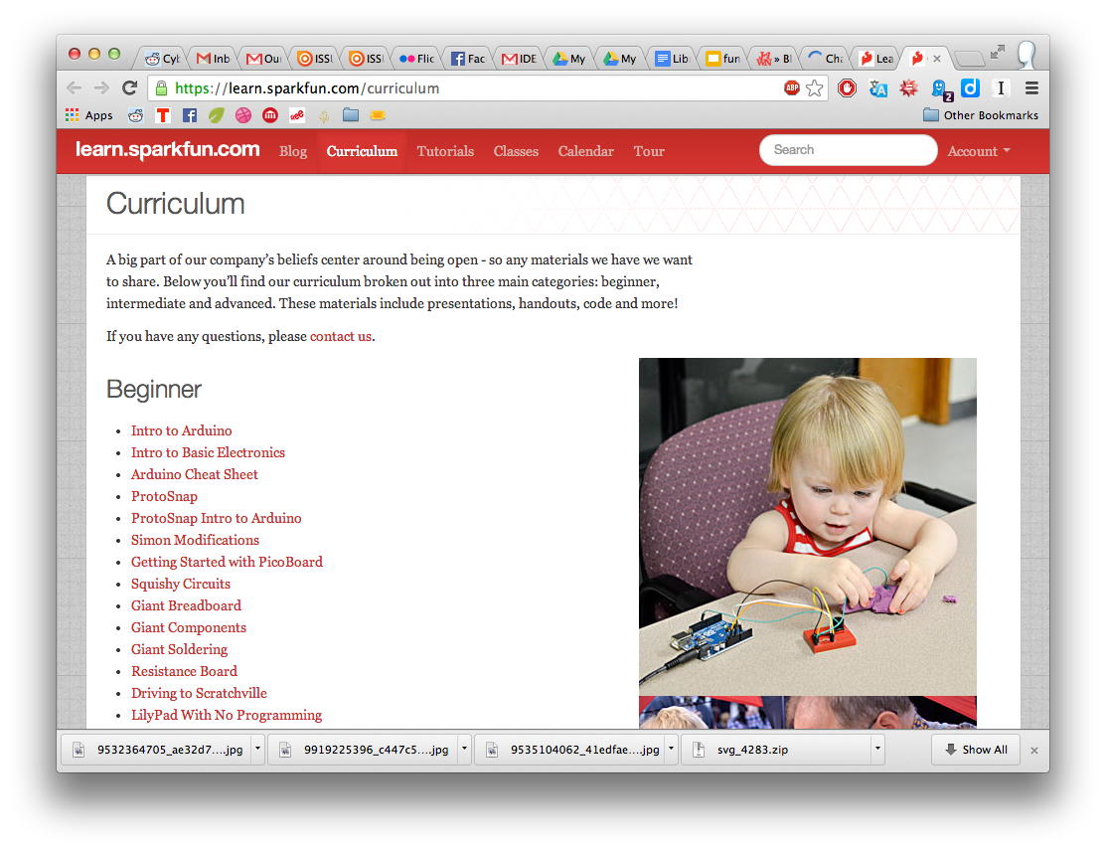
Documentation/indd/Links/Screen Shot 2013-10-24 at 5.38.16 AM.png
