makerjawn/oneKey/Documentation/indd/Links/Screen Shot 2013-12-04 at 9.44.06 PM.png

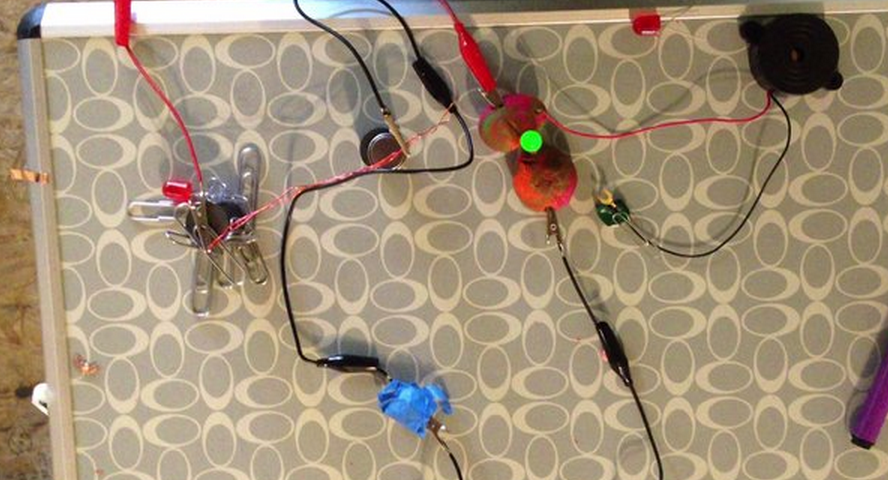
Documentation/indd/Links/Screen Shot 2013-12-04 at 9.44.06 PM.png
