makerjawn/oneKey/Documentation/indd/Links/Screen Shot 2013-12-04 at 10.17.30 PM.png

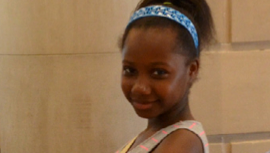
Documentation/indd/Links/Screen Shot 2013-12-04 at 10.17.30 PM.png
