makerjawn/oneKey/Documentation/indd/Links/Screen Shot 2013-12-05 at 2.02.23 AM.png

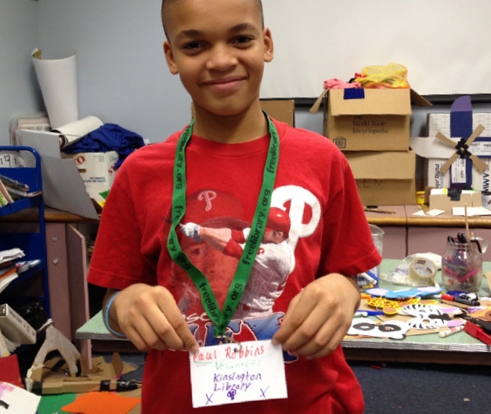
Documentation/indd/Links/Screen Shot 2013-12-05 at 2.02.23 AM.png
