makerjawn/oneKey/Documentation/indd/Links/Screen Shot 2013-12-05 at 2.04.36 AM.png

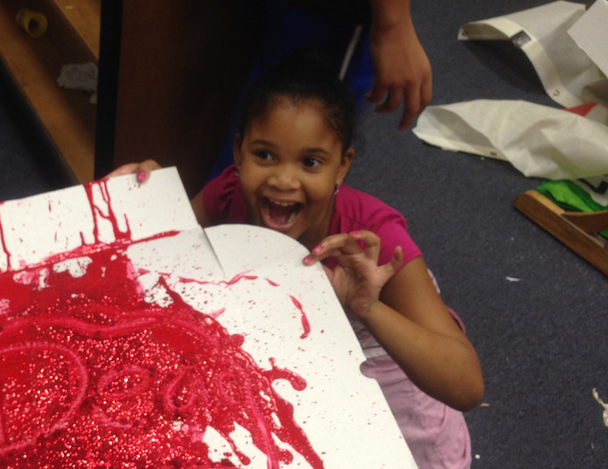
Documentation/indd/Links/Screen Shot 2013-12-05 at 2.04.36 AM.png
