makerjawn/oneKey/Documentation/indd/Links/Screen Shot 2013-12-05 at 6.15.53 AM.png

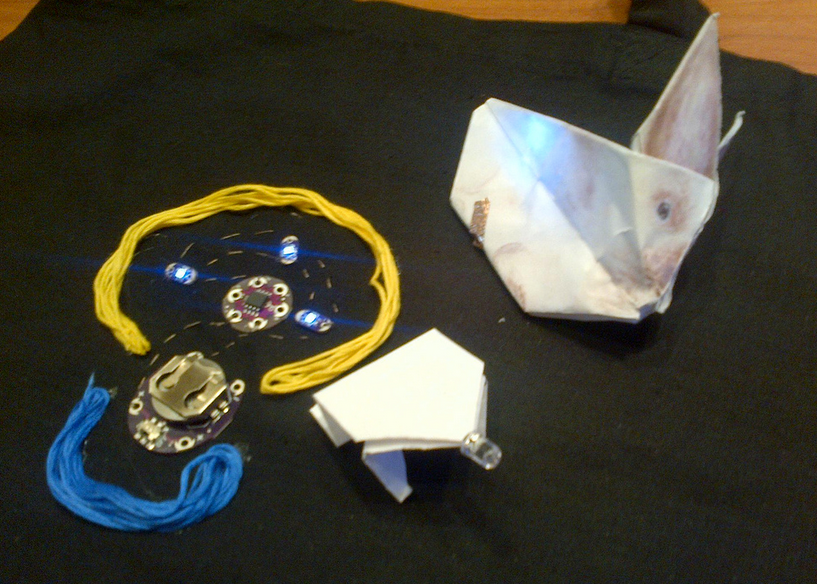
Documentation/indd/Links/Screen Shot 2013-12-05 at 6.15.53 AM.png
