makerjawn/oneKey/Documentation/indd/Links/Screen Shot 2013-12-05 at 6.18.17 AM.png

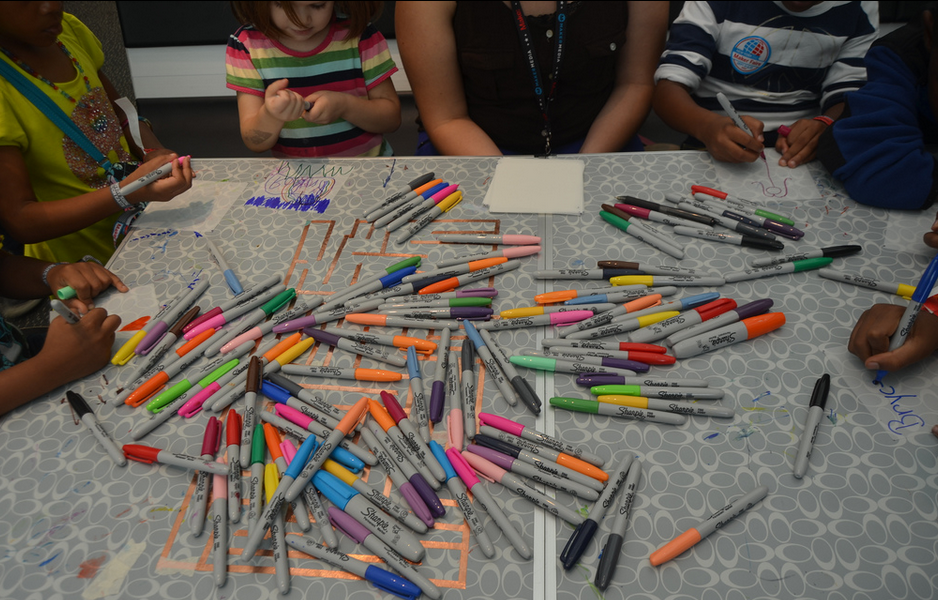
Documentation/indd/Links/Screen Shot 2013-12-05 at 6.18.17 AM.png
