makerjawn/oneKey/Documentation/indd/Links/Screen Shot 2013-12-05 at 6.21.05 AM.png

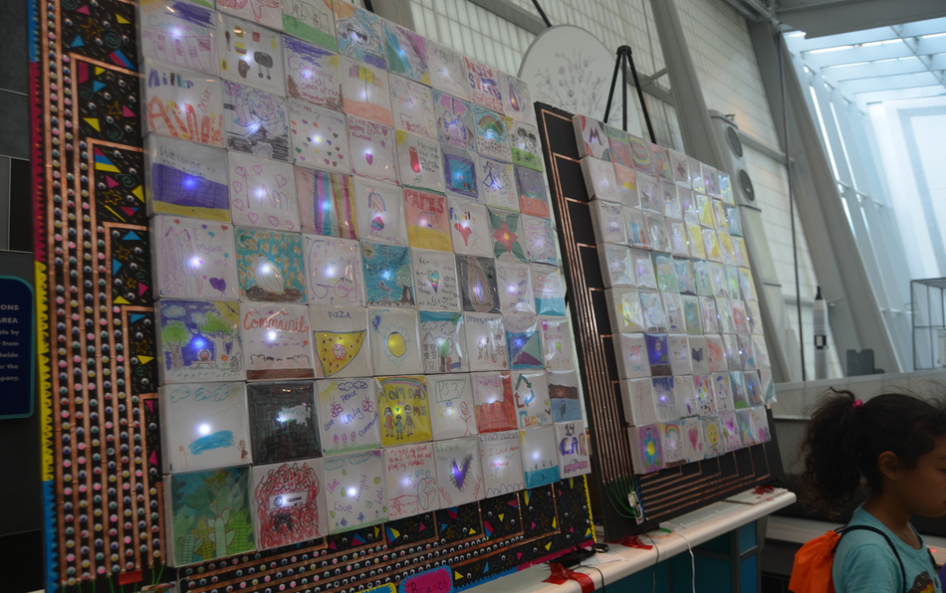
Documentation/indd/Links/Screen Shot 2013-12-05 at 6.21.05 AM.png
