makerjawn/oneKey/Documentation/indd/Links/Screen Shot 2013-12-05 at 9.50.16 AM.png

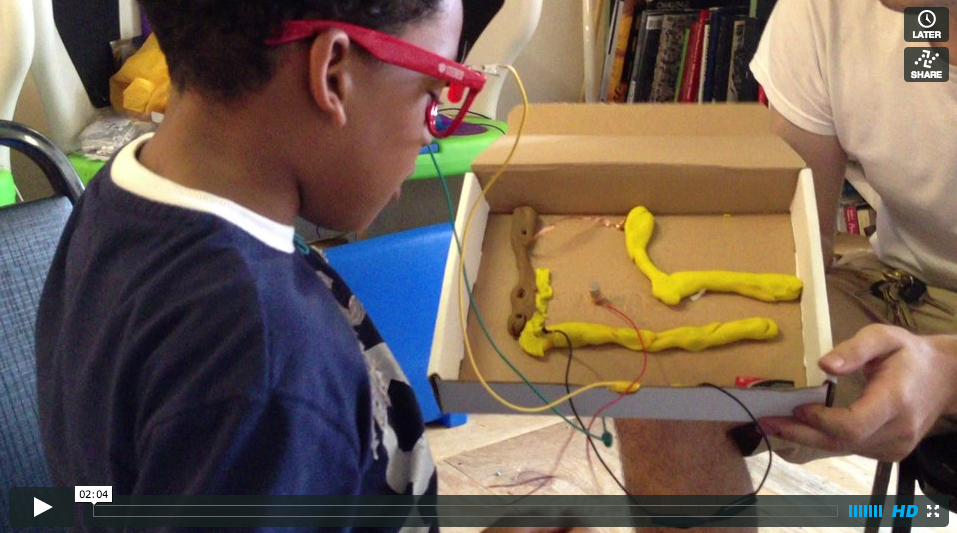
Documentation/indd/Links/Screen Shot 2013-12-05 at 9.50.16 AM.png
