makerjawn/oneKey/Documentation/indd/Links/Screen Shot 2013-12-11 at 8.12.12 PM.png

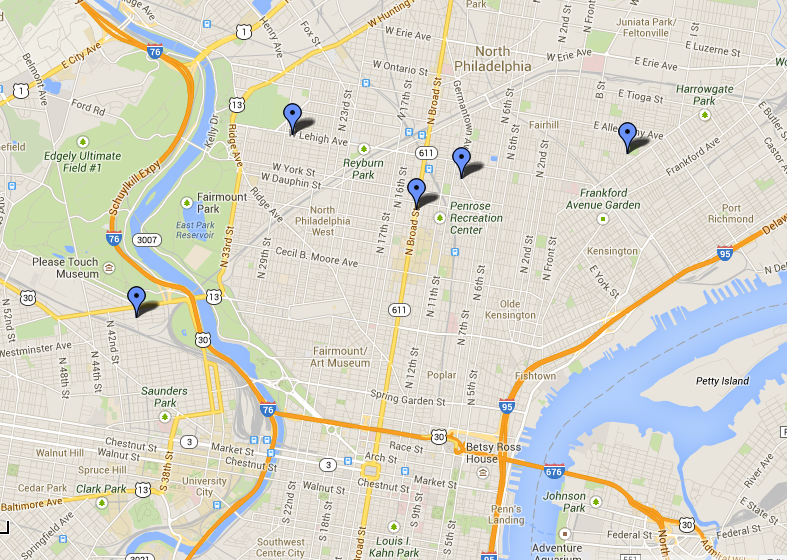
Documentation/indd/Links/Screen Shot 2013-12-11 at 8.12.12 PM.png
