makerjawn/oneKey/Documentation/indd/Links/Screen Shot 2013-12-11 at 9.43.09 PM.png

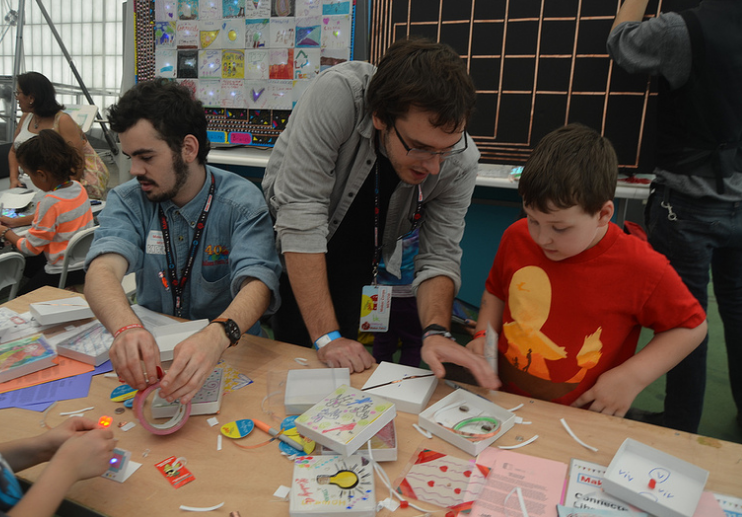
Documentation/indd/Links/Screen Shot 2013-12-11 at 9.43.09 PM.png
