makerjawn/oneKey/Documentation/indd/Links/Screen Shot 2013-12-11 at 9.44.21 PM.png

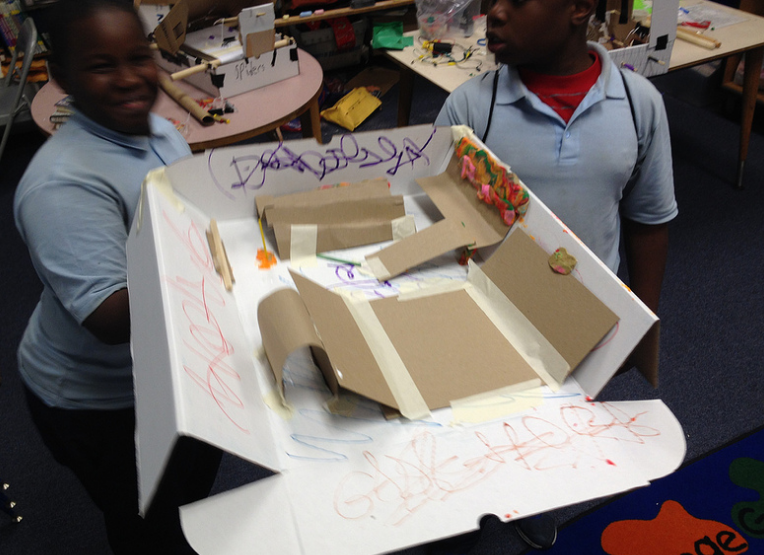
Documentation/indd/Links/Screen Shot 2013-12-11 at 9.44.21 PM.png
