makerjawn/oneKey/Documentation/indd/Links/Screen Shot 2013-12-11 at 10.06.49 PM.png

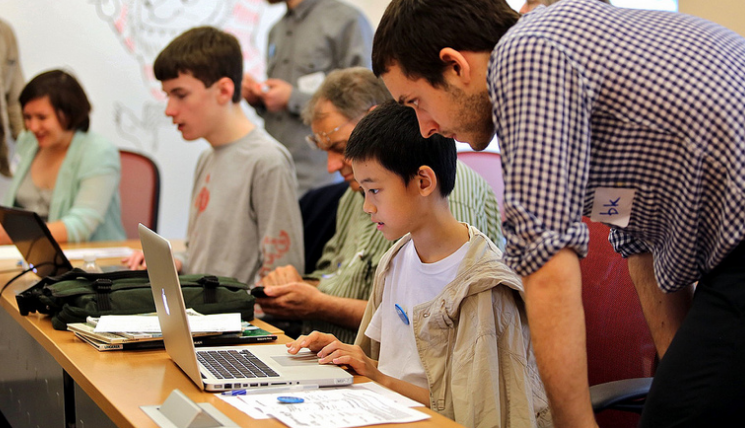
Documentation/indd/Links/Screen Shot 2013-12-11 at 10.06.49 PM.png
