makerjawn/oneKey/Documentation/indd/Links/Screen Shot 2013-12-11 at 10.15.31 PM.png

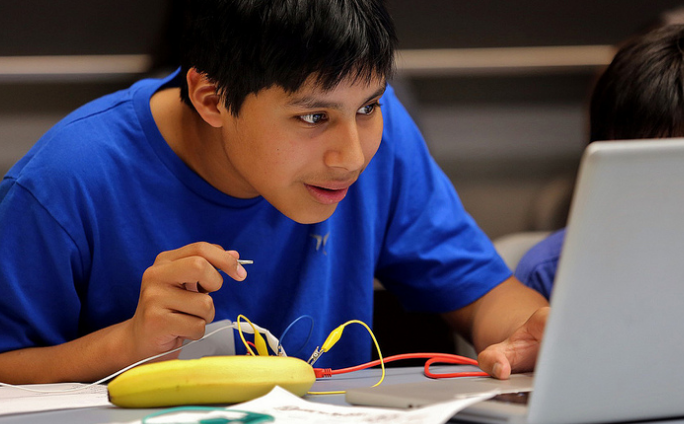
Documentation/indd/Links/Screen Shot 2013-12-11 at 10.15.31 PM.png
