makerjawn/oneKey/Documentation/indd/Links/Screen Shot 2013-12-12 at 1.15.24 AM.png

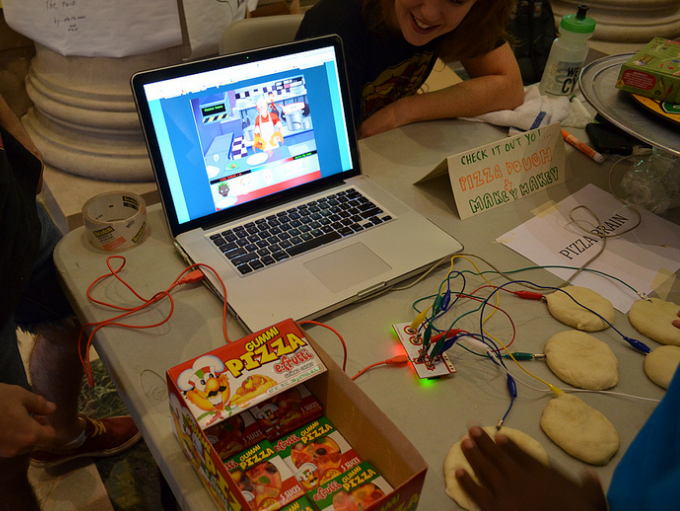
Documentation/indd/Links/Screen Shot 2013-12-12 at 1.15.24 AM.png
