makerjawn/oneKey/Documentation/indd/Links/Screen Shot 2013-12-12 at 12.04.01 AM.png

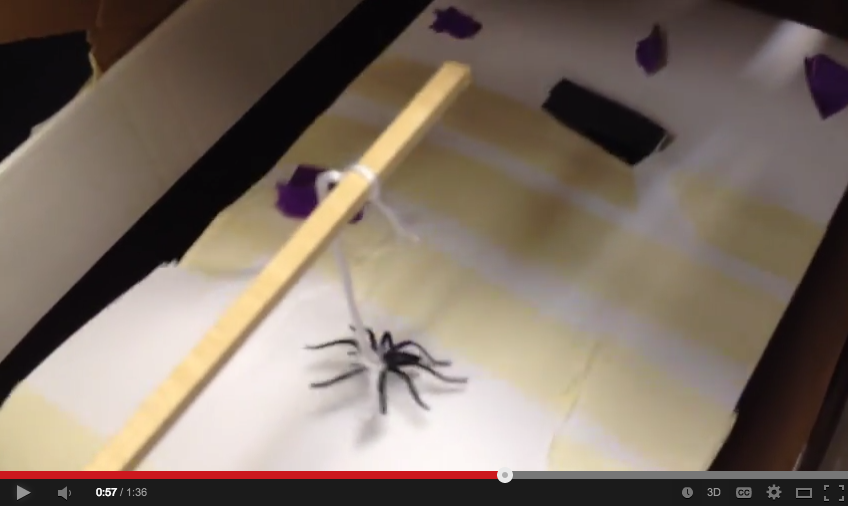
Documentation/indd/Links/Screen Shot 2013-12-12 at 12.04.01 AM.png
