makerjawn/oneKey/Documentation/indd/Links/Screen Shot 2013-12-15 at 1.40.58 PM.png

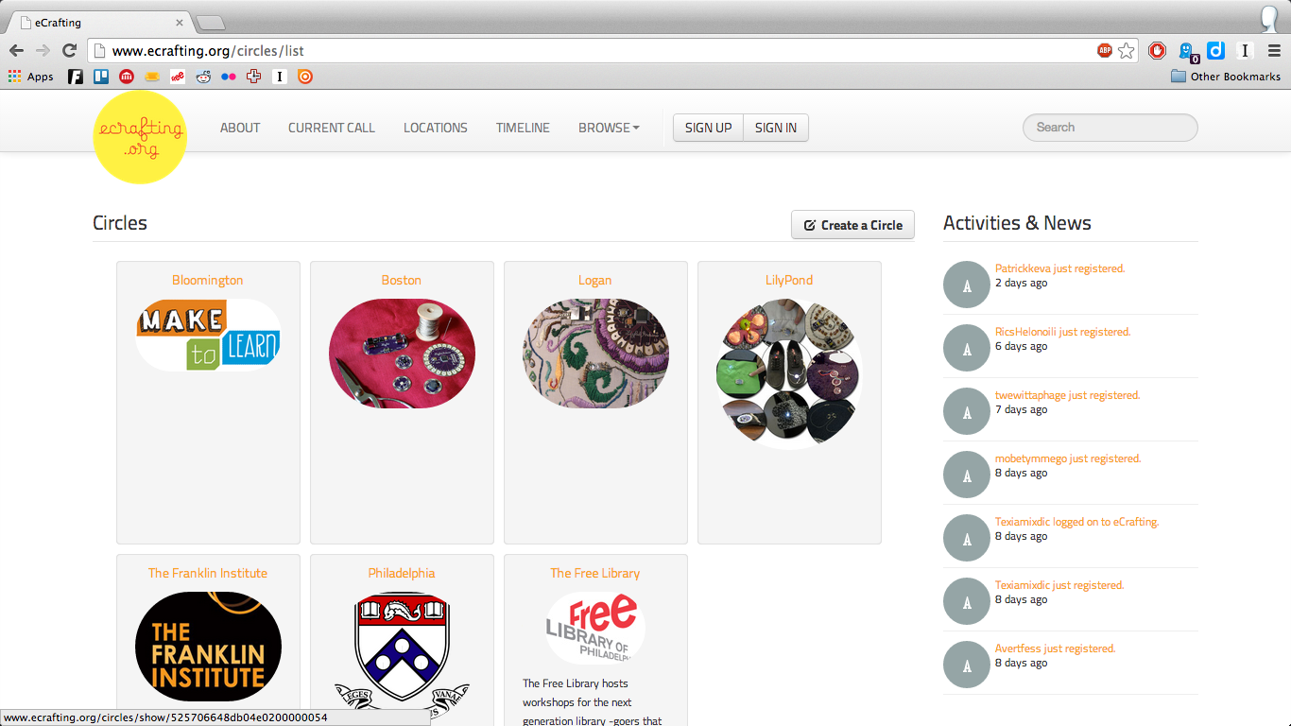
Documentation/indd/Links/Screen Shot 2013-12-15 at 1.40.58 PM.png
