makerjawn/oneKey/Documentation/indd/Links/Screen Shot 2013-12-15 at 9.11.58 AM.png

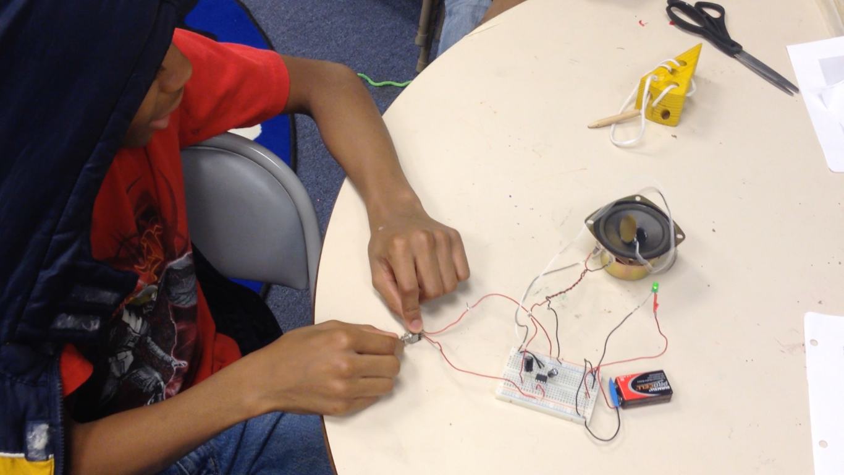
Documentation/indd/Links/Screen Shot 2013-12-15 at 9.11.58 AM.png
