makerjawn/oneKey/Documentation/indd/Links/Screen Shot 2013-12-15 at 9.22.06 AM.png

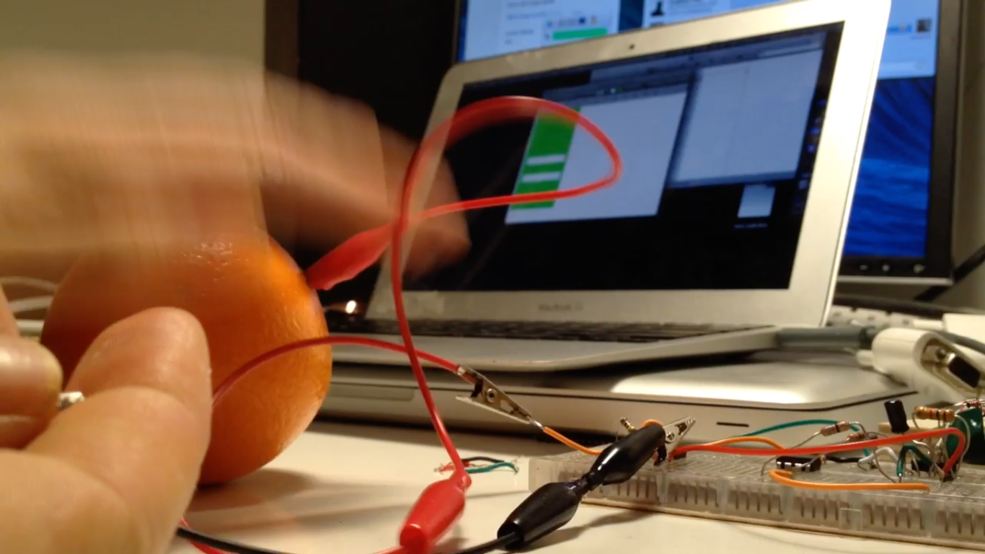
Documentation/indd/Links/Screen Shot 2013-12-15 at 9.22.06 AM.png
