makerjawn/oneKey/Documentation/indd/Links/Screen Shot 2013-12-15 at 10.34.39 AM.png

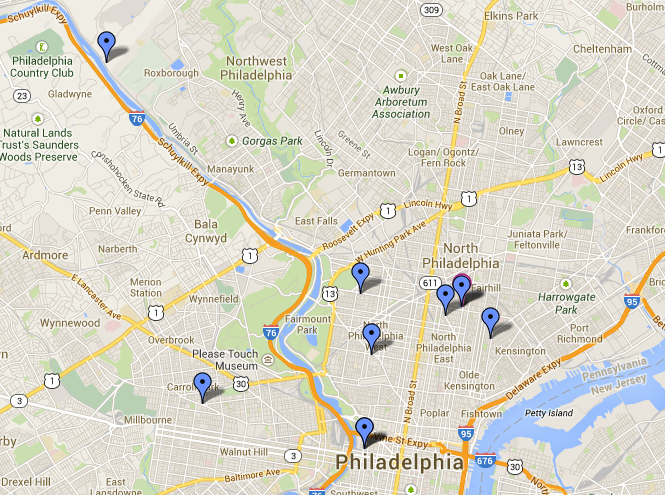
Documentation/indd/Links/Screen Shot 2013-12-15 at 10.34.39 AM.png
