makerjawn/oneKey/Documentation/indd/Links/Screen Shot 2014-02-18 at 1.29.39 PM.png

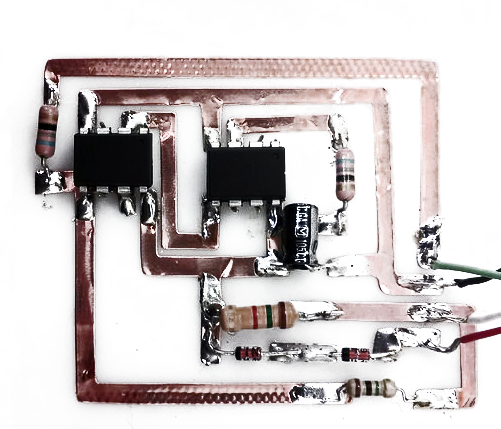
Documentation/indd/Links/Screen Shot 2014-02-18 at 1.29.39 PM.png
