makerjawn/oneKey/Documentation/indd/Links/Screen Shot 2014-03-17 at 2.09.37 AM.png

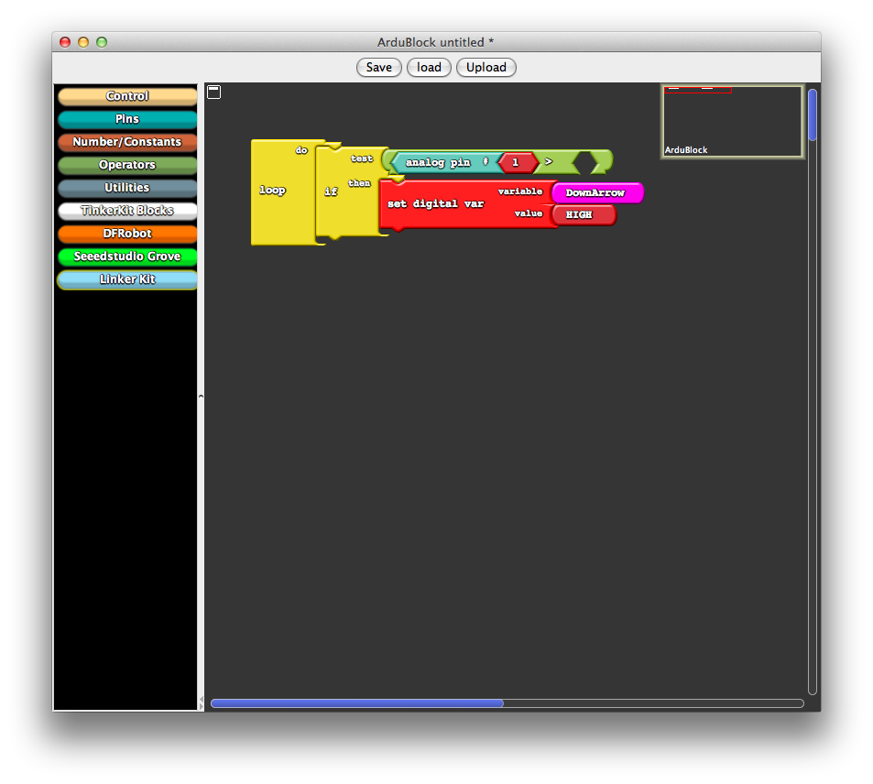
Documentation/indd/Links/Screen Shot 2014-03-17 at 2.09.37 AM.png
