makerjawn/oneKey/Documentation/indd/Links/Screen Shot 2014-03-17 at 3.06.07 AM.png

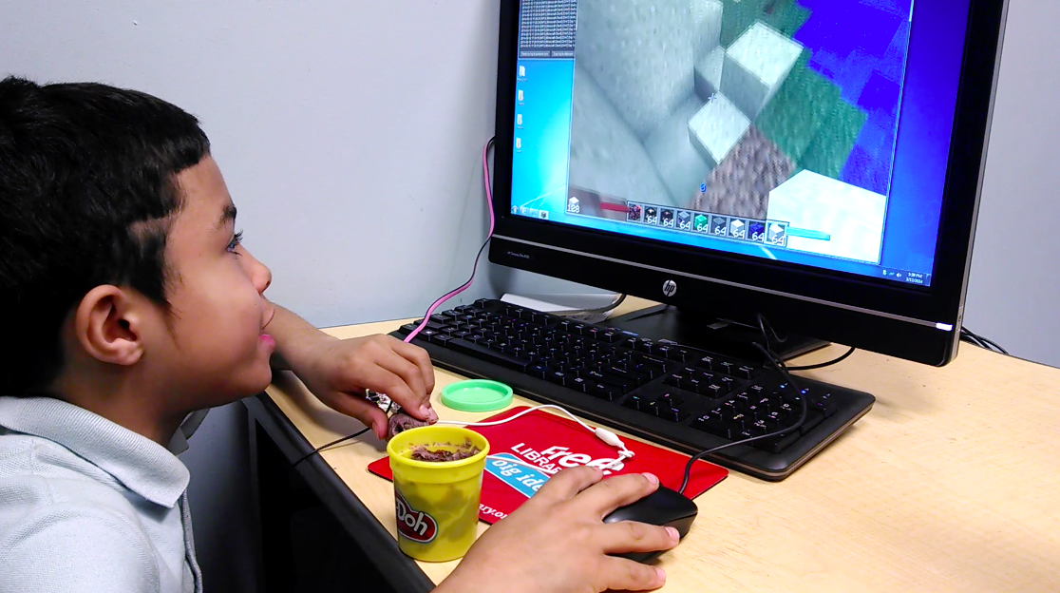
Documentation/indd/Links/Screen Shot 2014-03-17 at 3.06.07 AM.png
