makerjawn/oneKey/Documentation/indd/Links/Screen Shot 2014-03-17 at 4.25.41 AM.png

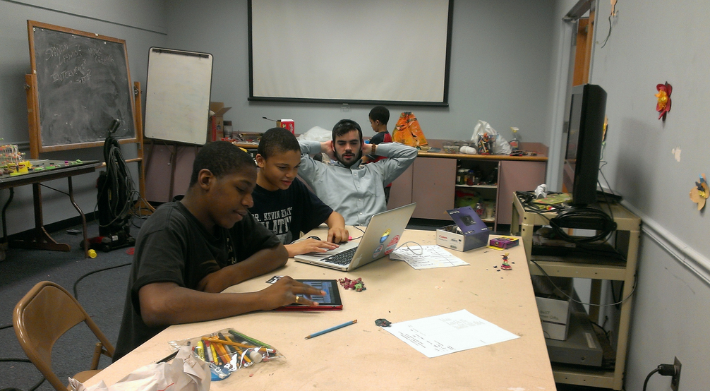
Documentation/indd/Links/Screen Shot 2014-03-17 at 4.25.41 AM.png
