makerjawn/oneKey/Documentation/indd/Links/Screen Shot 2014-04-21 at 5.14.53 AM.png

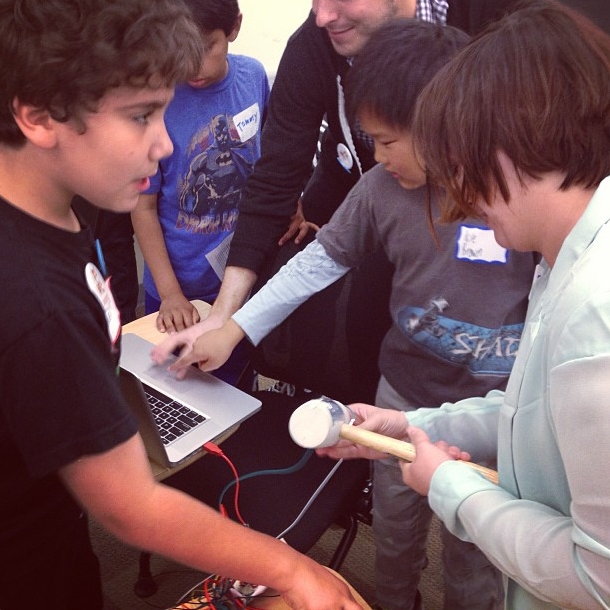
Documentation/indd/Links/Screen Shot 2014-04-21 at 5.14.53 AM.png
