makerjawn/oneKey/Documentation/indd/Links/Screen Shot 2014-04-21 at 6.20.49 AM.png

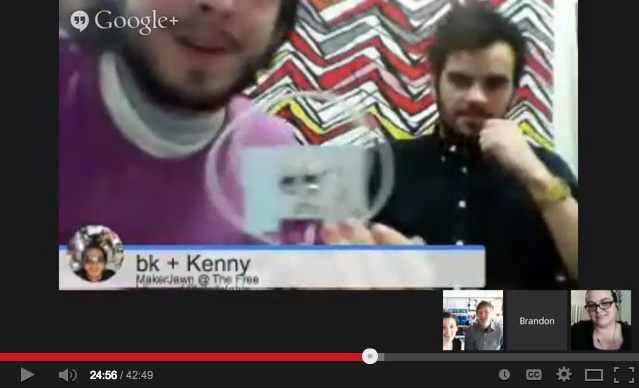
Documentation/indd/Links/Screen Shot 2014-04-21 at 6.20.49 AM.png
