makerjawn/oneKey/Documentation/indd/Links/Screen Shot 2014-04-21 at 6.21.43 AM.png

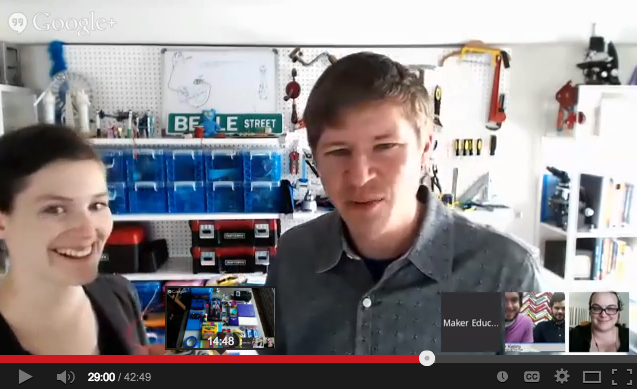
Documentation/indd/Links/Screen Shot 2014-04-21 at 6.21.43 AM.png
