makerjawn/oneKey/Documentation/indd/Links/squish5.jpg

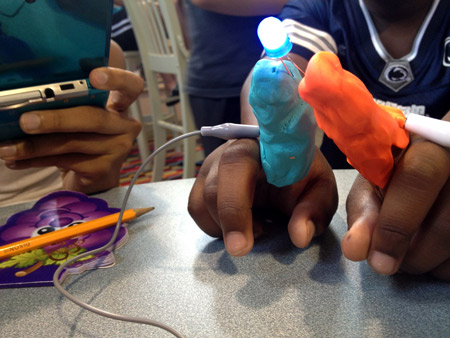
Documentation/indd/Links/squish5.jpg
