makerjawn/oneKey/Documentation/indd/Links/tower4.jpg

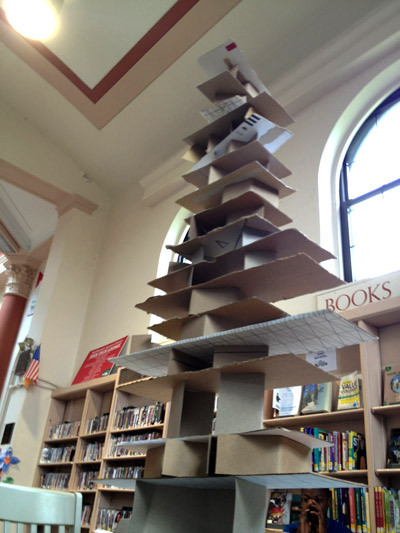
Documentation/indd/Links/tower4.jpg
