makerjawn/oneKey/Documentation/indd/Links/tumblr_mnraxekNdo1s43ovyo4_500 (1).jpg

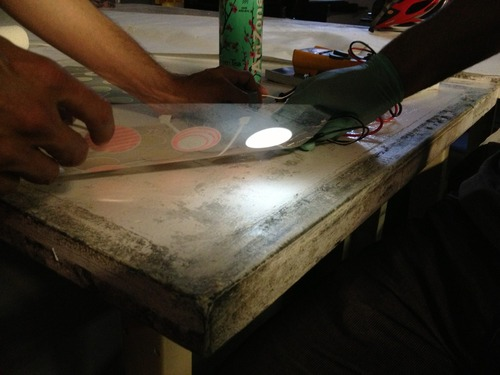
Documentation/indd/Links/tumblr_mnraxekNdo1s43ovyo4_500 (1).jpg
