makerjawn/oneKey/Documentation/indd/Links/tumblr_mnraxekNdo1s43ovyo7_500.jpg

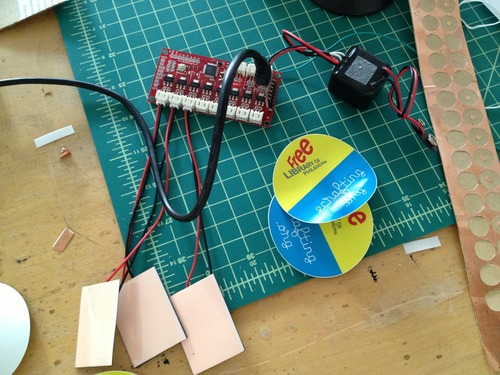
Documentation/indd/Links/tumblr_mnraxekNdo1s43ovyo7_500.jpg
