makerjawn/oneKey/Documentation/indd/Links/tumblr_mocdimlzP51snqljoo2_1280-1024x768.jpg

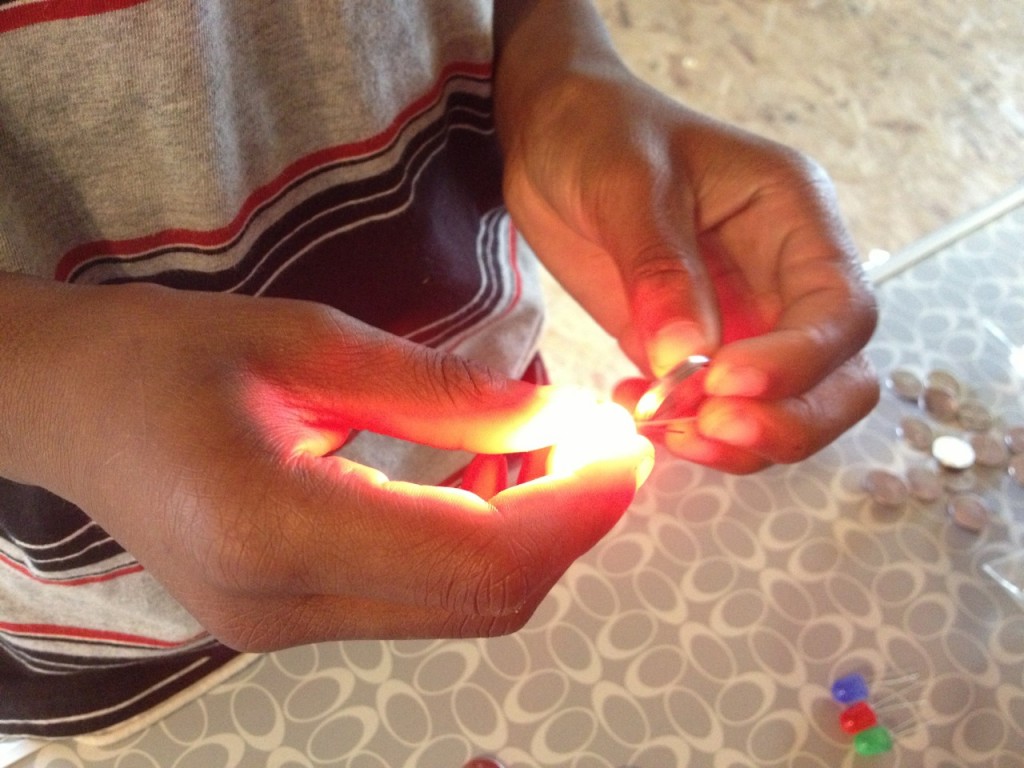
Documentation/indd/Links/tumblr_mocdimlzP51snqljoo2_1280-1024x768.jpg
