makerjawn/oneKey/Documentation/indd/Links/tumblr_mokd30aqiZ1snqljoo2_1280-683x1024.jpg

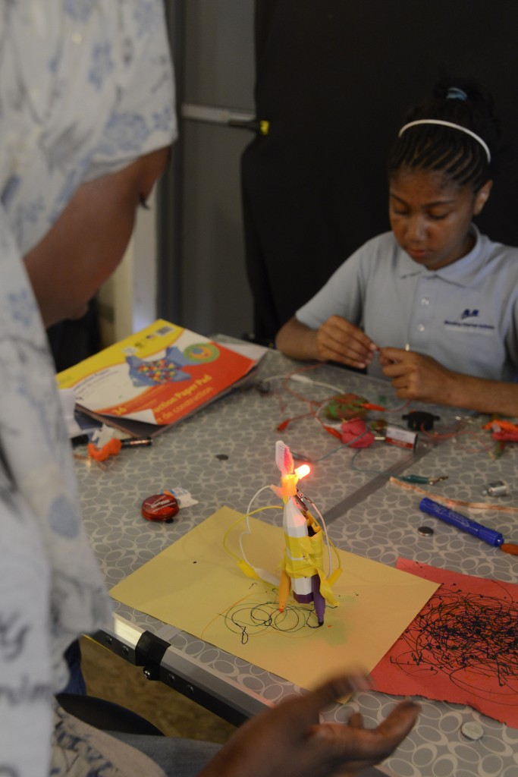
Documentation/indd/Links/tumblr_mokd30aqiZ1snqljoo2_1280-683x1024.jpg
