makerjawn/oneKey/Documentation/indd/Links/tumblr_moo5n70IFW1snqljoo1_1280-1024x768.jpg

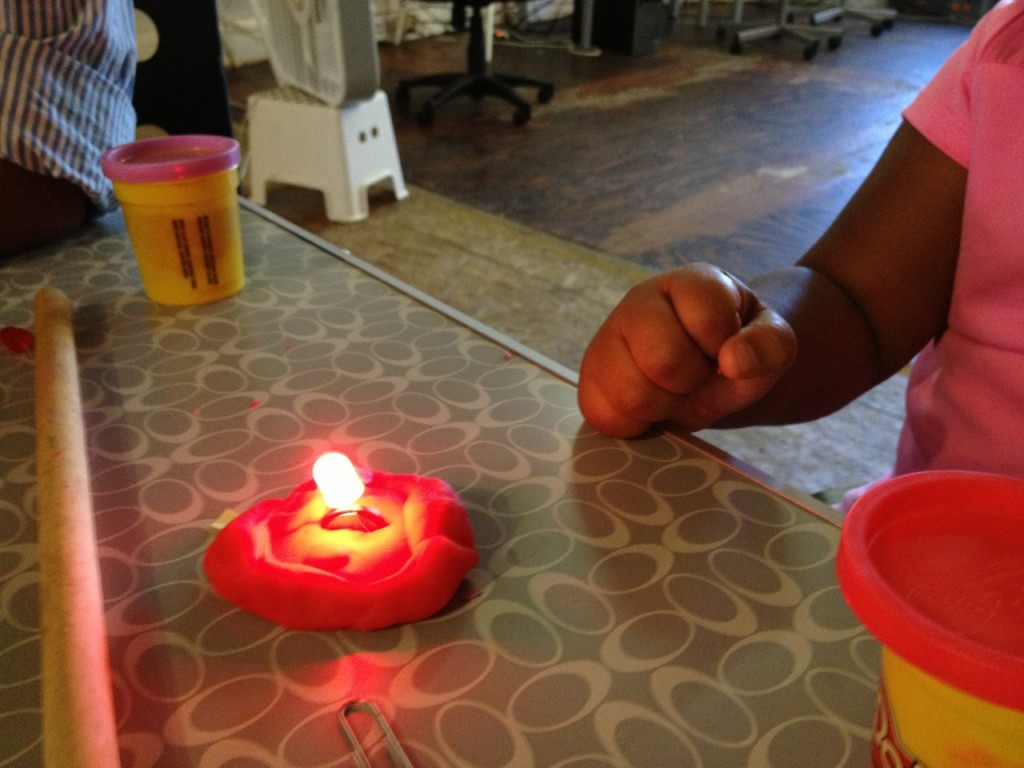
Documentation/indd/Links/tumblr_moo5n70IFW1snqljoo1_1280-1024x768.jpg
