makerjawn/oneKey/Documentation/indd/Links/tumblr_moo5n70IFW1snqljoo4_r1_1280.png

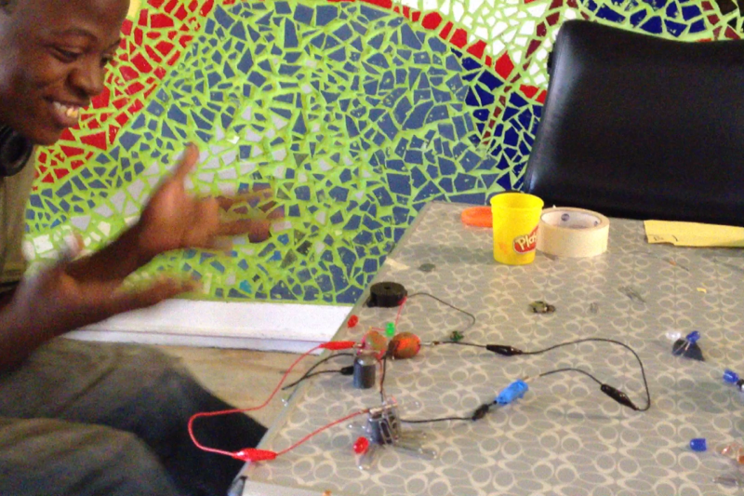
Documentation/indd/Links/tumblr_moo5n70IFW1snqljoo4_r1_1280.png
