makerjawn/oneKey/Documentation/indd/Links/tumblr_n2sojs4W4S1trm70to1_500.png

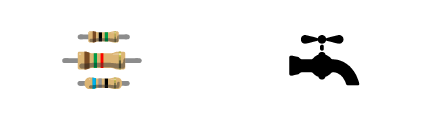
Documentation/indd/Links/tumblr_n2sojs4W4S1trm70to1_500.png
