makerjawn/oneKey/Documentation/indd/Links/Untitled-1.png

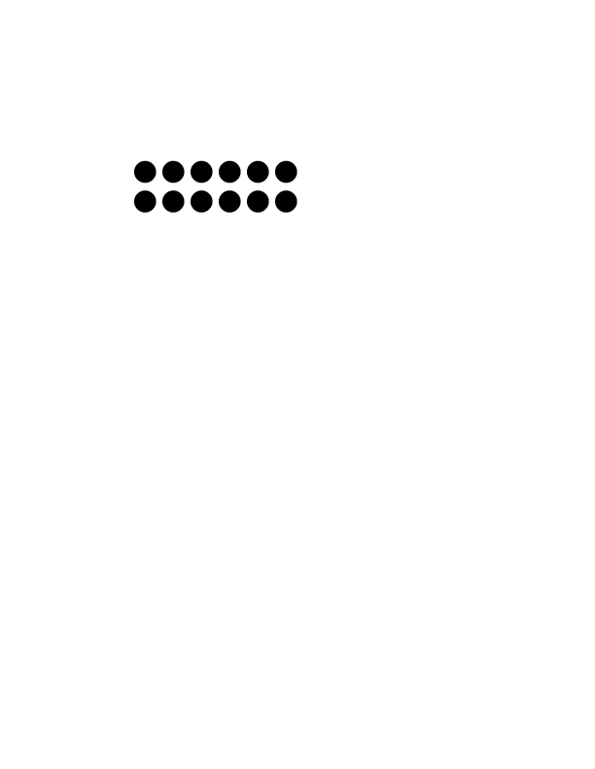
Documentation/indd/Links/Untitled-1.png
