makerjawn/oneKey/Documentation/indd/Links/tests_components0.png

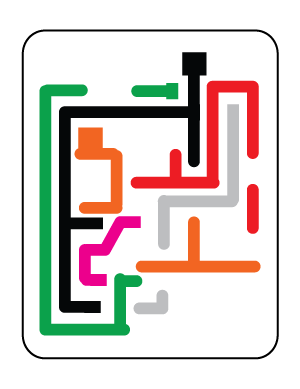
Documentation/indd/Links/tests_components0.png
