makerjawn/oneKey/Documentation/indd/Links/tests_components1.png

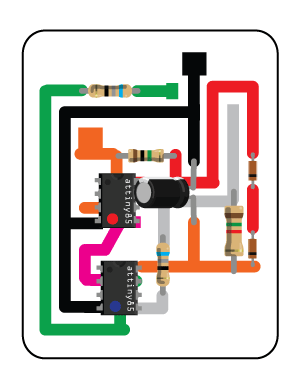
Documentation/indd/Links/tests_components1.png
