makerjawn/oneKey/Documentation/indd/Links/test_0.png

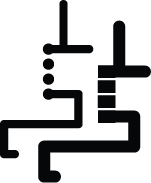
Documentation/indd/Links/test_0.png
