makerjawn/oneKey/Documentation/indd/Links/test_4.png

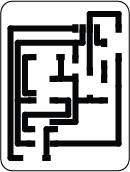
Documentation/indd/Links/test_4.png
