makerjawn/oneKey/Documentation/indd/Links/updated_test_etch_copper_top.png

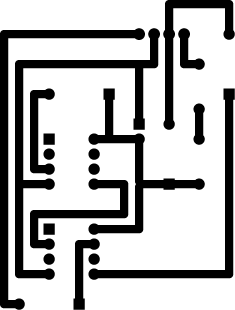
Documentation/indd/Links/updated_test_etch_copper_top.png
