makerjawn/oneKey/Documentation/indd/Links/components.pdf

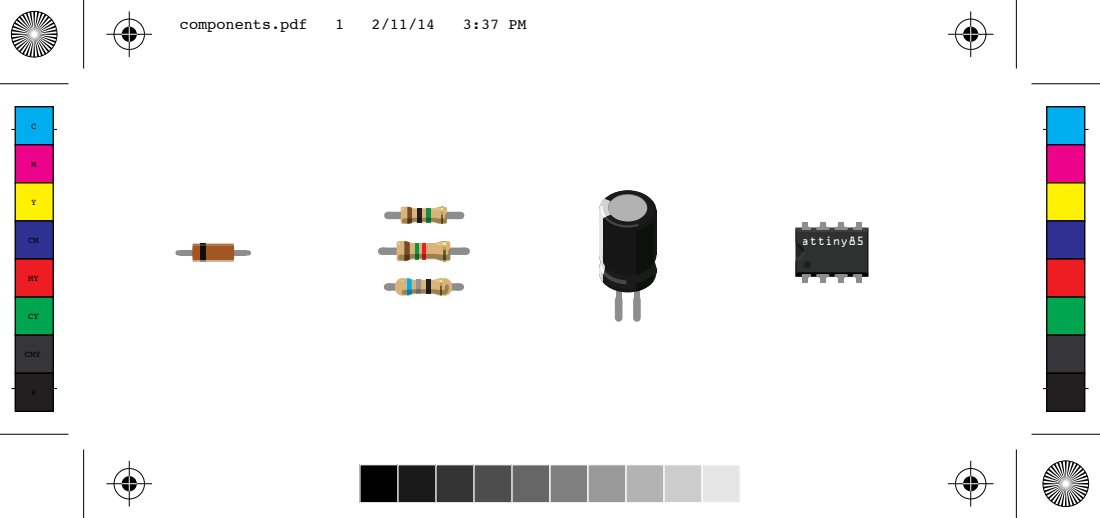
[picture p199: page 1]
attiny85; CMY; components.pdf
