makerjawn/oneKey/Documentation/Research_HID.pdf

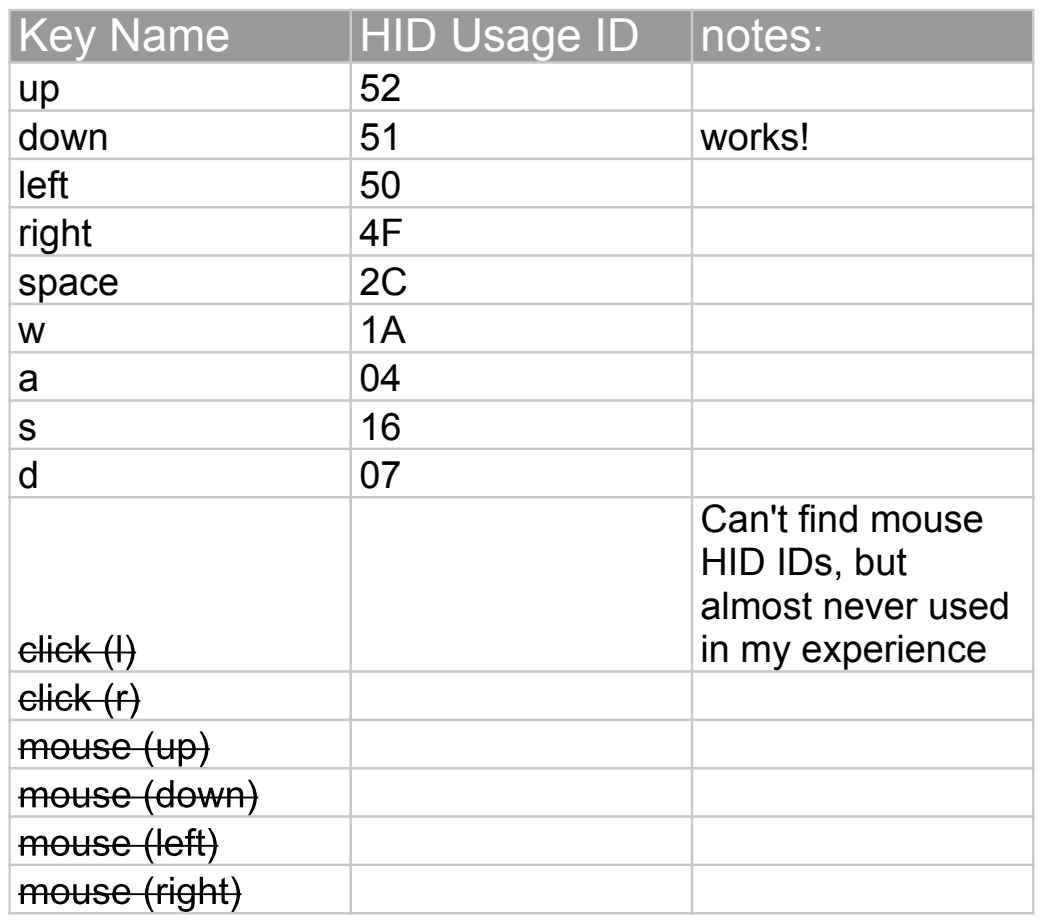
[picture p200: page 1]

Key Name | HID Usage ID | notes:
up | 52
down | 51 | works!
left | 50
right | 4F
space | 2C
w | 1A
a | 04
s | 16
d | 07
click (l) | | Can't find mouse HID IDs, but almost never used in my experience

click (r)
mouse (up)
mouse (down)
mouse (left)
mouse (right)
